oliverkirk-sudo/k230-c/project/cad/instrumented-reference/README.md

# Instrumented electrical reference, not the compact core

This frozen18-sheet variant preserves the added eight-rail voltage-monitor network and its conditional storage interlock. It has279 XML references /272 populated functional components, excluding DNP, logical edge and test-only points. CLI ERC is0, but this is only a schematic-model result. It is NOT demonstrated bootable or fabrication-ready; the qualification strap is DNP and storage is inhibited by default.

The rough dense area reservation is1231.56mm² versus1156mm² within the provisional2mm perimeter band. This topology is therefore not the selected38mm compact placement candidate. See ../integrated for the current compact candidate. No required decouplers were removed merely to improve this count.

Frozen source-generator copies are kept in frozen-generators; vendor evidence remains linked in the main project. The local review PDF/XML describe these saved bytes. Dynamic power failure, OTP, firmware, SI/PI and physical validation are not proved by ERC.
