oliverkirk-sudo/k230-c/project/cad/integrated/README.md

# 当前紧凑评审原理图 v8

打开 CMK230_Core_REVIEW.kicad_pro。18 页，246 个 XML 引用；另有 26 个排除 BOM/PCB 的电源来源声明。

全部 390 个 SoC 和 353 个存储器球位完成类型核对。最新 ERC 为 0，65 条 DDR 连接、131 个存储器供电/参考节点、62 个外露 GPIO 不变检查通过。电源声明只表达可追溯来源或底板必须提供的供电边界，不表达电压/时序已经合格。

R528 默认 DNP，存储禁止；尚未证明能启动。没有生产 PCB、叠层、半孔、SI/PI、热或实物测试。请读根目录 V7_COMPACT_REVIEW.md。

原理图内 NC 仅用于已核实不用的引脚，模拟参考类型有专门拓扑验证。VDDI 只连接稳定电容，不允许据输出类型作外供电。

本版采用缓冲复位，增加两个源参考MIPI去耦，关联NVT/晶体图纸候选封装。新提出的密闭75–85°C要求尚未满足；请读根目录V8_REVIEW.md和engineering/thermal/HIGH_TEMPERATURE_GATE.md。
