oliverkirk-sudo/k230-c/project/engineering/passive-resistor-candidates/README.md

# Remaining resistor candidates: bounded source review

2026-09-30. Audit of the high-temperature CM-K230 candidate, with 38 × 38 mm, top-only components, 140 edge pins, 1 GB LPDDR4 and 16 GB eMMC retained. The provisional 85°C enclosed-air target is **not** a verified resistor/PCB temperature. The initial source audit made no CAD/population/purchase changes. Subsequently authorized HT-DRAFT13 implements only U14 as a Schmitt OR and R33=270k; the classifications below retain the explicitly frozen pre-change input. See the current [implementation validation](../../cad/high-temp-candidate/u14-or-validation.json) for that adopted candidate.

The frozen input contains 61 resistor references: 19 already assigned precision parts and **42 unassigned positions**. The latter divide into **35 ordinary nonzero resistors, two precision startup-selection resistors and five role-specific zero links**. Three of the 42 are DNP. [Per-reference classification](per-reference-classification.json) records every value, net, candidate and remaining gate. [Calculations](static-screen.json) are reproducible with `python engineering/passive-resistor-candidates/calculate_screen.py`; they use the frozen [input extract](input-snapshot.json) and the project's static regulator bounds.

**U14 follow-on gate:** the43 kΩ R33 proposal below is a static-load correction only. [The input-slew addendum](U14_SLEW_ADDENDUM.md) finds an unclosed10 ns/V LVC input requirement and evaluates the already-reviewed AUP97 as a correctly wired Schmitt OR, with a separate270 kΩ output-pullup proposal. Do not adopt R33 alone as full acceptance of U14.

## Family, temperature and land geometry

Vishay **CRCW0201 e3**, document 20052, is a credible *layout candidate* for these ordinary values. Specify **F tolerance / K TCR**: ±1% initial and ±100 ppm/K, supported over **47 Ω–1 MΩ**. The ±200 ppm/K ±1% range is 10 Ω–10 MΩ; 1–9.76 Ω has asymmetric −200/+400 ppm/K. Do not accidentally substitute the N-code 200 ppm grade for the K-code candidate. Schema-derived ED candidates used here are CRCW02014K70FKED, CRCW020110K0FKED, CRCW020122K0FKED, CRCW020143K0FKED, CRCW020147K0FKED, CRCW0201100KFKED and CRCW02011M00FKED. Stock and lifecycle were not verified. [Vishay pp1–2](https://www.vishay.com/docs/20052/crcw0201e3.pdf)

The family specifies −55…155°C operation, 30 V limiting element voltage and 50 mW at 70°C. Its graph decreases linearly to zero at 155°C: **41.18 mW at 85°C, 29.41 mW at 105°C and 17.65 mW at 125°C**. These graph readings require the manufacturer's PCB/thermal conditions and film ≤155°C; 85°C enclosure air does not prove them. Working voltage also remains limited by √(P·R). The worst proposed ordinary full-rail DC illustration is R204 at 5.5 V across 9 kΩ: **3.361 mW**. Actual hot spots, PCB heat flow, pulses and source voltage still need review.

The source drawing was visually checked: body **0.60±0.03 × 0.30±0.03 × 0.23±0.03 mm**, two **0.28 × 0.43 mm** copper pads, **0.23 mm inner gap**, pad centers ±0.255 mm, **0.79 × 0.43 mm total copper envelope**. A 1.1 × 0.7 mm planning box provides only 0.155/0.135 mm per-side allowance beyond copper. A hypothetical 0.05 mm mask expansion plus 0.25 mm clearance instead gives **1.39 × 1.03 mm**, rounded outward to 1.4 × 1.1 mm. Neither clearance convention is manufacturer assembly approval; mask, paste, placement and inspection capability remain open. These are source dimensions, not permission to assign a generic 0201 footprint.

## Accuracy is an acceptance requirement, not a lifetime model

This report deliberately tests **±10% total resistance** for ordinary candidates. It is a required acceptance interval spanning initial tolerance, temperature, assembly, aging and environment, **not a guaranteed CRCW life specification**. Vishay permits ±(2%R+0.1 Ω) change in the 70°C/1000 h endurance test and ±(4%R+0.1 Ω) at 8000 h; 155°C/1000 h upper-category endurance permits ±(2%R+0.1 Ω), and soldering heat permits ±(1%R+0.05 Ω). These are different prescribed tests. They cannot be added and relabeled as a guaranteed arbitrary mission lifetime. At 100 ppm/K, a 20→125°C excursion alone corresponds to 1.05% resistance change. Mission duration, humidity, film temperature, mounting shift and process still need an actual acceptance plan. [Vishay pp1,3–4](https://www.vishay.com/docs/20052/crcw0201e3.pdf)

**R205/R206 are excluded from that interval.** TI's startup selection table specifies 56.2 kΩ with ±1% accuracy for 0.8 V/address 0x49. TNPW0402 supports 56.2 kΩ at ±0.1%/10 ppm/K; candidate **TNPW040256K2BYED** can use the separately reviewed source-land footprint. The existing conditional **±0.70% total** acceptance gives 55.8066–56.5934 kΩ, inside TI's 55.638–56.762 kΩ band. It remains a total mission-profile requirement, not an automatic life guarantee. [TI Table8-1 p12](https://www.ti.com/lit/ds/symlink/tps62864.pdf), [Vishay p3](https://www.vishay.com/docs/28758/tnpw_e3.pdf), [existing footprint review](../../cad/verified-footprints/passive-candidates/README.md)

## Important static checks and proposed nominal changes

Use static rail bounds 1V8 = **1.764476615–1.836094613 V** and 3V3 = **3.245129532–3.392164299 V**. Distribution drop, ripple, dynamic load, PCB leakage and supply ramps are additional requirements. Comparisons to Nexperia Schmitt thresholds below retain its **discrete 1.65 V supply test point**, rather than claiming guaranteed interpolation over the actual 1V8 rail.

| Network | Result at the stated total resistance band | Remaining interpretation |
|---|---|---|
| R527, 10 kΩ raw PG | 9–11 kΩ; conservative sink ≤379.007 µA versus U89's 400 µA point, leaving 20.993 µA. High loss ≤23.1 mV at 2.1 µA leakage; high ≥3.222030 V | Sink reserve must also cover board leakage. Common low ceiling 0.4 V gives 70 mV against tabulated VT− minimum0.47 V. PG leakage is tabulated at5 V; actual-node application remains conditional |
| R530, 100 kΩ delay-node pullup | 90–110 kΩ; 1.05 µA ×110 kΩ =115.5 mV loss; high ≥1.648977 V, **338.977 mV** above VT+ maximum1.31 V | Only U90 leakage0.3 µA and U91 input0.75 µA are counted. No SoC pin load belongs on this node. Low current <22 µA; timing and full-supply behavior remain open |
| R529, 100 kΩ inhibit pulldown | 0.75 µA ×110 kΩ =82.5 mV, leaving **387.5 mV** to the discrete0.47 V low threshold | R528 stays DNP; this does not approve enabling storage |
| R31, 10 kΩ mode pulldown | Two TMUX inputs plus one LVC input:9 µA ×11 kΩ =99 mV; **351 mV** below TMUX0.45 V VIL | Valid powered-control state; JP1 remains cold-only |
| R32, 10 kΩ global-disable pullup | Released high ≥3.137880 V with9.75 µA leakage; ≥1.137880 V margin to LVC VIH2.0 V. Sink bound <386 µA | AUP06 loaded0.39 V low leaves60 mV to TMUX VIL, still a discrete supply-point check |
| R61/R62, 10 kΩ LPDDR4 ODT_CA pulls | Micron4 µA leakage produces44 mV maximum drop; same-local-VDD2 high margin ≥231.204 mV to0.75 VDD2 | Preserve rank/ODT configuration and validate local rail distribution |

Sources: [TPS3808 p6](https://www.ti.com/lit/ds/symlink/tps3808.pdf), [TPS6282x p5](https://www.ti.com/lit/ds/symlink/tps62827.pdf), [74AUP1G97 pp6–8](https://assets.nexperia.com/documents/data-sheet/74AUP1G97.pdf), [74AUP1G17 pp5–7](https://assets.nexperia.com/documents/data-sheet/74AUP1G17.pdf), [74AUP1G06 pp5–7](https://assets.nexperia.com/documents/data-sheet/74AUP1G06.pdf), [TMUX1574 p6](https://www.ti.com/lit/ds/symlink/tmux1574.pdf), [Micron LPDDR4 Tables153/170 pp223/234](https://www.mouser.com/datasheet/2/671/200b_z00m_sdp_ddp_auto_lpddr4_lpddr4x-3193603.pdf)

**Propose R563–R570 = 43 kΩ, replacing 47 kΩ.** Micron permits DAT pullups10–50 kΩ. Existing47 kΩ at±10% reaches **51.7 kΩ**, failing the upper bound by1.7 kΩ. Proposed43 kΩ spans **38.7–47.3 kΩ**, leaving2.7 kΩ upper reserve. R562 CMD22 kΩ spans19.8–24.2 kΩ within4.7–50 kΩ; R34 reset10 kΩ spans9–11 kΩ within4.7–50 kΩ; R573 DS47 kΩ spans42.3–51.7 kΩ within10–100 kΩ. These are resistance-window checks, not complete bus timing/logic acceptance. [Micron eMMC Table13 p27](https://e2e.ti.com/cfs-file/__key/communityserver-discussions-components-files/234/EMMC_5F00_DATASHEET.pdf)

**Propose R33 = 43 kΩ, replacing 10 kΩ.** The netlist confirms only R33, **U14.Y pin4 and U13.EN pin13** on DISABLE_OR_TF. At125°C, TI's3 V/16 mA LVC output row allows VOL0.5 V, exceeding TMUX VIL0.45 V; the present10 kΩ load is too large for the stronger light-load guarantee. With43 kΩ±10%, worst current is3.392164 V/38.7 kΩ +2 µA = **89.653 µA**, below the **100 µA** test row that guarantees VOL≤0.1 V over1.65–5.5 V. This leaves **350 mV low margin** and10.347 µA additional sink-load reserve. With a valid high output, VOH≥VCC−0.1 V gives≥3.145130 V, or **1.945130 V margin** to TMUX VIH1.2 V; the only sink input is2 µA and the pullup helps.

The LVC source explicitly lists Ioff≤25 µA at125°C, VCC=0 and VI/VO=5.5 V. If that is accepted as a bound at this actual3V3 node, adding2 µA TMUX leakage gives a hypothetical released high≥**1.968030 V**, margin768.030 mV. That voltage extension is conditional. U14 VCC and the R33 pullup are physically on the **same VDD_3V3 net**; an independently live pullup with U14 unpowered is not a normal stable circuit state. Neither Ioff nor this calculation establishes behavior during their common ramp, rail collapse or partial power. The proposed correction closes the stated **valid-supply** source-table margin. [TI RevW pp6–7, visually checked](https://www.ti.com/lit/ds/symlink/sn74lvc1g32.pdf), [TMUX RevC p6](https://www.ti.com/lit/ds/symlink/tmux1574.pdf)

## Roles that still need electrical closure

- **R216–R219, 4.7 kΩ private I2C:** at±10%, R=4.23–5.17 kΩ. TPS62864 specifies VIH1.0 V, VIL0.4 V and SCL/SDA leakage0.2/0.1 µA. Regulator-input high margins are respectively **0.763443 V−5170Ω·Iunknown** and **0.763960 V−5170Ω·Iunknown**, where Iunknown includes PMU/board sink leakage and any internal pulldown. The official pinout establishes PMU type and AVDD1P8_LDO domain for all four pads; it does not prove general-IO numerical limits apply. Even provisionally using generic K230 VOL0.45 V leaves **−50 mV** against TI's0.4 V input ceiling. TI's2 mA SDA/SCL rating is an **absolute maximum**, not a guaranteed VOL/IOL drive specification. Complete bidirectional DC margin is unresolved. Ideal30–70% RC ceilings at5.17 kΩ are228.3 pF/68.48 pF/27.39 pF for1000/300/120 ns; actual bus capacitance, firmware timing and internal pulls must be verified. [TI pp5–8](https://www.ti.com/lit/ds/symlink/tps62864.pdf), [Canaan pinout](https://kendryte-download.canaan-creative.com/developer/k230/HDK/K230%E7%A1%AC%E4%BB%B6%E6%96%87%E6%A1%A3/K230_PINOUT_V1.2_20240822.xlsx), [K230 manufacturer-authored datasheet pp29–30](https://atta.szlcsc.com/upload/public/pdf/source/20240304/CED0BDC8B8BEDC72BFC23F1C8A2ED83A.pdf), [TI RC equation](https://www.ti.com/lit/an/slva689/slva689.pdf)
- **R203:** released-high leakage drop is66 mV using five0.1 µA EN loads plus0.1 µA PG leakage. Low current is modest, but the published PG VOL0.4 V equals downstream EN VIL0.4 V, giving **zero guaranteed DC noise margin**. Resistor tolerance alone does not resolve it. **R204** input-leakage drop is1.1 mV at its11 kΩ maximum. [TPS6282x p5](https://www.ti.com/lit/ds/symlink/tps62827.pdf), [TPS62864 p6](https://www.ti.com/lit/ds/symlink/tps62864.pdf)
- **R43:** known0.75 µA Schmitt leakage gives371.977 mV high margin to the discrete1.31 V threshold; C45, carrier and PCB leakage must fit the remaining **3.382 µA** static sink budget and the RC timing requirement
- **R41/R42:**1 MΩ is supported by the100 ppm family, but crystal startup/gain/drive are not resistance-range checks. **R44–R47** boot sampling/internal pulls/carrier ownership and **R402** PMU pin limits remain open; preserve R45/R47 DNP
- **R571/R572:** retain as physical candidates only. Exact eMMC CLK/K230 strobe input limits and disabled-switch states need closure. A provisional10 µA K230 leakage assumption across R572's110 kΩ would raise its node to1.1 V, above0.35×1V8min≈0.618 V; the existing100 kΩ cannot be called a guaranteed low from that generic model

## Zero links remain role-specific

Keep **R220 WSL060300000ZEA9** and **R561 WFZ040200000ZE66** under their [existing independent power-link reviews](../mechanical/passive-small-parts-review.md). Do not substitute commodity0201.

**R221** may retain CRCW02010000Z0ED as a *conditional* layout option: the Canaan50 mA VDD3P3_SD budget would cause2.5 mV drop and0.125 mW at50 mΩ. This is a SoC supply branch, not the TF card's main feed. The CRCW jumper's1 A rating is explicitly at70°C; hot resistance/current, peak/inrush and branch drop remain unqualified. Do not infer a125°C current rating from a resistor power graph alone.

**R528**, still DNP, is a low-current logic strap: if deliberately fitted, the known100 kΩ pulldown/input path draws at most≈21.151 µA at the stated corners. CRCW02010000Z0ED is a role-specific physical candidate; populating it would still require the separate boot-voltage qualification decision. **R401** remains selection-deferred until actual PMU input/internal-pull current, firmware input ownership and local ramp are checked. A0 Ω connection to its own domain does not permit firmware to drive that pin low.

This audit establishes candidate family compatibility, source land dimensions and bounded calculations. It does not establish full-board fit, full-supply logic, timing, assembly capability, lifetime, thermal performance or production qualification.
