oliverkirk-sudo/k230-c/project/engineering/mechanical/passive-hot-enclosure-review.md

# Passive and regulator thermal constraints in the sealed enclosure

2026-09-30. The user reports a sealed enclosure with a 75–85°C maximum, while the design lead is clarifying whether this refers to surrounding air or a component surface. This distinction is unresolved. It does not establish a safe local capacitor, inductor or regulator temperature.

**Do not adopt the conditional X5R area optimization under this unresolved condition.** The recovered smaller X5R parts are archived research candidates only. Their 85°C component-temperature limit is not an 85°C ambient allowance with self-heating. Retain the X7R/125°C review path, and evaluate actual hot spots before a package reduction.

## Source-backed limits

| Component group | Manufacturer limit or condition | Consequence for this module |
|---|---|---|
| TPS62864 CPU/KPU converters | Recommended junction range −40…125°C; continuous 4 A above 105°C junction reduces lifetime | If local air is 85°C, only 20°C junction rise reaches the published lifetime-warning threshold at continuous 4 A; 40°C rise reaches recommended maximum. Actual load and duty cycle matter. |
| TPS6282xA fixed converters | Recommended junction range −40…125°C | The 150°C absolute maximum and thermal shutdown are not continuous design targets. At 85°C local air the recommended-range budget is 40°C, before margin. |
| Murata DFE201612E inductors | −40…125°C **including self-heating**; ΔT≤40°C | 85°C local air plus the full specified rise reaches 125°C with no remaining temperature margin. Rated thermal currents were measured on Murata's six-layer test board, not this crowded module. |
| Murata DFE201610E inductors | 125°C operating limit including self-heating; current criteria differ for inductance drop and temperature rise | L24–L26's 4.8 A inductance-drop number must not replace the 3.6 A thermal criterion. Keep thermal qualification open. |
| Coilcraft XEL3520 | Up to 125°C ambient with its stated 40°C-rise Irms condition; maximum part temperature 165°C | This has a different temperature definition from Murata's 125°C part limit. TI-listed 0.47 µH XEL3520-471MEC remains a possible L21 candidate, subject to application losses, board cooling and 2.0 mm height. |
| BLM15PX121SN1D ferrite | 2.0 A at 85°C derated to 1.1 A at 125°C; recommended copper width depends on foil thickness/current | Follow current-temperature and copper constraints at actual local temperature. Nine nominal impedance matches do not establish nine acceptable hot-spot placements. |
| X7R MLCC candidates | Nominal temperature characteristic extends to 125°C | This leaves temperature range to assess, not a guarantee of effective capacitance under combined DC bias, AC ripple, tolerance, aging and production variation. |

TI gives materially different junction-to-ambient thermal figures on JEDEC and EVM boards: TPS62864 91.8 versus 56.5°C/W; TPS6282x 129.5 versus 71.4°C/W. These are evidence that PCB construction matters. Do not use either value as the measured thermal resistance of the 38×38 mm sealed module or derive an approved continuous-current limit from it.

## Changes that remain conditional

- Replacing L21's low-resistance XFL4015 with DFE201612E-R47M can save 13.96 mm² in a reservation scenario, but raises maximum room-temperature DCR from 8.36 to 26 mΩ. At an illustrative 4 A DC, the latter contributes 0.416 W before ripple/AC loss and hot-DCR increase. This is not an accepted trade in the sealed enclosure.
- The alternative TI-listed XEL3520-471MEC saves only 3.94 mm² with the conservative reservation and has 10.85 mΩ maximum DCR, much closer to the original. Its thermal-current figures still require real-board validation; no replacement is approved here.
- A single large input capacitor on a TPS6282xA rail may satisfy the 3 µF effective-capacitance floor but still fail ripple-current or thermal requirements. The optional single-input area scenario therefore needs input-ripple, ESR heating, hot-loop and load-transient review. It is not a recommendation to remove parts merely to fit.
- Do not infer that the memory devices' 85°C case-temperature limit qualifies them at 85°C enclosure air. The lead owns memory grade/package selection and any resulting BGA envelope changes.

## Concrete next evidence needed

Establish the temperature reference point and duration, actual rail continuous/peak loads, enclosure heat path and final board stackup. Then bound or measure component surface/junction temperatures under simultaneous worst-case workload. Capacitance release requires a warranted or qualified combined-condition minimum rather than a typical DC-bias curve multiplied by unverified margins. Placement must preserve the hot loops and local bypass distances, even when rectangle area sums are favorable.

Sources visually checked: [TPS62864 datasheet](https://www.ti.com/lit/ds/symlink/tps62864.pdf), p5; [TPS6282x datasheet](https://www.ti.com/lit/ds/symlink/tps62827.pdf), p4; [Murata DFE201612E specification](https://search.murata.co.jp/Ceramy/image/img/P02/J%28E%29TE243A-0006.pdf), pp2/4/7; [Coilcraft XEL3520](https://www.coilcraft.com/getmedia/585e5286-b75b-4755-99e9-56d067dcf62b/xel3520.pdf), p1; Murata BLM15 specification and exact capacitor sources are linked with hashes in the companion passive reports. All manufacturer originals remain outside the distributable project.
