oliverkirk-sudo/k230-c/project/engineering/power/POWER_DESIGN_CN.md

# 六路电源候选实现与剩余工作

已落实6个降压器，CORE、CPU、KPU分开；两路可调CPU/KPU均0.8V冷启动。没有为区分I2C地址而提高冷启动电压。完整针脚矩阵与Ti资料复核通过，但不是硬件或热审核。

## 固定轨
- CORE：TPS62827A，4A；33.2k/100k、0.6V基准得到0.7992V
- DDR IO：TPS62826A，3A；84.5k/100k得到1.107V，处于1.1V域的规格范围，须计入公差/纹波
- 1.8V：TPS62825A，2A；200k/100k得到1.8V
- 3.3V：TPS62826A，3A；453k/100k得到3.318V
这些是名义值。0.1%分压电阻不能消除稳压器基准误差。采用厂商所述100k下臂对应120pF前馈电容；0.47µH参考电感、47µF名义输出电容及输入2×10µF。有效输出必须≥10µF、有效输入≥3µF，不能用丝印容量代替带偏压/温度/公差的实值。

## CPU/KPU动态轨
两路TPS628640BYCGR，各4A，56.2k 1%启动电阻，均0.8V及地址0x49。0.24µH参考电感、3×22µF输出、2×10µF输入；有效输出≥30µF、输入≥8µF。开关SW三球属于同一内部输出，库中C1为power_out、C2/C3为passive表示同一物理驱动，矩阵强制三球同网，不是三路稳压器并联。

两条独立软件I2C总线避免地址冲突：CPU用GPIO65/66，KPU用GPIO67/69，各有1.8V上拉4.7k；它们均未占用140针里的GPIO2–63。还必须完成PMU pad复用、屏蔽相应唤醒源、避免关机驱动重占，以及真正开漏的方向切换。现BSP的write(1)不能直接当成开漏释放；见internal-pmu-i2c-review.md。尚未提供可直接刷入的调压固件。

VSET/PG是故障时高至VIN、正常由启动电阻拉低的复用引脚，与通常开漏PG相反。图中仅连接启动电阻，不加载为常规PG控制。新增负载或过大电容会影响启动电压/地址采样。

## 顺序与滤波
CORE的开漏PG由100k拉到VIN_5V，并控制其余降压器EN，Ti明确支持此类顺序连接；它不是完整的所有电源正常控制器。

RTC与PMU LDO两个SoC电源脚改为同一个AVDD1P8_PMU滤后网络，避免两个独立滤波支路的上升先后不确定。CORE先于1.8V/3.3V的设计路径已经画出，但板级上升/掉电/棕断、CPU/KPU状态、系统复位和存储开通仍要统筹。

DDR CORE通过最大50mΩ的0Ω连接，400mA时可产生20mV压降；再叠加基准/电阻误差、走线和纹波，必须仍高于0.744V。模拟域120Ω@100MHz磁珠给出了最大直流电阻约束，但这不是噪声/谐振验证。近芯片本地去耦另页给出初始分配，正面放置与回流路径尚未设计。

## 文档与验证
TI：https://www.ti.com/lit/ds/symlink/tps62827.pdf 及 https://www.ti.com/lit/ds/symlink/tps62864.pdf 。实际工作点的电感峰值/饱和、MLCC有效容量、环路、散热、5V输入裕量和38mm布局都没有测量或仿真通过。完整PG/复位/存储开通逻辑未冻结，不能据此制板。
