oliverkirk-sudo/k230-c/project/engineering/storage/SELECTOR_DESIGN_CN.md

# 存储二选一：已连接的候选隔离子电路

用户已允许eMMC/TF二选一。默认16GB eMMC，断开全部电源后设置模式；不热切换，不占用或重定义140针中的GPIO。这里落实了隔离子电路，整体核心板仍未完成。

## 新文件与检查
- `cad/storage/CMK230_Storage_Selector_CANDIDATE.kicad_sch`：可编辑KiCad子电路，3个真实型号多路开关、1个OR门、模式焊接跳线、偏置和去耦
- `switch-pin-net-matrix.csv`与`switch-netlist.xml`：71项器件针脚/网络对应
- `switch-connectivity-test.json`：4种MODE/全局禁用状态通过静态导通图检查；不是SPICE、时序、SI或实测
- CLI成功导出原理图、网表；预览已目视检查。独立子电路ERC为30错误/0警告：28个仅有本页端点的未接外围标签、2个尚无上游供电源的网络。这些没有通过NC或PWR_FLAG掩盖

## 电路选择
U11/U12/U13采用TMUX1574RSVR候选（RSV UQFN针号，不能套用PW/DYY针号）。U11/U12切换CLK、CMD、DAT0..3；U12另一路把eMMC复位端在eMMC模式连至主控复位源、TF模式钳至GND。该复位不作为总线隔离成立的前提，因eMMC复位功能还涉及器件配置。

U13负责DAT4..7：SEL固定0，其EN由U14输出GLOBAL_DISABLE OR MODE_TF。TF模式整颗U13关闭，从而隔离全部高位数据线；其未使用B端按厂商建议接地，不会在正常TF模式将主控输出接地。U12剩余一路三端均接地。

JP1默认开路，R31=10k下拉使MODE_TF=0，选eMMC。全部断电后闭合JP1得到TF模式。R32/R33使禁用信号默认高。R34=10k从eMMC_RSTN上拉到VEMMC_IO，避免全局禁用时复位浮空；VEMMC_IO须与器件IO电源一致。TF复位钳位的标称电流为0.18mA或0.33mA，不是含公差的最大值。U14候选SN74LVC1G32DBVR采用3.3V逻辑供电；上游GLOBAL_DISABLE必须是与此域兼容的硬件信号，不能假定任意1.8VGPIO可直接驱动。C31–C34各100nF，最终位置/型号仍待布局。

eMMC VCC和VCCQ在两种模式都保持供电，避免新增电源开关和未供电器件反灌路径；TF模式11条与主控相关路径全部隔离。代价是eMMC待机功耗。外部TF的3.3V供电和上拉由底板合同处理；未选分支仍可能带电，因此必须遵守开关电源、信号绝对额定值及上电顺序。

## 厂商证据与约束
TI开关资料：https://www.ti.com/lit/ds/symlink/tmux1574.pdf
它是双向模拟开关，不是电平转换器；3.3V供电可承载所需1.8/3.3V信号。断电保护限值3.6V不能当作任意过压保护。2GHz典型带宽、导通电容7.5pF典型/12pF最大、导通电阻2Ω典型/4.5Ω最大，不等于本板HS200已合格。仍需主控到存储完整通道的眼图、延迟、偏斜、负载和训练验证。
TI逻辑门资料：https://www.ti.com/lit/ds/symlink/sn74lvc1g32.pdf

## 必须在BootROM执行前解决的门槛
GLOBAL_DISABLE目前明确是未完成的硬件集成输入，不是已经存在的控制器。不能等U-Boot运行后再开通用来加载U-Boot的存储路径；那会循环依赖。需要在ROM第一次访问存储前由已验证的硬件电源/复位/电压策略释放开关。

K230的VDD3P3_SD按资料仍是3.3V电源，不能切换成1.8V。运行期软件通过HOST_CONTROL2/PHY设置1.8V信号，不等于改变外部电源。TRM控制器复位字段为3.3V，但未证明ROM首次驱动时仍是这个状态；ROM可能先修改它。BOOT标签在资料间有差异，不能把MODE_TF直接绑到BOOT0/BOOT1。

当前HS200候选中eMMC VCCQ=1.8V、TF起始3.3V；若初期驱动电压不匹配，可能损坏或不能启动。因此此子电路尚不可投板运行。需确认ROM最早电压/启动选择和异常复位行为，随后完成硬件GLOBAL_DISABLE发生电路。

## 较保守性能路线的评估（尚未选用）
所选eMMC支持3.3V VCCQ。固定3.3V并取消HS200、按8bit HS52设计，可降低“主控初期3.3V直达固定1.8V器件”的风险。接口原始传输上限由约200MB/s降至约52MB/s，实际文件性能不等于此上限。此路线是性能变更，需要用户选择，当前没有偷偷采用。ROM若改成1.8V后访问3.3V器件仍可能失败，因此也不是绕过ROM验证的万能解决方案。

## 后续释放条件
核实ROM/PHY及异常复位 → 完成上游电源/复位/禁用发生器 → 确认两种启动镜像与模式对应 → 完整器件封装审核 → 总线SI与HS200/SD速度测试。当前未生成此子电路PCB、器件贴片位置或可制造Gerber。

独立复核确认：RSV及DBV针号正确；原69项网络与新增R34两项一致；总71项匹配KiCad导出网表，四种模式/禁用逻辑均通过。GLOBAL_DISABLE需要3.3V有效逻辑（U14高门限至少2.0V）或额定耐3.3V的开漏源，不能接1.8V推挽输出。
