oliverkirk-sudo/k230-c/project/COMPACT_README.md

# v12 精简评审包

这是完整v12存档的精简副本，用于直接下载。电路、引脚、BOM候选、KiCad可编辑文件、工具、原始出处/哈希、回归结果、几何审计及未完成事项均保留。当前HT-DRAFT13原理图PDF保留。

主要省略重复的历史PDF、试验渲染和图片；逐个文件及原始哈希见compact-content-manifest.json。保留的GUI截图是原来的v9高温分支/v11局部eMMC试验，不能当作HT-DRAFT13的新GUI测试。完整v12存档保留全部图片证据。

某些历史冻结清单包含已省略图片，其完整清单校验应在完整存档中执行；不要把精简包缺少渲染当作新的CAD错误。精简内容没有更改任何原始工程字节。它仍不能生产：R528默认DNP、存储禁止，主PCB未完成放置/布线，DDR现有搜索被拒绝。请先阅读V12_CORE_REVIEW.md。
