oliverkirk-sudo/k230-c/project/docs/release-gates.md

# 释放门槛与验证计划

当前：D0接口/架构评审；没有内部原理图完成、布线完成或制造通过。

## G1 电气兼容合同
- 140个接口除名称外，逐针填写方向、电压、绝对最大值、默认上下拉、启动复用、内部串阻/ESD、电源掉电行为及底板要求
- 优先解决6组BANK_VDDIO、两组输出电源、BOOT0/1、RSTN、USB ID/VBUS感测、模拟输入/输出
- 审核模块符号BANK5_IO62/63等原始命名，不能擅自改针号；SoC球号需官方引脚表/原理图双人核对
- 样品连续性/测量可补充证据，但带电测量须使用限流和相应探头；未知bank禁止直接注入3.3V

## G2 可执行内部原理图
- 完整料号/最新资料、K230/DRAM/eMMC逐球连接矩阵和封装尺寸通过审核
- 电源负载、瞬态、效率、热、电源输出给底板的预算与裕量完成；不是仅通过ERC
- 上电/掉电/棕断顺序、默认启动态、DVFS接口完成；禁止未受控并联稳压输出
- DDR训练参数与物理换位一致，bootloader/BSP版本冻结
- 每个电源脚/去耦/NC/保留脚有明确处置；ERC完成且所有剩余告警有签署解释

## G3 布局与制造
- 确认实际板厚、半孔孔径/环宽/镀层、边缘位置、公差、阻焊/焊膏、表面处理、拼板、测试和钢网
- 板厂确认叠层与阻抗；BGA逃线和同面去耦可行；背面元件数=0
- 审核DDR封装延迟+PCB延迟、通道内交换、参考面、过孔数和串扰；电源完整性与热审核
- 原理图与PCB网表一致；DRC、间距、铜到边缘、半孔专用工艺审核；不能将底板SMD焊盘直接用于核心板制板
- 完成独立设计审查后才生成Gerber/钻孔/BOM/CPL，现包未提供这些文件

## G4 样板上电与功能
1. 不装底板先检查外观、短路、BGA焊接与电源对地阻值；限流分阶段上电
2. 示波器同时记录CORE/1.8/3.3/DDR/RESET等关键电源与释放关系；确认峰值和纹波，不能只用万用表
3. 确认24MHz/RTC时钟、串口恢复/USB下载、BOOT选择和复位重复性
4. 验证1GB容量与地址边界；全地址/数据模式内存压力测试、冷热启动、目标频率和温度覆盖；记录训练日志
5. 验证eMMC容量识别、EXT_CSD、HS200、读写完整性、擦写/分区与断电恢复；容量显示与出厂预留区分开
6. 用原CM-K230底板逐项检查GPIO-bank电平、UART/I2C/SPI/SD、USB host/device、各CSI/DSI通道、ADC/audio及供电负载
7. 对比原板启动、接口行为、异常掉电/复位、长时AI负载和热。通过后再声称“功能兼容”

## 本包已运行的检查
- 140/140针脚：原符号与底板PDF独立一致；原始重复电源名称保留
- 140个底板焊盘被KiCad读取；原始位置/大小/旋转数字转换保存
- KiCad9接口原理图SVG导出成功，已目视检查；这不是内部原理图ERC
- PCB只有四条38mm边界及警示文字，没有铜/孔/器件/连线；不是DRC合格产品

- 本次接口黑盒ERC实际输出139条未连接引脚错误、0警告；这是未接内部电路的草稿，不是ERC通过。未以NC标记掩盖这些未完成连接。
