oliverkirk-sudo/k230-c/project/engineering/CORE_AUX_CN.md

# K230时钟、复位与启动偏置：参考电路落图

新增`cad/core-aux/CMK230_Clock_Reset_REFERENCE.kicad_sch`，15个器件、37项针脚/网络；KiCad导出网表逐项匹配，独立片段ERC为0错误/0警告，预览已检查。U1仅表示7个已知系统球，不是完整390球SoC，不能据此宣称核心板ERC通过。

## 已按一手参考落实
Canaan CanMV-K230 V1.0_2023-09-15原理图第1页（不同于01Studio同名板第1页）：RTC B12/A12，24MHz B8/A8，RSTN B9，BOOT0 C8，BOOT1 C9。
- 两组晶体反馈电阻参考1MΩ；四个晶体负载电容参考12pF
- 24MHz四脚参考连接：1/3晶体端，2/4地；最终器件封装必须逐脚一致，不能仅凭“3225”选封装
- RTC采用两脚无源晶体网络
- RSTN参考上拉100kΩ至1.8V、100nF至GND；保留模块外部复位同名网络

## 本项目的明确差异
通用CanMV板的默认启动偏置不能直接当成CM-K230。本片段提出BOOT0低、BOOT1高，对应硬件指南的MMC0基线；相反方向偏置电阻DNP。外部BOOT接口仍保留。此提案不解决BootROM对SD/eMMC电压和类别的实际识别，不把MODE_TF自动连接到BOOT引脚。

## 参数可留待布局/验证，不假装已经冻结
晶体完整料号尚未冻结。官方LP4参考BOM的候选是YXC X322524MOB4SI与Epson X1A000141000500；更换来源或后缀须复核CL、ESR、驱动等级、容差和温度。Epson官方系列资料：https://download.epsondevice.com/td/pdf/app/FC-135R_en.pdf 。不能用频率一样代替这些参数相同。

12pF是参考值，不是新板已校准值。对两个负载电容，近似CL=C1×C2/(C1+C2)+寄生电容；两个12pF只贡献约6pF，剩余取决于封装/引脚/布线。实际布局后按所选晶体负载、寄生估算及测量调整，检查负阻裕量、起振、频率与温度。

100k/100nF的RC时间常数为10ms，但实际复位释放时刻取决于阈值和供电上升过程。它不是多电源PG监控器，不能代替独立电源顺序/棕断设计。

## 仍需补全
K230其余383球、所有电源/地及去耦、未使用/测试球的处置、DDR/接口其他单元及板级连接还没有在本片段中实现。后续合并必须将片段U1统一为完整SoC多单元符号，不能把这些独立评审页当成多个K230。

补充源区分：Canaan版本的RTC有1MΩ反馈电阻R1，01Studio版本的RTC图没有画此电阻。本工程RTC1MΩ来自Canaan版本；24MHz反馈两版均有。Y2具体厂家候选的全温度/老化精度和85°C等级仍需重新审查，不能由初始±10ppm推断总误差≤20ppm。
