oliverkirk-sudo/k230-c/project/engineering/erc-triage-v5.md

# CM-K230 remaining ERC triage, v5 review baseline

Date: 2026-09-30 UTC. Scope: read-only electrical-rule triage and manufacturer/source review. This review did not edit CAD, generators, electrical pin types, NC markers, or ERC exclusions, and added no PWR_FLAG.

## Latest export reconciliation (v6)

The newer export **2026-09-30T03:58:42-0700** was separately read after source-backed pin dispositions, traced source modeling, and pin-type corrections. It contains **14 violations: 13 errors and 1 warning**. Exact current records are in `erc-triage-v6-current.csv`; source hashes/counts are in `erc-triage-v6-current-summary.json`.

The former 19 passive-source ERC errors are now addressed with traceable CAD-only source declarations after a verified upstream-connection graph. Those were ERC-model semantics, not unresolved wiring. Qualification gates remain separately tracked. No declaration was added to VEMMC_IO or the six bank nets. Accurate host-strobe input typing exposes one additional real input-drive error; it shares the already known strobe disposition with the dangling label.

| Current endpoint | Actual issue | Recommended disposition |
| --- | --- | --- |
| U1.B6 MMC0_STROBE | warning / global_label_dangling / SPEC | Retain warning until earliest boot/reset pad policy is established. No fabricated connection to H5, arbitrary grounding, or intrinsic-NC type. |
| U1.B6 MMC0_STROBE | error / pin_not_driven / SPEC | Retain warning until earliest boot/reset pad policy is established. No fabricated connection to H5, arbitrary grounding, or intrinsic-NC type. |
| U1.B11 GPIO70/OUT0 | error / pin_not_connected / SPEC | Keep unresolved until an explicit PMU startup or independently justified bypass/isolation strategy is selected and proved. Verify private regulator-control GPIO access, reset, wake and power-off paths. Do not apply blanket unused flags or arbitrary bias changes. |
| U1.C10 GPIO64/INT0 | error / pin_not_connected / SPEC | Keep unresolved until an explicit PMU startup or independently justified bypass/isolation strategy is selected and proved. Verify private regulator-control GPIO access, reset, wake and power-off paths. Do not apply blanket unused flags or arbitrary bias changes. |
| U1.C11 GPIO71/OUT1 | error / pin_not_connected / SPEC | Keep unresolved until an explicit PMU startup or independently justified bypass/isolation strategy is selected and proved. Verify private regulator-control GPIO access, reset, wake and power-off paths. Do not apply blanket unused flags or arbitrary bias changes. |
| U1.C12 GPIO68/INT4 | error / pin_not_connected / SPEC | Keep unresolved until an explicit PMU startup or independently justified bypass/isolation strategy is selected and proved. Verify private regulator-control GPIO access, reset, wake and power-off paths. Do not apply blanket unused flags or arbitrary bias changes. |
| U1.H6 VDDIO_BANK3 | error / power_pin_not_driven / SPEC | Resolve module/carrier supply ownership, permitted bank voltage and sequencing before adding any internal rail tie. Preserve six distinct banks; do not force all to 3.3 V just to silence ERC. |
| U1.K7 VDDIO_BANK1 | error / power_pin_not_driven / SPEC | Resolve module/carrier supply ownership, permitted bank voltage and sequencing before adding any internal rail tie. Preserve six distinct banks; do not force all to 3.3 V just to silence ERC. |
| U1.M7 VDDIO_BANK4 | error / power_pin_not_driven / SPEC | Resolve module/carrier supply ownership, permitted bank voltage and sequencing before adding any internal rail tie. Preserve six distinct banks; do not force all to 3.3 V just to silence ERC. |
| U1.R11 VDDIO_BANK2 | error / power_pin_not_driven / SPEC | Resolve module/carrier supply ownership, permitted bank voltage and sequencing before adding any internal rail tie. Preserve six distinct banks; do not force all to 3.3 V just to silence ERC. |
| U1.D8 ANA_TS_VTEST | error / pin_not_connected / UNUSED | Leave open with ERC error until reviewer accepts unused-output disposition. If accepted, document this particular output and retain output/functional type; do not ground or mark intrinsic NC. |
| U1.R13 VDDIO_BANK0 | error / power_pin_not_driven / SPEC | Resolve module/carrier supply ownership, permitted bank voltage and sequencing before adding any internal rail tie. Preserve six distinct banks; do not force all to 3.3 V just to silence ERC. |
| U1.R15 VDDIO_BANK5 | error / power_pin_not_driven / SPEC | Resolve module/carrier supply ownership, permitted bank voltage and sequencing before adding any internal rail tie. Preserve six distinct banks; do not force all to 3.3 V just to silence ERC. |
| U3.C6 VDD | error / power_pin_not_driven / REAL | Complete the VCCQ feed only after cold-mode/first-drive voltage policy is proved. The selected HS200 mode requires 1.8 V VCCQ; do not simply connect 3.3 V or a power flag. Retain the separate fixed 3.3 V flash supply. |

The final count must be re-exported if D8 is subsequently accepted as an unused output or any other endpoint changes. The original 51-row baseline below remains fully accounted for and is not the current unresolved count.

## Result

Every one of the baseline **51 violations (50 errors, 1 warning)** is listed below and in `erc-triage-v5.csv`. This is a frozen review of the **post-eMMC-supply-correction, pre-unused-pin-disposition** export at **2026-09-30 03:51:17-0700 (10:51:17 UTC)**. Later generator runs change UUIDs and may implement the dispositions; the hashes below identify exactly what was reviewed. Do not present this baseline count as a newer export's result.

| Primary class | Count | Meaning |
| --- | ---: | --- |
| REAL | 1 | Actual missing electrical source: corrected eMMC VCCQ/VEMMC_IO |
| UNUSED | 20 | Source-backed unused-pin classifications, with D8 unused-output reviewer acceptance retained |
| POWER | 19 | An explicit source/return path exists across passive elements or the external edge contract; ERC cannot propagate power_out through those boundaries |
| SPEC | 11 | Six carrier bank supply contracts, four PMU startup/isolation endpoints, and host strobe reset-time input policy |

The 20 UNUSED entries are **9 balls marked NC in both LP3/LP4, 5 LP3-functional balls unused in LP4, 4 unused rank1 CS/CKE functions, D8 analog output, and H5 HS400 output**. “UNUSED” is a review classification, not a statement that all are already annotated or approved. D8 unused-output acceptance remains open in this baseline. All four PMU endpoints are SPEC, because a default pull-down does not create the documented cold-start event or demonstrate the required domain-isolation transition. The separate MMC0_STROBE warning remains SPEC because its reset bias is not proved safe by runtime firmware.

## Highest-consequence findings

### eMMC rail-name reversal was real and is corrected in this snapshot

The original inspected v4 generator assigned Samsung **VDD to VDD_3V3** and **VDDF to VEMMC_IO**. Exact Samsung part-family documentation, page 4 table 1 and page 5, specifies **VDD = VCCQ (interface/controller)** and **VDDF = VCC (flash)**. The intended fixed-1.8-V HS200 I/O mode therefore made that mapping erroneous. The parent corrected the mapping during this review; this frozen XML now puts C6/M4/N4/P3/P5 on VEMMC_IO and E6/F5/J10/K9 on VDD_3V3. The corrected VEMMC_IO net is still source-less. Merely correcting names or adding power flags cannot make storage operational.

### H5 is legitimately unused for HS200; B6 still needs a pad policy

Samsung's H5 Data Strobe is a device-generated HS400 output. It is not required by the selected K230 HS200 path. H5 should not be wired around the three-switch isolation architecture merely to reduce ERC. An intentional-unused output annotation is supportable for a firmware-enforced HS200-only design. It is not an intrinsic NC ball.

K230 B6 MMC0_STROBE is an **input**, per official pinout row 28. The TRM, PDF page 963, gives STBPAD_CNFG at PHY+0xA a reset value of 0x0440; WEAKPULL_EN[4:3] resets to 0, meaning neither pull is enabled. CanMV U-Boot programs field value 2 (pull-down) for both the SD and eMMC pad modes, but only after code reaches pad initialization. This does not establish BootROM or reset-time behavior. Preserve the warning until that policy is verified. Do not borrow a TI host's internal-pull guarantee, ground B6 arbitrarily, or call B6 a physical NC.

### K230 unused analog pins require individual treatment

U6 MIPI_ATB has explicit manufacturer guidance permitting floating when unused (official pinout row 506 and Hardware Design Guide MIPI section). It was already handled before this baseline, so it is not one of the 51 violations.

D8 ANA_TS_VTEST is an **output** in official pinout row 78 and TRM section 2.10.6. The Canaan reference page 1 and 01studio page 1 leave it open; the actual endpoint was visually checked. That supports a reference-level unused-output disposition, subject to reviewer acceptance. It does not justify grounding it or changing it to an intrinsic no-connect type. No generic rule permitting every unused K230 analog pin to float was found. The guide's permission to omit supplies for an unused peripheral is also not an exemption for ADC/CODEC interfaces required by the replacement-module contract.

### PMU cold start is a specification dependency, not harmless spare I/O

TRM section 14.3, PDF p1169, identifies PAD64/INT0 long-press or PAD68/INT4 high level as the cold-start event. PAD70 then enables external power, PAD71 releases reset about 50 ms later, and Normal-to-PMU isolation is removed about 60 ms after PAD70 enables. PMU-to-Normal access also requires sysctl ISO control. The official default-state sheet specifies pull-down on all four current open PMU pins. Leaving INT0 and INT4 open does not provide either trigger. The present externally enabled regulators may power the CPU independently, but that does not prove PMU-domain access or the private PMU-GPIO regulator buses operate. Keep C10/C12/B11/C11 as unresolved endpoints until the startup or bypass/isolation strategy is demonstrated. Do not infer safe unused status solely from a reference board's open pads.

### PAD68 automatic-start candidate and timing correction

The default register fields support **active-high level detection** on PAD68/INT4/C12, rather than requiring a later rising edge:

| Register | Reset / relevant field | Interpretation |
| --- | --- | --- |
| PMU_INT_DETECT_EN, offset 0x004C | 0x810, bit 4 = 1 | INT4 detection enabled at reset |
| PMU_INT_DETECT_TYP, offset 0x0050 | 0x0, bit 5 = 0; bit 3 = 0 | INT4 effective level is high; detection is level-triggered |
| PMU_IO_CFG_4, offset 0x0090 | 0x1124 | PAD68 starts in PMU function with input enabled, output disabled and pull-down enabled |
| PMU_INT0_TO_CTL_REGISTER / PMU_INT1_TO_CTL_REGISTER | offsets 0x0040/0x0044, reset 0xFFF; bit 4 = 1 | INT4 participates in the reset-default OR routing to PAD70/PAD71 control |
| PMU_OUT_DELAY_SET, offset 0x007C | 0x01100640 | PAD70 event delay disabled; PAD71 logic delay enabled, nominal 0x640 32-kHz ticks |
| PMU_NORMAL_TIMER_VAL, offset 0x00A0 | 0x780 | Nominal 60-ms core-stability/isolation timer |

Evidence: TRM PDF pp1172-1176 and pp1179-1181. C12's official supply domain is AVDD1P8_LDO, which is now on the shared AVDD1P8_PMU filtered domain. A pull-up from that same domain is a plausible automatic-start candidate. No resistor value or new wire is approved by this review: input VIH, internal pull-down tolerance, power-rise behavior, permitted leakage, startup/shutdown control ownership, and private regulator-bus access need verification. Do not pull it to 3.3 V, arbitrarily reinterpret it as NC, or assume a permanent high produces a complete safe power sequence.

The actual TRM **cold-reset flow figure on PDF p1183**, visually inspected, includes **about 1000 ms for initial PMU oscillator stabilization** before waiting for a wake event, then nominal 50 ms for core clock/POR stability and about 9 ms of hardware boot. These are descriptive timings, not complete guaranteed min/max limits. The section 14.3 narrative places both the approximately 50-ms PAD71 reset release and approximately 60-ms Normal-to-PMU isolation removal relative to PAD70 enabling; it does **not** justify adding them into a fixed 110-ms reset delay. A fixed 110-ms delay from rail rise also ignores the initial oscillator step. Use a proved readiness/reset strategy and verified worst-case timing in the next design stage.

The Canaan and 01studio reference page-1 PMU regions were visually checked: both leave C12, C10, B11 and C11 unconnected. They do not provide a precedent for a PAD68 pull-up, nor prove that the new private PMU-GPIO I2C regulator scheme works with those pins open. The reference designs can inform topology without being substituted for the new design's startup/isolation validation. Current CAD remains frozen at the separately verified 14-violation export above.

### Mode-specific non-use is not an intrinsically NC package pin

The official pinout identifies the nine DDR balls C20/D19/D20/F18/G17/H18/H19/M17/N18 as NC in both LP3 and LP4. K20/L17/L18/L20/M20 instead have LP3 CA/ODT functions and are unused only in LP4; M20's historical DDR_NA spelling is resolved by the official DDR_CA2_NC entry. Preserve the functional identity and explicit LP4 mode on those five.

J17/J19/P18/T19 are real rank1 CKE/CS functions. The official LP4 Figure 3-12 leaves them open. The chosen Samsung device's page 10 ballout and page 11 block diagram expose only one CS/CKE pair per channel: H4/J4 for A and R4/P4 for B. The existing 65-net mapping connects those through rank0. If intentional-unused markers are applied, retain functional pin types and ensure firmware does not enable a second rank. Do not infer non-use just because a multi-mode name contains “NC”.

## Source and reproducibility

`erc-triage-v5-source-evidence.json` contains author-written factual pin dispositions, exact workbook sheet/row references, verified source URLs, and hashes. It does not redistribute the vendor workbook, PDFs, or rendered vendor pages. Samsung documents are manufacturer-authored, but the public hosts below are third-party mirrors.

| Source | Exact evidence used |
| --- | --- |
| [K230_PINOUT](https://kendryte-download.canaan-creative.com/developer/k230/HDK/K230%E7%A1%AC%E4%BB%B6%E6%96%87%E6%A1%A3/K230_PINOUT_V1.2_20240822.xlsx) | Main pin sheet rows recorded per issue; default-state sheet rows 66/70/72/73 |
| [K230_GUIDE](https://www.kendryte.com/k230/en/main/00_hardware/K230_Hardware_Design_Guide.html) | MMC0 HS200 capabilities; LP4 Figure 3-12; MIPI_ATB floating; bank rails and startup ordering |
| [K230_TRM](https://kendryte-download.canaan-creative.com/developer/k230/HDK/K230%E7%A1%AC%E4%BB%B6%E6%96%87%E6%A1%A3/K230_Technical_Reference_Manual_V0.3.1_20241118.pdf) | Section 2.10.6 identifies D8 output; PDF p963 specifies host strobe reset/pull fields |
| [SAMSUNG_EMMC](https://datasheet.lcsc.com/lcsc/2007011825_Samsung-KLMAG1JETD-B041_C499919.pdf) | pp4-5 supply meanings and exact ball sets; pp5/23 HS400 strobe |
| [SAMSUNG_LP4](https://www.szyuda88.com/home/8/a/2lhtb2/resource/2021/05/26/60ade38424a32.pdf) | pp10-11 exact CS/CKE endpoints and two-channel device topology |
| [CANMV_UBOOT](https://github.com/canmv-k230/u-boot/blob/87041d630cdcd545dacfec19f1e90a093689dada/drivers/mmc/snps_sdhci.c) | Runtime pull-down programming, not reset/BootROM evidence |
| [CANAAN_REFERENCE](https://github.com/kendryte/k230_docs/blob/main/zh/00_hardware/CanMV_K230/CanMV-K230-V1.0_2023-09-15.pdf) | p1 actual D8 open endpoint and PMU reference topology |

### Frozen input hashes

- `build_review.py`: `4c4810ea4ac58035bac72c8bdc2d2f91613e463a3a53db052860322b1a4452e0`
- `open-pin-review.csv`: `506f5f5e3ad9bdc641fb7476f2eb055d8d44f0563152a58bc396d4fd6f801b46`
- `master-pin-assignments.csv`: `2d86d789d0b26d9e9a779ee7c474f10b498eef613ca425dfbc21e1b8de2a3508`
- `master.xml`: `e64cf95a6809c521e7f59032c080213eb6f6a784172e44096a77d82b2e4c109a`
- `erc.json`: `4addb3718373637725c10eb0fd72e294c00dec7a0efbcbd5ab6a4f730f480f8c`

## Complete issue ledger

The issue IDs below follow the stored ERC sheet/violation order. CSV additionally contains the exact reported item UUID, full net membership and source-action explanation. Unconnected exported net names are shown as “open” for readability; the exact names remain in the CSV. Each undriven-power ERC item represents a net group, not merely the displayed first power pin. All 26 groups were traced independently.

| ID | Severity / check | Sheet / endpoint | Net | Class / finding | Required next step |
| --- | --- | --- | --- | --- | --- |
| ERC-001 | error / power not driven | /SoC_1/ U1.A13 VSS | GND | POWER / Passive external supply/return contract<br>J1.1/2/3/36/49/57/64/71/78/89/106 passive ground-return contract. Supply enters from the carrier; J1 is a logical module-edge contract with passive electrical types, not an on-board regulator. | Maintain explicit external input/return contract and qualify voltage/current/protection. Do not call this a missing internal supply wire or add a fabricated on-board source.<br>Evidence: Frozen KiCad master.xml and master-pin-assignments.csv; generate_power.py; module pinmap; TI TPS6282x/TPS62864 datasheets |
| ERC-002 | error / power not driven | /SoC_1/ U1.E9 AVDD3P3_USB | AVDD3P3_USB | POWER / Passive boundary, physical source path present<br>U26 -> L26 -> VDD_3V3 -> FB210.1/2 -> AVDD3P3_USB. The downstream net has no directly attached power_out pin because the source crosses passive pins. | A traceable CAD-only supply-source model is legitimate after verifying the upstream path. Keep real inductor/filter pins passive, exclude model-only declarations from fabrication/BOM, and forbid declarations on unproved nets. Sequencing, ripple, current, capacitance and thermal qualification remain separate.<br>Evidence: Frozen KiCad master.xml and master-pin-assignments.csv; generate_power.py; module pinmap; TI TPS6282x/TPS62864 datasheets |
| ERC-003 | error / power not driven | /SoC_1/ U1.E10 VDD3P3_SD | VDD3P3_SD | POWER / Passive boundary, physical source path present<br>U26 -> L26 -> VDD_3V3 -> R221.1/2 (0 ohm) -> VDD3P3_SD. The downstream net has no directly attached power_out pin because the source crosses passive pins. | A traceable CAD-only supply-source model is legitimate after verifying the upstream path. Keep real inductor/filter pins passive, exclude model-only declarations from fabrication/BOM, and forbid declarations on unproved nets. Sequencing, ripple, current, capacitance and thermal qualification remain separate.<br>Evidence: Frozen KiCad master.xml and master-pin-assignments.csv; generate_power.py; module pinmap; TI TPS6282x/TPS62864 datasheets |
| ERC-004 | error / power not driven | /SoC_1/ U1.E11 VDD1P8 | VDD1P8 | POWER / Passive boundary, physical source path present<br>U25.5 SW_1V8 -> L25.1/2 -> VDD1P8. The downstream net has no directly attached power_out pin because the source crosses passive pins. | A traceable CAD-only supply-source model is legitimate after verifying the upstream path. Keep real inductor/filter pins passive, exclude model-only declarations from fabrication/BOM, and forbid declarations on unproved nets. Sequencing, ripple, current, capacitance and thermal qualification remain separate.<br>Evidence: Frozen KiCad master.xml and master-pin-assignments.csv; generate_power.py; module pinmap; TI TPS6282x/TPS62864 datasheets |
| ERC-005 | error / power not driven | /SoC_1/ U1.F9 AVDD1P8_USB | AVDD1P8_USB | POWER / Passive boundary, physical source path present<br>U25 -> L25 -> VDD1P8 -> FB205.1/2 -> AVDD1P8_USB. The downstream net has no directly attached power_out pin because the source crosses passive pins. | A traceable CAD-only supply-source model is legitimate after verifying the upstream path. Keep real inductor/filter pins passive, exclude model-only declarations from fabrication/BOM, and forbid declarations on unproved nets. Sequencing, ripple, current, capacitance and thermal qualification remain separate.<br>Evidence: Frozen KiCad master.xml and master-pin-assignments.csv; generate_power.py; module pinmap; TI TPS6282x/TPS62864 datasheets |
| ERC-006 | error / power not driven | /SoC_1/ U1.F12 VDD0P8_CORE | VDD0P8_CORE | POWER / Passive boundary, physical source path present<br>U21.5 SW_CORE -> L21.1/2 -> VDD0P8_CORE. The downstream net has no directly attached power_out pin because the source crosses passive pins. | A traceable CAD-only supply-source model is legitimate after verifying the upstream path. Keep real inductor/filter pins passive, exclude model-only declarations from fabrication/BOM, and forbid declarations on unproved nets. Sequencing, ripple, current, capacitance and thermal qualification remain separate.<br>Evidence: Frozen KiCad master.xml and master-pin-assignments.csv; generate_power.py; module pinmap; TI TPS6282x/TPS62864 datasheets |
| ERC-007 | error / power not driven | /SoC_1/ U1.F14 AVDD1P8_LDO | AVDD1P8_PMU | POWER / Passive boundary, physical source path present<br>U25 -> L25 -> VDD1P8 -> FB206.1/2 -> AVDD1P8_PMU (U1 F14/F15 together). The downstream net has no directly attached power_out pin because the source crosses passive pins. | A traceable CAD-only supply-source model is legitimate after verifying the upstream path. Keep real inductor/filter pins passive, exclude model-only declarations from fabrication/BOM, and forbid declarations on unproved nets. Sequencing, ripple, current, capacitance and thermal qualification remain separate.<br>Evidence: Frozen KiCad master.xml and master-pin-assignments.csv; generate_power.py; module pinmap; TI TPS6282x/TPS62864 datasheets |
| ERC-008 | error / power not driven | /SoC_1/ U1.G11 AVDD0P8_PLL | AVDD0P8_PLL | POWER / Passive boundary, physical source path present<br>U21 -> L21 -> VDD0P8_CORE -> FB202.1/2 -> AVDD0P8_PLL. The downstream net has no directly attached power_out pin because the source crosses passive pins. | A traceable CAD-only supply-source model is legitimate after verifying the upstream path. Keep real inductor/filter pins passive, exclude model-only declarations from fabrication/BOM, and forbid declarations on unproved nets. Sequencing, ripple, current, capacitance and thermal qualification remain separate.<br>Evidence: Frozen KiCad master.xml and master-pin-assignments.csv; generate_power.py; module pinmap; TI TPS6282x/TPS62864 datasheets |
| ERC-009 | error / power not driven | /SoC_1/ U1.G12 VDD0P8_CPU | VDD0P8_CPU | POWER / Passive boundary, physical source path present<br>U22.C1/C2/C3 SW_CPU -> L22.1/2 -> VDD0P8_CPU. The downstream net has no directly attached power_out pin because the source crosses passive pins. | A traceable CAD-only supply-source model is legitimate after verifying the upstream path. Keep real inductor/filter pins passive, exclude model-only declarations from fabrication/BOM, and forbid declarations on unproved nets. Sequencing, ripple, current, capacitance and thermal qualification remain separate.<br>Evidence: Frozen KiCad master.xml and master-pin-assignments.csv; generate_power.py; module pinmap; TI TPS6282x/TPS62864 datasheets |
| ERC-010 | error / power not driven | /SoC_1/ U1.H8 VDD0P8_KPU | VDD0P8_KPU | POWER / Passive boundary, physical source path present<br>U23.C1/C2/C3 SW_KPU -> L23.1/2 -> VDD0P8_KPU. The downstream net has no directly attached power_out pin because the source crosses passive pins. | A traceable CAD-only supply-source model is legitimate after verifying the upstream path. Keep real inductor/filter pins passive, exclude model-only declarations from fabrication/BOM, and forbid declarations on unproved nets. Sequencing, ripple, current, capacitance and thermal qualification remain separate.<br>Evidence: Frozen KiCad master.xml and master-pin-assignments.csv; generate_power.py; module pinmap; TI TPS6282x/TPS62864 datasheets |
| ERC-011 | error / power not driven | /SoC_1/ U1.H14 VDD1P1_DDR_IO | VDD1P1_DDR_IO | POWER / Passive boundary, physical source path present<br>U24.5 SW_DDR -> L24.1/2 -> VDD1P1_DDR_IO. The downstream net has no directly attached power_out pin because the source crosses passive pins. | A traceable CAD-only supply-source model is legitimate after verifying the upstream path. Keep real inductor/filter pins passive, exclude model-only declarations from fabrication/BOM, and forbid declarations on unproved nets. Sequencing, ripple, current, capacitance and thermal qualification remain separate.<br>Evidence: Frozen KiCad master.xml and master-pin-assignments.csv; generate_power.py; module pinmap; TI TPS6282x/TPS62864 datasheets |
| ERC-012 | error / power not driven | /SoC_1/ U1.K13 VDD0P8_DDR_CORE | VDD0P8_DDR_CORE | POWER / Passive boundary, physical source path present<br>U21 -> L21 -> VDD0P8_CORE -> R220.1/2 (0 ohm) -> VDD0P8_DDR_CORE. The downstream net has no directly attached power_out pin because the source crosses passive pins. | A traceable CAD-only supply-source model is legitimate after verifying the upstream path. Keep real inductor/filter pins passive, exclude model-only declarations from fabrication/BOM, and forbid declarations on unproved nets. Sequencing, ripple, current, capacitance and thermal qualification remain separate.<br>Evidence: Frozen KiCad master.xml and master-pin-assignments.csv; generate_power.py; module pinmap; TI TPS6282x/TPS62864 datasheets |
| ERC-013 | error / power not driven | /SoC_1/ U1.K15 VAA_DDR | VAA_DDR | POWER / Passive boundary, physical source path present<br>U25 -> L25 -> VDD1P8 -> FB204.1/2 -> VAA_DDR. The downstream net has no directly attached power_out pin because the source crosses passive pins. | A traceable CAD-only supply-source model is legitimate after verifying the upstream path. Keep real inductor/filter pins passive, exclude model-only declarations from fabrication/BOM, and forbid declarations on unproved nets. Sequencing, ripple, current, capacitance and thermal qualification remain separate.<br>Evidence: Frozen KiCad master.xml and master-pin-assignments.csv; generate_power.py; module pinmap; TI TPS6282x/TPS62864 datasheets |
| ERC-014 | warning / dangling label | /SoC_1/ U1.B6 MMC0_STROBE | MMC0_STROBE | SPEC / Unused HS200 input; reset bias unresolved<br>MMC0_STROBE has only U1.B6. HS200 does not consume an eMMC data-strobe signal, but the host pad is an input and its pull controls reset disabled. Runtime pull-down is not reset/BootROM proof. | Retain warning until earliest boot/reset pad policy is established. No fabricated connection to H5, arbitrary grounding, or intrinsic-NC type.<br>Evidence: K230 PINOUT r28; K230 guide MMC0; Samsung eMMC p5/p23; TRM PDF p963 STBPAD_CNFG; CanMV U-Boot snps_sdhci.c lines96-108,144-150 |
| ERC-015 | error / pin open | /SoC_2/ U1.C20 DDR_NC | open | UNUSED / NC in both LP3 and LP4<br>Official K230 pinout explicitly identifies this ball as NC in both supported external-DDR modes. | Source-backed no-use classification is supportable. Record exact ball/source and keep it electrically unused; no added wire.<br>Evidence: K230 PINOUT main pin sheet row 70, columns A/C/I; guide Figure3-12 |
| ERC-016 | error / pin open | /SoC_2/ U1.D19 DDR_NC | open | UNUSED / NC in both LP3 and LP4<br>Official K230 pinout explicitly identifies this ball as NC in both supported external-DDR modes. | Source-backed no-use classification is supportable. Record exact ball/source and keep it electrically unused; no added wire.<br>Evidence: K230 PINOUT main pin sheet row 89, columns A/C/I; guide Figure3-12 |
| ERC-017 | error / pin open | /SoC_2/ U1.D20 DDR_NC | open | UNUSED / NC in both LP3 and LP4<br>Official K230 pinout explicitly identifies this ball as NC in both supported external-DDR modes. | Source-backed no-use classification is supportable. Record exact ball/source and keep it electrically unused; no added wire.<br>Evidence: K230 PINOUT main pin sheet row 90, columns A/C/I; guide Figure3-12 |
| ERC-018 | error / pin open | /SoC_2/ U1.F18 DDR_NC | open | UNUSED / NC in both LP3 and LP4<br>Official K230 pinout explicitly identifies this ball as NC in both supported external-DDR modes. | Source-backed no-use classification is supportable. Record exact ball/source and keep it electrically unused; no added wire.<br>Evidence: K230 PINOUT main pin sheet row 128, columns A/C/I; guide Figure3-12 |
| ERC-019 | error / pin open | /SoC_2/ U1.G17 DDR_NC | open | UNUSED / NC in both LP3 and LP4<br>Official K230 pinout explicitly identifies this ball as NC in both supported external-DDR modes. | Source-backed no-use classification is supportable. Record exact ball/source and keep it electrically unused; no added wire.<br>Evidence: K230 PINOUT main pin sheet row 155, columns A/C/I; guide Figure3-12 |
| ERC-020 | error / pin open | /SoC_2/ U1.H18 DDR_NC | open | UNUSED / NC in both LP3 and LP4<br>Official K230 pinout explicitly identifies this ball as NC in both supported external-DDR modes. | Source-backed no-use classification is supportable. Record exact ball/source and keep it electrically unused; no added wire.<br>Evidence: K230 PINOUT main pin sheet row 196, columns A/C/I; guide Figure3-12 |
| ERC-021 | error / pin open | /SoC_2/ U1.H19 DDR_NC | open | UNUSED / NC in both LP3 and LP4<br>Official K230 pinout explicitly identifies this ball as NC in both supported external-DDR modes. | Source-backed no-use classification is supportable. Record exact ball/source and keep it electrically unused; no added wire.<br>Evidence: K230 PINOUT main pin sheet row 197, columns A/C/I; guide Figure3-12 |
| ERC-022 | error / pin open | /SoC_2/ U1.J17 DDR_CKEB1 | open | UNUSED / Unused rank1 functional output<br>This is a real second-rank CS/CKE function. The selected 200-ball Samsung device exposes one CS and CKE for each of channels A/B; rank0 is connected. Official LP4 reference leaves this rank1 endpoint open. | Record single-rank intentional non-use and rank1-disabled DDR configuration. Preserve functional pin type; never replace with intrinsic no_connect type.<br>Evidence: K230 PINOUT main pin sheet r239; guide Figure3-12; Samsung LP4 pp10-11; exact 65-net source table |
| ERC-023 | error / pin open | /SoC_2/ U1.J19 DDR_CSB1 | open | UNUSED / Unused rank1 functional output<br>This is a real second-rank CS/CKE function. The selected 200-ball Samsung device exposes one CS and CKE for each of channels A/B; rank0 is connected. Official LP4 reference leaves this rank1 endpoint open. | Record single-rank intentional non-use and rank1-disabled DDR configuration. Preserve functional pin type; never replace with intrinsic no_connect type.<br>Evidence: K230 PINOUT main pin sheet r241; guide Figure3-12; Samsung LP4 pp10-11; exact 65-net source table |
| ERC-024 | error / pin open | /SoC_2/ U1.K20 DDR_NC | open | UNUSED / LP4-mode unused functional pin<br>Official pinout identifies DDR_CA0_NC: active CA/ODT function in LP3, NC in LP4. Current part uses LPDDR4. | A mode-specific intentional-unused annotation is supportable. Preserve reusable functional pin type; do not call this intrinsically unbonded package NC.<br>Evidence: K230 PINOUT main pin sheet row 284, columns A/C/I; guide Figure3-12 |
| ERC-025 | error / pin open | /SoC_2/ U1.L17 DDR_NC | open | UNUSED / LP4-mode unused functional pin<br>Official pinout identifies DDR_CA3_NC: active CA/ODT function in LP3, NC in LP4. Current part uses LPDDR4. | A mode-specific intentional-unused annotation is supportable. Preserve reusable functional pin type; do not call this intrinsically unbonded package NC.<br>Evidence: K230 PINOUT main pin sheet row 325, columns A/C/I; guide Figure3-12 |
| ERC-026 | error / pin open | /SoC_2/ U1.L18 DDR_NC | open | UNUSED / LP4-mode unused functional pin<br>Official pinout identifies DDR_ODT_NC: active CA/ODT function in LP3, NC in LP4. Current part uses LPDDR4. | A mode-specific intentional-unused annotation is supportable. Preserve reusable functional pin type; do not call this intrinsically unbonded package NC.<br>Evidence: K230 PINOUT main pin sheet row 326, columns A/C/I; guide Figure3-12 |
| ERC-027 | error / pin open | /SoC_2/ U1.L20 DDR_NC | open | UNUSED / LP4-mode unused functional pin<br>Official pinout identifies DDR_CA1_NC: active CA/ODT function in LP3, NC in LP4. Current part uses LPDDR4. | A mode-specific intentional-unused annotation is supportable. Preserve reusable functional pin type; do not call this intrinsically unbonded package NC.<br>Evidence: K230 PINOUT main pin sheet row 328, columns A/C/I; guide Figure3-12 |
| ERC-028 | error / pin open | /SoC_2/ U1.M17 DDR_NC | open | UNUSED / NC in both LP3 and LP4<br>Official K230 pinout explicitly identifies this ball as NC in both supported external-DDR modes. | Source-backed no-use classification is supportable. Record exact ball/source and keep it electrically unused; no added wire.<br>Evidence: K230 PINOUT main pin sheet row 365, columns A/C/I; guide Figure3-12 |
| ERC-029 | error / pin open | /SoC_2/ U1.M20 DDR_NA | open | UNUSED / LP4-mode unused functional pin<br>Official pinout identifies DDR_CA2_NC: active CA/ODT function in LP3, NC in LP4. Current part uses LPDDR4. | A mode-specific intentional-unused annotation is supportable. Preserve reusable functional pin type; do not call this intrinsically unbonded package NC.<br>Evidence: K230 PINOUT main pin sheet row 368, columns A/C/I; guide Figure3-12 |
| ERC-030 | error / pin open | /SoC_2/ U1.N18 DDR_NC | open | UNUSED / NC in both LP3 and LP4<br>Official K230 pinout explicitly identifies this ball as NC in both supported external-DDR modes. | Source-backed no-use classification is supportable. Record exact ball/source and keep it electrically unused; no added wire.<br>Evidence: K230 PINOUT main pin sheet row 398, columns A/C/I; guide Figure3-12 |
| ERC-031 | error / pin open | /SoC_2/ U1.P18 DDR_CKEA1 | open | UNUSED / Unused rank1 functional output<br>This is a real second-rank CS/CKE function. The selected 200-ball Samsung device exposes one CS and CKE for each of channels A/B; rank0 is connected. Official LP4 reference leaves this rank1 endpoint open. | Record single-rank intentional non-use and rank1-disabled DDR configuration. Preserve functional pin type; never replace with intrinsic no_connect type.<br>Evidence: K230 PINOUT main pin sheet r438; guide Figure3-12; Samsung LP4 pp10-11; exact 65-net source table |
| ERC-032 | error / pin open | /SoC_2/ U1.T19 DDR_CSA1 | open | UNUSED / Unused rank1 functional output<br>This is a real second-rank CS/CKE function. The selected 200-ball Samsung device exposes one CS and CKE for each of channels A/B; rank0 is connected. Official LP4 reference leaves this rank1 endpoint open. | Record single-rank intentional non-use and rank1-disabled DDR configuration. Preserve functional pin type; never replace with intrinsic no_connect type.<br>Evidence: K230 PINOUT main pin sheet r499; guide Figure3-12; Samsung LP4 pp10-11; exact 65-net source table |
| ERC-033 | error / power not driven | /SoC_2/ U1.N6 AVDD0P8_MIPI | AVDD0P8_MIPI | POWER / Passive boundary, physical source path present<br>U21 -> L21 -> VDD0P8_CORE -> FB203.1/2 -> AVDD0P8_MIPI. The downstream net has no directly attached power_out pin because the source crosses passive pins. | A traceable CAD-only supply-source model is legitimate after verifying the upstream path. Keep real inductor/filter pins passive, exclude model-only declarations from fabrication/BOM, and forbid declarations on unproved nets. Sequencing, ripple, current, capacitance and thermal qualification remain separate.<br>Evidence: Frozen KiCad master.xml and master-pin-assignments.csv; generate_power.py; module pinmap; TI TPS6282x/TPS62864 datasheets |
| ERC-034 | error / power not driven | /SoC_2/ U1.N7 AVDD1P8_MIPI | AVDD1P8_MIPI | POWER / Passive boundary, physical source path present<br>U25 -> L25 -> VDD1P8 -> FB207.1/2 -> AVDD1P8_MIPI. The downstream net has no directly attached power_out pin because the source crosses passive pins. | A traceable CAD-only supply-source model is legitimate after verifying the upstream path. Keep real inductor/filter pins passive, exclude model-only declarations from fabrication/BOM, and forbid declarations on unproved nets. Sequencing, ripple, current, capacitance and thermal qualification remain separate.<br>Evidence: Frozen KiCad master.xml and master-pin-assignments.csv; generate_power.py; module pinmap; TI TPS6282x/TPS62864 datasheets |
| ERC-035 | error / pin open | /SoC_3/ U1.B11 GPIO70/OUT0 | open | SPEC / PMU startup/isolation policy unresolved<br>OUT0 is a PMU output with default pull-down. TRM p1169 makes PAD64 long-press or PAD68 high the cold-start source, followed by PAD70/PAD71 outputs and timed Normal-to-PMU isolation removal. Current open inputs provide no trigger; private PMU-GPIO I2C access cannot be assumed operational. | Keep unresolved until an explicit PMU startup or independently justified bypass/isolation strategy is selected and proved. Verify private regulator-control GPIO access, reset, wake and power-off paths. Do not apply blanket unused flags or arbitrary bias changes.<br>Evidence: K230 PINOUT main pin sheet r33; default-state sheet r72; TRM PDF p1169 section14.3 and PMU_NORMAL_TIMER_VAL p1180; K230 guide PMU |
| ERC-036 | error / pin open | /SoC_3/ U1.C10 GPIO64/INT0 | open | SPEC / PMU startup/isolation policy unresolved<br>INT0 is a PMU input with default pull-down. TRM p1169 makes PAD64 long-press or PAD68 high the cold-start source, followed by PAD70/PAD71 outputs and timed Normal-to-PMU isolation removal. Current open inputs provide no trigger; private PMU-GPIO I2C access cannot be assumed operational. | Keep unresolved until an explicit PMU startup or independently justified bypass/isolation strategy is selected and proved. Verify private regulator-control GPIO access, reset, wake and power-off paths. Do not apply blanket unused flags or arbitrary bias changes.<br>Evidence: K230 PINOUT main pin sheet r60; default-state sheet r66; TRM PDF p1169 section14.3 and PMU_NORMAL_TIMER_VAL p1180; K230 guide PMU |
| ERC-037 | error / pin open | /SoC_3/ U1.C11 GPIO71/OUT1 | open | SPEC / PMU startup/isolation policy unresolved<br>OUT1 is a PMU output with default pull-down. TRM p1169 makes PAD64 long-press or PAD68 high the cold-start source, followed by PAD70/PAD71 outputs and timed Normal-to-PMU isolation removal. Current open inputs provide no trigger; private PMU-GPIO I2C access cannot be assumed operational. | Keep unresolved until an explicit PMU startup or independently justified bypass/isolation strategy is selected and proved. Verify private regulator-control GPIO access, reset, wake and power-off paths. Do not apply blanket unused flags or arbitrary bias changes.<br>Evidence: K230 PINOUT main pin sheet r61; default-state sheet r73; TRM PDF p1169 section14.3 and PMU_NORMAL_TIMER_VAL p1180; K230 guide PMU |
| ERC-038 | error / pin open | /SoC_3/ U1.C12 GPIO68/INT4 | open | SPEC / PMU startup/isolation policy unresolved<br>INT4 is a PMU input with default pull-down. TRM p1169 makes PAD64 long-press or PAD68 high the cold-start source, followed by PAD70/PAD71 outputs and timed Normal-to-PMU isolation removal. Current open inputs provide no trigger; private PMU-GPIO I2C access cannot be assumed operational. | Keep unresolved until an explicit PMU startup or independently justified bypass/isolation strategy is selected and proved. Verify private regulator-control GPIO access, reset, wake and power-off paths. Do not apply blanket unused flags or arbitrary bias changes.<br>Evidence: K230 PINOUT main pin sheet r62; default-state sheet r70; TRM PDF p1169 section14.3 and PMU_NORMAL_TIMER_VAL p1180; K230 guide PMU |
| ERC-039 | error / power not driven | /SoC_3/ U1.H6 VDDIO_BANK3 | BANK3_VDDIO | SPEC / Carrier-supplied bank domain contract<br>U1 is connected to J1.123 on distinct BANK3_VDDIO, plus allocated decoupling. No internal feed exists. Carrier evidence ties these pads to its 3.3 V network, but original module internal direction/conditioning, backfeed and startup sequencing are not fully proved. | Resolve module/carrier supply ownership, permitted bank voltage and sequencing before adding any internal rail tie. Preserve six distinct banks; do not force all to 3.3 V just to silence ERC.<br>Evidence: master.xml; carrier-power-evidence.csv/json; K230 guide IO/power-up sequence; module-to-soc candidate contract |
| ERC-040 | error / power not driven | /SoC_3/ U1.K7 VDDIO_BANK1 | BANK1_VDDIO | SPEC / Carrier-supplied bank domain contract<br>U1 is connected to J1.136 on distinct BANK1_VDDIO, plus allocated decoupling. No internal feed exists. Carrier evidence ties these pads to its 3.3 V network, but original module internal direction/conditioning, backfeed and startup sequencing are not fully proved. | Resolve module/carrier supply ownership, permitted bank voltage and sequencing before adding any internal rail tie. Preserve six distinct banks; do not force all to 3.3 V just to silence ERC.<br>Evidence: master.xml; carrier-power-evidence.csv/json; K230 guide IO/power-up sequence; module-to-soc candidate contract |
| ERC-041 | error / power not driven | /SoC_3/ U1.M7 VDDIO_BANK4 | BANK4_VDDIO | SPEC / Carrier-supplied bank domain contract<br>U1 is connected to J1.23 on distinct BANK4_VDDIO, plus allocated decoupling. No internal feed exists. Carrier evidence ties these pads to its 3.3 V network, but original module internal direction/conditioning, backfeed and startup sequencing are not fully proved. | Resolve module/carrier supply ownership, permitted bank voltage and sequencing before adding any internal rail tie. Preserve six distinct banks; do not force all to 3.3 V just to silence ERC.<br>Evidence: master.xml; carrier-power-evidence.csv/json; K230 guide IO/power-up sequence; module-to-soc candidate contract |
| ERC-042 | error / power not driven | /SoC_3/ U1.R11 VDDIO_BANK2 | BANK2_VDDIO | SPEC / Carrier-supplied bank domain contract<br>U1 is connected to J1.90 on distinct BANK2_VDDIO, plus allocated decoupling. No internal feed exists. Carrier evidence ties these pads to its 3.3 V network, but original module internal direction/conditioning, backfeed and startup sequencing are not fully proved. | Resolve module/carrier supply ownership, permitted bank voltage and sequencing before adding any internal rail tie. Preserve six distinct banks; do not force all to 3.3 V just to silence ERC.<br>Evidence: master.xml; carrier-power-evidence.csv/json; K230 guide IO/power-up sequence; module-to-soc candidate contract |
| ERC-043 | error / pin open | /SoC_3/ U1.D8 ANA_TS_VTEST | open | UNUSED / Unused analog output; reference-level evidence<br>D8 is the temperature-sensor reference-voltage output, not an analog input. Both inspected board references leave it unconnected. No blanket unused-analog floating rule was found. | Leave open with ERC error until reviewer accepts unused-output disposition. If accepted, document this particular output and retain output/functional type; do not ground or mark intrinsic NC.<br>Evidence: K230 PINOUT main sheet r78; TRM section2.10.6; Canaan reference p1 (visually checked D8 endpoint); 01studio reference p1 |
| ERC-044 | error / power not driven | /SoC_3/ U1.F7 AVDD1P8_CODEC | AVDD1P8_CODEC | POWER / Passive boundary, physical source path present<br>U25 -> L25 -> VDD1P8 -> FB209.1/2 -> AVDD1P8_CODEC. The downstream net has no directly attached power_out pin because the source crosses passive pins. | A traceable CAD-only supply-source model is legitimate after verifying the upstream path. Keep real inductor/filter pins passive, exclude model-only declarations from fabrication/BOM, and forbid declarations on unproved nets. Sequencing, ripple, current, capacitance and thermal qualification remain separate.<br>Evidence: Frozen KiCad master.xml and master-pin-assignments.csv; generate_power.py; module pinmap; TI TPS6282x/TPS62864 datasheets |
| ERC-045 | error / power not driven | /SoC_3/ U1.F8 AVDD1P8_ADC | AVDD1P8_ADC | POWER / Passive boundary, physical source path present<br>U25 -> L25 -> VDD1P8 -> FB208.1/2 -> AVDD1P8_ADC. The downstream net has no directly attached power_out pin because the source crosses passive pins. | A traceable CAD-only supply-source model is legitimate after verifying the upstream path. Keep real inductor/filter pins passive, exclude model-only declarations from fabrication/BOM, and forbid declarations on unproved nets. Sequencing, ripple, current, capacitance and thermal qualification remain separate.<br>Evidence: Frozen KiCad master.xml and master-pin-assignments.csv; generate_power.py; module pinmap; TI TPS6282x/TPS62864 datasheets |
| ERC-046 | error / power not driven | /SoC_3/ U1.R13 VDDIO_BANK0 | BANK0_VDDIO | SPEC / Carrier-supplied bank domain contract<br>U1 is connected to J1.107 on distinct BANK0_VDDIO, plus allocated decoupling. No internal feed exists. Carrier evidence ties these pads to its 3.3 V network, but original module internal direction/conditioning, backfeed and startup sequencing are not fully proved. | Resolve module/carrier supply ownership, permitted bank voltage and sequencing before adding any internal rail tie. Preserve six distinct banks; do not force all to 3.3 V just to silence ERC.<br>Evidence: master.xml; carrier-power-evidence.csv/json; K230 guide IO/power-up sequence; module-to-soc candidate contract |
| ERC-047 | error / power not driven | /SoC_3/ U1.R15 VDDIO_BANK5 | BANK5_VDDIO | SPEC / Carrier-supplied bank domain contract<br>U1 is connected to J1.103 on distinct BANK5_VDDIO, plus allocated decoupling. No internal feed exists. Carrier evidence ties these pads to its 3.3 V network, but original module internal direction/conditioning, backfeed and startup sequencing are not fully proved. | Resolve module/carrier supply ownership, permitted bank voltage and sequencing before adding any internal rail tie. Preserve six distinct banks; do not force all to 3.3 V just to silence ERC.<br>Evidence: master.xml; carrier-power-evidence.csv/json; K230 guide IO/power-up sequence; module-to-soc candidate contract |
| ERC-048 | error / power not driven | /eMMC_1/ U3.C6 VDD | VEMMC_IO | REAL / Actual missing eMMC I/O supply source<br>Corrected VDD/VCCQ balls C6/M4/N4/P3/P5 and reset pull-up R34.2 are the entire net. No rail source, switch, link or regulator output is connected. | Complete the VCCQ feed only after cold-mode/first-drive voltage policy is proved. The selected HS200 mode requires 1.8 V VCCQ; do not simply connect 3.3 V or a power flag. Retain the separate fixed 3.3 V flash supply.<br>Evidence: Samsung eMMC pp4-5; corrected v5 master.xml; storage cold-mode/voltage review |
| ERC-049 | error / pin open | /eMMC_1/ U3.H5 Data_Strobe | open | UNUSED / Unused HS400 functional output in HS200 design<br>Exact Samsung datasheet assigns Data Strobe to device-generated HS400 read/CRC timing. The chosen host mode is HS200, so no external H5 strobe route is required. | Document HS200-only scope, make H5 an intentionally unused output if approved, preserve its functional pin identity, and prohibit HS400 firmware. Do not route it around the isolation selector.<br>Evidence: Samsung eMMC p5 and p23; K230 guide MMC0 capabilities |
| ERC-050 | error / power not driven | /eMMC_1/ U3.E6 VDDF | VDD_3V3 | POWER / Passive boundary, physical source path present<br>U26.5 SW_3V3 -> L26.1/2 -> VDD_3V3. The downstream net has no directly attached power_out pin because the source crosses passive pins. | A traceable CAD-only supply-source model is legitimate after verifying the upstream path. Keep real inductor/filter pins passive, exclude model-only declarations from fabrication/BOM, and forbid declarations on unproved nets. Sequencing, ripple, current, capacitance and thermal qualification remain separate.<br>Evidence: Frozen KiCad master.xml and master-pin-assignments.csv; generate_power.py; module pinmap; TI TPS6282x/TPS62864 datasheets |
| ERC-051 | error / power not driven | /Six_Rail_Power/ U21.6 VIN | VIN_5V | POWER / Passive external supply/return contract<br>J1.4/5/6 passive external 5 V input contract. Supply enters from the carrier; J1 is a logical module-edge contract with passive electrical types, not an on-board regulator. | Maintain explicit external input/return contract and qualify voltage/current/protection. Do not call this a missing internal supply wire or add a fabricated on-board source.<br>Evidence: Frozen KiCad master.xml and master-pin-assignments.csv; generate_power.py; module pinmap; TI TPS6282x/TPS62864 datasheets |

## Issues ERC does not prove away

- GLOBAL_DISABLE still lacks a validated pre-ROM release generator. Its pull-up creates a defined static disabled state, so an ordinary “unconnected” check need not flag the fact that the storage path never becomes usable. The selected bus must be enabled before the ROM reads the storage that loads later software.
- Source-less VEMMC_IO is only the visible part of the cold eMMC/TF voltage gate. Correct fixed flash VCC, first-drive signaling, no unselected-device exposure, reset collapse behavior and ROM boot-device support all need proof.
- The six bank nets are real carrier inputs in the candidate contract. A passive J1 pin does not itself prove module power direction, allowable backfeed, or the CORE-before-bank timing requirement. Keep them distinct until that contract is resolved.
- A passive path to a regulator is connectivity evidence only. Inductor/MLCC effective values, feedback accuracy, DCR drops, regulator headroom, enable/PG behavior, full startup/shutdown/brownout ordering, decoupling placement, SI/PI and thermal/current validation remain release gates.
- Most signal pins use conservative bidirectional review types. A clean(er) ERC would not constitute correct-direction, safe-voltage, high-speed timing, boot-firmware or fabrication sign-off.
- No footprints, PCB routing or manufactured electrical behavior were checked by this triage. Do not turn evidence-backed annotation into a claim of a fabrication-ready design.

## Completion checks

- 51 source records -> 51 ledger records, exactly once
- 50 error records and 1 warning record retained
- 24 unconnected physical endpoints, 26 undriven power groups, and 1 dangling label accounted for
- Every endpoint joined to actual KiCad-exported XML net membership
- eMMC VDD/VCCQ and VDDF/VCC exact ball sets rechecked against manufacturer page 5
- K230 official workbook and guide Figure 3-12 consulted for all DDR opens
- H5 mode-specific unused-output evidence separated from B6 reset-time input uncertainty
- No CAD edits, NC suppression or power flags performed by this review
