oliverkirk-sudo/k230-c/project/engineering/RELEASE_QUESTIONS_CN.md

# 当前释放条件与可继续工程项（v7 后更新）

容量、接口和断电存储二选一已确定，不必再问这些基线。当前条件式原理图已包含 PMU 自动启动、六路供电、PG/复位、默认存储禁止以及 TF 翻译分支；ERC 0 不能证明其已经启动或可生产。

## 首次安全启动前必须取得的外部证据

1. K230 固定 1.8 V SDIO0 OTP 配置如何保证 BootROM 首次驱动之前的电压；对应配置读回、0x91213410 的来源/有效时刻及 MMC0 TF 启动支持。已经在获得授权后接受官方工具协议并只读查看 1.8/3.3 V 选项；没有生成配置或烧录。表单默认值不能作硅片状态
2. 所选 eMMC C2 VDDI 在 1.8 V VCCQ 时的有效 CReg/ESR 要求。现有 2.2 µF+220 nF 是同基本料号、3.3 V VCCQ 实板参考，不能替代此保证
3. K230 B9 RSTN 的输入阈值、漏电、内部偏置和电源域；结合开漏缓冲器高阻输出漏电完成 100k 上拉释放预算

精确问题草稿见 VENDOR_QUESTIONS_CN.md，未对外发送。若取得书面资料或合格实测，可填入相应验证记录；单个样品实测不能替代所有温度/电压角落保证。

R528 维持 DNP，默认存储禁止。它是装配资格链接而非 OTP 检测器；不能仅凭软件日志、ERC 通过或工具默认值将其改为装配。

## 仍可自主继续的工程项

- 选择无源器件 MPN，核算有效容量、DCR、温升与精密电阻总误差，再做完整局部布局
- 完成 NVT4858 和三颗 BGA 生产焊盘、叠层/逃线/半孔工艺审查；原底板焊盘不能直接改称模块半孔
- 将固定主机电压与卡 OCR 分开，完成 U-Boot/RT-Smart 两种显式镜像策略；未经定义的自动模式探测不能替代硬件选择
- 对现有未限定位置的去耦重新做电源球位邻近布局/PDN 检查。243 个矩形无重叠只说明一次几何拼排存在

## 必须以 PCB/实物闭环的项目

PG/复位/保持供电边界、CPU/KPU 启动与 DVFS、DDR 训练、eMMC HS200、TF 25/50 MHz 信号链、外部 RSTN、时钟起振、所有 140 接口、SI/PI、热、EMC、制造和装配。紧凑 PG 方案不提供逐路严密欠压保护保证，仪器化八路监测版本另行保留。

没有外部发送、采购、OTP 写入或制造操作获本文件授权。
