oliverkirk-sudo/k230-c/project/engineering/VENDOR_QUESTIONS_CN.md

# 完成启动/存储电路前需要的准确答复

此文件是可交给芯片技术支持的技术问题草稿；尚未发送给任何外部人员。

## 致 Canaan / K230 技术支持

设计为外置1GB LPDDR4，MMC0通过断电模式选择连接16GB eMMC或TF；目标保持eMMC HS200。请给出：

1. 对非SiP K230，MMC0在BootROM首次驱动CLK/CMD/DAT前的信号电压，如何受空白/已编程OTP SDIO0配置影响？请提供默认值、合法配置、复位与首次驱动的保证。我们不会凭运行时HOST_CTRL2复位值推断ROM行为
2. U-Boot中读取0x91213410并判断低2位的字段，由哪个阶段/模块设置？其完整编码、有效时刻、对应OTP字段与读取方法是什么？不需要给生产芯片执行不可逆写入的指令，首先需要规范
3. 同一不可逆 OTP 配置下，物理 MMC0 是否自动识别 SD 与 eMMC 启动协议？硬件指南将启动脚描述为 MMC0/MMC1，TRM 则写 eMMC/SD；请明确是控制器选择还是协议锁定。两种运行时镜像不能解决 ROM 阶段问题。

4. 固定1.8V MMC0主机、eMMC1.8V VCCQ、TF分支专用固定1.8↔3.3V转换器，是否是支持的SD卡启动拓扑？MMC0时钟反馈/采样调整是否允许转换器延迟？目标为原有证据支持的Default/High-Speed25/50MHz，不要求UHS；请提供此拓扑的启动及采样延时限制。
5. eMMC HS200模式下MMC0_STROBE不使用时，芯片输入在BootROM之前允许浮空吗？若需外部偏置，请给允许值/电压域。TRM STBPAD_CNFG复位0x0440显示弱上下拉都未使能，不能用U-Boot后续下拉替代此说明
6. 同域上拉PAD68实现自动PMU启动时，所需偏置电阻、有效VIH、内部下拉、上电时序和电源域要求是什么？PAD70/PAD71、外部RSTN与PMU/Normal隔离释放之间，哪些时序可以用于外部复位使能？私有GPIO65/66/67/69应在何时可访问？

7. 请给出B9 RSTN在所有相关电源/温度条件下的VIH/VIL、输入漏电、内部上下拉和电源域。该信息用于100k上拉的释放高电平预算；不能从普通GPIO指标推断。

## 致 Samsung eMMC 技术支持

器件KLMAG1JETD-B041，153FBGA，VCC=3.3V，目标VCCQ=1.8V/HS200。请确认C2 VDDI内部稳压节点所需CReg有效电容量、容差、ESR范围、额定电压和放置约束；1.8V VCCQ时是否仍需该电容，是否允许不装。已找到OLIMEX同基本料号KLMAG1JETD-B041003、3.3V VCCQ参考板采用2.2µF+220nF，但不能据此保证本设计1.8V VCCQ条件。请确认确切型号与电压模式的规范。

以上资料缺口与最终PCB/硬件验证相互独立。即使取得答复，仍需正式原理图审查、封装/叠层/阻抗、SI/PI、热和实测。
