oliverkirk-sudo/k230-c/project/engineering/pmu/startup-pin-net-matrix.csv

reference | part | pin | net
R401 | 0R PMU AUTO-START STRAP | 1 | AVDD1P8_PMU
R401 | 0R PMU AUTO-START STRAP | 2 | PMU_INT4_AUTO_START
R402 | 10k INT0 INACTIVE | 1 | PMU_INT0
R402 | 10k INT0 INACTIVE | 2 | GND
TP81 | PMU OUT0 OBSERVE ONLY | 1 | PMU_OUT0_STATUS
TP82 | PMU OUT1 OBSERVE ONLY | 1 | PMU_OUT1_STATUS
