oliverkirk-sudo/k230-c/project/engineering/power/power-pin-net-matrix.csv

reference | part | pin | net
U21 | TPS62827ADMQ | 1 | CORE_ENABLE
U21 | TPS62827ADMQ | 2 | CORE_PGOOD_5V
U21 | TPS62827ADMQ | 3 | FB_CORE
U21 | TPS62827ADMQ | 4 | GND
U21 | TPS62827ADMQ | 5 | SW_CORE
U21 | TPS62827ADMQ | 6 | VIN_5V
L21 | 0.47uH XFL4015-471MEB REF | 1 | SW_CORE
L21 | 0.47uH XFL4015-471MEB REF | 2 | VDD0P8_CORE
C201 | 47uF X7R / Ceff>=10uF | 1 | VDD0P8_CORE
C201 | 47uF X7R / Ceff>=10uF | 2 | GND
R201 | 33.2k total_error<=0.15% | 1 | VDD0P8_CORE
R201 | 33.2k total_error<=0.15% | 2 | FB_CORE
R202 | 100k total_error<=0.15% | 1 | FB_CORE
R202 | 100k total_error<=0.15% | 2 | GND
C202 | 120pF C0G | 1 | VDD0P8_CORE
C202 | 120pF C0G | 2 | FB_CORE
R203 | 100k | 1 | CORE_PGOOD_5V
R203 | 100k | 2 | VIN_5V
R204 | 10k | 1 | CORE_ENABLE
R204 | 10k | 2 | VIN_5V
C203 | 10uF 10V X7R | 1 | VIN_5V
C203 | 10uF 10V X7R | 2 | GND
C204 | 10uF 10V X7R | 1 | VIN_5V
C204 | 10uF 10V X7R | 2 | GND
C205 | 100nF | 1 | VIN_5V
C205 | 100nF | 2 | GND
U22 | TPS628640BYCGR | A1 | GND
U22 | TPS628640BYCGR | A2 | VSET_CPU
U22 | TPS628640BYCGR | A3 | VDD0P8_CPU
U22 | TPS628640BYCGR | B1 | GND
U22 | TPS628640BYCGR | B2 | GND
U22 | TPS628640BYCGR | B3 | GND
U22 | TPS628640BYCGR | C1 | SW_CPU
U22 | TPS628640BYCGR | C2 | SW_CPU
U22 | TPS628640BYCGR | C3 | SW_CPU
U22 | TPS628640BYCGR | D1 | VIN_5V
U22 | TPS628640BYCGR | D2 | VIN_5V
U22 | TPS628640BYCGR | D3 | VIN_5V
U22 | TPS628640BYCGR | E1 | CORE_PGOOD_5V
U22 | TPS628640BYCGR | E2 | PWR_CPU_SDA
U22 | TPS628640BYCGR | E3 | PWR_CPU_SCL
L22 | 0.24uH DFE201612E-R24M REF | 1 | SW_CPU
L22 | 0.24uH DFE201612E-R24M REF | 2 | VDD0P8_CPU
C206 | 22uF X7R / total Ceff>=30uF | 1 | VDD0P8_CPU
C206 | 22uF X7R / total Ceff>=30uF | 2 | GND
C207 | 22uF X7R / total Ceff>=30uF | 1 | VDD0P8_CPU
C207 | 22uF X7R / total Ceff>=30uF | 2 | GND
C208 | 22uF X7R / total Ceff>=30uF | 1 | VDD0P8_CPU
C208 | 22uF X7R / total Ceff>=30uF | 2 | GND
R205 | 56.2k 1% / 0.8V / addr0x49 | 1 | VSET_CPU
R205 | 56.2k 1% / 0.8V / addr0x49 | 2 | GND
C209 | 100nF | 1 | VIN_5V
C209 | 100nF | 2 | GND
C210 | 10uF 10V X7R | 1 | VIN_5V
C210 | 10uF 10V X7R | 2 | GND
C211 | 10uF 10V X7R | 1 | VIN_5V
C211 | 10uF 10V X7R | 2 | GND
U23 | TPS628640BYCGR | A1 | GND
U23 | TPS628640BYCGR | A2 | VSET_KPU
U23 | TPS628640BYCGR | A3 | VDD0P8_KPU
U23 | TPS628640BYCGR | B1 | GND
U23 | TPS628640BYCGR | B2 | GND
U23 | TPS628640BYCGR | B3 | GND
U23 | TPS628640BYCGR | C1 | SW_KPU
U23 | TPS628640BYCGR | C2 | SW_KPU
U23 | TPS628640BYCGR | C3 | SW_KPU
U23 | TPS628640BYCGR | D1 | VIN_5V
U23 | TPS628640BYCGR | D2 | VIN_5V
U23 | TPS628640BYCGR | D3 | VIN_5V
U23 | TPS628640BYCGR | E1 | CORE_PGOOD_5V
U23 | TPS628640BYCGR | E2 | PWR_KPU_SDA
U23 | TPS628640BYCGR | E3 | PWR_KPU_SCL
L23 | 0.24uH DFE201612E-R24M REF | 1 | SW_KPU
L23 | 0.24uH DFE201612E-R24M REF | 2 | VDD0P8_KPU
C212 | 22uF X7R / total Ceff>=30uF | 1 | VDD0P8_KPU
C212 | 22uF X7R / total Ceff>=30uF | 2 | GND
C213 | 22uF X7R / total Ceff>=30uF | 1 | VDD0P8_KPU
C213 | 22uF X7R / total Ceff>=30uF | 2 | GND
C214 | 22uF X7R / total Ceff>=30uF | 1 | VDD0P8_KPU
C214 | 22uF X7R / total Ceff>=30uF | 2 | GND
R206 | 56.2k 1% / 0.8V / addr0x49 | 1 | VSET_KPU
R206 | 56.2k 1% / 0.8V / addr0x49 | 2 | GND
C215 | 100nF | 1 | VIN_5V
C215 | 100nF | 2 | GND
C216 | 10uF 10V X7R | 1 | VIN_5V
C216 | 10uF 10V X7R | 2 | GND
C217 | 10uF 10V X7R | 1 | VIN_5V
C217 | 10uF 10V X7R | 2 | GND
U24 | TPS62826ADMQ | 1 | CORE_PGOOD_5V
U24 | TPS62826ADMQ | 2 | FIXED_RAILS_PGOOD_3V3
U24 | TPS62826ADMQ | 3 | FB_DDR
U24 | TPS62826ADMQ | 4 | GND
U24 | TPS62826ADMQ | 5 | SW_DDR
U24 | TPS62826ADMQ | 6 | VIN_5V
L24 | 0.47uH DFE201610E-R47M=P2 CANDIDATE | 1 | SW_DDR
L24 | 0.47uH DFE201610E-R47M=P2 CANDIDATE | 2 | VDD1P1_DDR_IO
C218 | 47uF X7R / Ceff>=10uF | 1 | VDD1P1_DDR_IO
C218 | 47uF X7R / Ceff>=10uF | 2 | GND
R207 | 86.6k total_error<=0.15% | 1 | VDD1P1_DDR_IO
R207 | 86.6k total_error<=0.15% | 2 | FB_DDR
R208 | 100k total_error<=0.15% | 1 | FB_DDR
R208 | 100k total_error<=0.15% | 2 | GND
C219 | 120pF C0G | 1 | VDD1P1_DDR_IO
C219 | 120pF C0G | 2 | FB_DDR
C220 | 10uF 10V X7R | 1 | VIN_5V
C220 | 10uF 10V X7R | 2 | GND
C221 | 10uF 10V X7R | 1 | VIN_5V
C221 | 10uF 10V X7R | 2 | GND
C222 | 100nF | 1 | VIN_5V
C222 | 100nF | 2 | GND
U25 | TPS62825ADMQ | 1 | CORE_PGOOD_5V
U25 | TPS62825ADMQ | 2 | FIXED_RAILS_PGOOD_3V3
U25 | TPS62825ADMQ | 3 | FB_1V8
U25 | TPS62825ADMQ | 4 | GND
U25 | TPS62825ADMQ | 5 | SW_1V8
U25 | TPS62825ADMQ | 6 | VIN_5V
L25 | 0.47uH DFE201610E-R47M=P2 CANDIDATE | 1 | SW_1V8
L25 | 0.47uH DFE201610E-R47M=P2 CANDIDATE | 2 | VDD1P8
C223 | 47uF X7R / Ceff>=10uF | 1 | VDD1P8
C223 | 47uF X7R / Ceff>=10uF | 2 | GND
R210 | 200k total_error<=0.15% | 1 | VDD1P8
R210 | 200k total_error<=0.15% | 2 | FB_1V8
R211 | 100k total_error<=0.15% | 1 | FB_1V8
R211 | 100k total_error<=0.15% | 2 | GND
C224 | 120pF C0G | 1 | VDD1P8
C224 | 120pF C0G | 2 | FB_1V8
C225 | 10uF 10V X7R | 1 | VIN_5V
C225 | 10uF 10V X7R | 2 | GND
C226 | 10uF 10V X7R | 1 | VIN_5V
C226 | 10uF 10V X7R | 2 | GND
C227 | 100nF | 1 | VIN_5V
C227 | 100nF | 2 | GND
U26 | TPS62826ADMQ | 1 | CORE_PGOOD_5V
U26 | TPS62826ADMQ | 2 | FIXED_RAILS_PGOOD_3V3
U26 | TPS62826ADMQ | 3 | FB_3V3
U26 | TPS62826ADMQ | 4 | GND
U26 | TPS62826ADMQ | 5 | SW_3V3
U26 | TPS62826ADMQ | 6 | VIN_5V
L26 | 0.47uH DFE201610E-R47M=P2 CANDIDATE | 1 | SW_3V3
L26 | 0.47uH DFE201610E-R47M=P2 CANDIDATE | 2 | VDD_3V3
C228 | 47uF X7R / Ceff>=10uF | 1 | VDD_3V3
C228 | 47uF X7R / Ceff>=10uF | 2 | GND
R213 | 453k total_error<=0.15% | 1 | VDD_3V3
R213 | 453k total_error<=0.15% | 2 | FB_3V3
R214 | 100k total_error<=0.15% | 1 | FB_3V3
R214 | 100k total_error<=0.15% | 2 | GND
C229 | 120pF C0G | 1 | VDD_3V3
C229 | 120pF C0G | 2 | FB_3V3
C230 | 10uF 10V X7R | 1 | VIN_5V
C230 | 10uF 10V X7R | 2 | GND
C231 | 10uF 10V X7R | 1 | VIN_5V
C231 | 10uF 10V X7R | 2 | GND
C232 | 100nF | 1 | VIN_5V
C232 | 100nF | 2 | GND
R216 | 4.7k | 1 | PWR_CPU_SCL
R216 | 4.7k | 2 | VDD1P8
R217 | 4.7k | 1 | PWR_CPU_SDA
R217 | 4.7k | 2 | VDD1P8
R218 | 4.7k | 1 | PWR_KPU_SCL
R218 | 4.7k | 2 | VDD1P8
R219 | 4.7k | 1 | PWR_KPU_SDA
R219 | 4.7k | 2 | VDD1P8
R220 | 0R WSL060300000ZEA9 Rmax=0.25mOhm | 1 | VDD0P8_CORE
R220 | 0R WSL060300000ZEA9 Rmax=0.25mOhm | 2 | VDD0P8_DDR_CORE
C233 | 100nF REF / local PI UNQUALIFIED | 1 | VDD0P8_DDR_CORE
C233 | 100nF REF / local PI UNQUALIFIED | 2 | GND
FB202 | 120Ohm@100MHz Rdc<=0.1Ohm | 1 | VDD0P8_CORE
FB202 | 120Ohm@100MHz Rdc<=0.1Ohm | 2 | AVDD0P8_PLL
C234 | 100nF REF / local PI UNQUALIFIED | 1 | AVDD0P8_PLL
C234 | 100nF REF / local PI UNQUALIFIED | 2 | GND
FB203 | 120Ohm@100MHz Rdc<=0.1Ohm | 1 | VDD0P8_CORE
FB203 | 120Ohm@100MHz Rdc<=0.1Ohm | 2 | AVDD0P8_MIPI
C235 | 100nF REF / local PI UNQUALIFIED | 1 | AVDD0P8_MIPI
C235 | 100nF REF / local PI UNQUALIFIED | 2 | GND
FB204 | 120Ohm@100MHz Rdc<=0.1Ohm | 1 | VDD1P8
FB204 | 120Ohm@100MHz Rdc<=0.1Ohm | 2 | VAA_DDR
C236 | 100nF REF / local PI UNQUALIFIED | 1 | VAA_DDR
C236 | 100nF REF / local PI UNQUALIFIED | 2 | GND
FB205 | 120Ohm@100MHz Rdc<=0.1Ohm | 1 | VDD1P8
FB205 | 120Ohm@100MHz Rdc<=0.1Ohm | 2 | AVDD1P8_USB
C237 | 100nF REF / local PI UNQUALIFIED | 1 | AVDD1P8_USB
C237 | 100nF REF / local PI UNQUALIFIED | 2 | GND
FB206 | 120Ohm@100MHz Rdc<=0.1Ohm | 1 | VDD1P8
FB206 | 120Ohm@100MHz Rdc<=0.1Ohm | 2 | AVDD1P8_PMU
C238 | 100nF REF / local PI UNQUALIFIED | 1 | AVDD1P8_PMU
C238 | 100nF REF / local PI UNQUALIFIED | 2 | GND
C239 | 100nF local second PMU ball | 1 | AVDD1P8_PMU
C239 | 100nF local second PMU ball | 2 | GND
FB207 | 120Ohm@100MHz Rdc<=0.1Ohm | 1 | VDD1P8
FB207 | 120Ohm@100MHz Rdc<=0.1Ohm | 2 | AVDD1P8_MIPI
C240 | 100nF REF / local PI UNQUALIFIED | 1 | AVDD1P8_MIPI
C240 | 100nF REF / local PI UNQUALIFIED | 2 | GND
FB208 | 120Ohm@100MHz Rdc<=0.1Ohm | 1 | VDD1P8
FB208 | 120Ohm@100MHz Rdc<=0.1Ohm | 2 | AVDD1P8_ADC
C241 | 100nF REF / local PI UNQUALIFIED | 1 | AVDD1P8_ADC
C241 | 100nF REF / local PI UNQUALIFIED | 2 | GND
FB209 | 120Ohm@100MHz Rdc<=0.1Ohm | 1 | VDD1P8
FB209 | 120Ohm@100MHz Rdc<=0.1Ohm | 2 | AVDD1P8_CODEC
C242 | 100nF REF / local PI UNQUALIFIED | 1 | AVDD1P8_CODEC
C242 | 100nF REF / local PI UNQUALIFIED | 2 | GND
FB210 | 120Ohm@100MHz Rdc<=0.1Ohm | 1 | VDD_3V3
FB210 | 120Ohm@100MHz Rdc<=0.1Ohm | 2 | AVDD3P3_USB
C243 | 100nF REF / local PI UNQUALIFIED | 1 | AVDD3P3_USB
C243 | 100nF REF / local PI UNQUALIFIED | 2 | GND
R221 | 0R Rmax<=50mOhm | 1 | VDD_3V3
R221 | 0R Rmax<=50mOhm | 2 | VDD3P3_SD
C244 | 100nF REF / local PI UNQUALIFIED | 1 | VDD3P3_SD
C244 | 100nF REF / local PI UNQUALIFIED | 2 | GND
C245 | 100nF MIPI source second ball | 1 | AVDD1P8_MIPI
C245 | 100nF MIPI source second ball | 2 | GND
C246 | 100nF MIPI source second ball | 1 | AVDD0P8_MIPI
C246 | 100nF MIPI source second ball | 2 | GND
