oliverkirk-sudo/k230-c/project/engineering/reset/supervisor-pin-net-matrix.csv

reference | part | pin | net | dnp
U89 | TPS3808G01DRVR VIN GUARD | 1 | VDD1P8 | False
U89 | TPS3808G01DRVR VIN GUARD | 2 | VIN_GUARD_SENSE | False
U89 | TPS3808G01DRVR VIN GUARD | 4 | VDD1P8 | False
U89 | TPS3808G01DRVR VIN GUARD | 5 | GND | False
U89 | TPS3808G01DRVR VIN GUARD | 6 | FIXED_RAILS_PGOOD_3V3 | False
U89 | TPS3808G01DRVR VIN GUARD | 7 | GND | False
R525 | 88.7k total<=0.15% | 1 | VIN_5V | False
R525 | 88.7k total<=0.15% | 2 | VIN_GUARD_SENSE | False
R526 | 10k total<=0.15% | 1 | VIN_GUARD_SENSE | False
R526 | 10k total<=0.15% | 2 | GND | False
R527 | 10k RAW PG PULLUP | 1 | VDD_3V3 | False
R527 | 10k RAW PG PULLUP | 2 | FIXED_RAILS_PGOOD_3V3 | False
C809 | 100nF | 1 | VDD1P8 | False
C809 | 100nF | 2 | GND | False
U94 | SN74AUP1G97DRLR SCHMITT AND | 1 | GND | False
U94 | SN74AUP1G97DRLR SCHMITT AND | 2 | GND | False
U94 | SN74AUP1G97DRLR SCHMITT AND | 3 | FIXED_RAILS_PGOOD_3V3 | False
U94 | SN74AUP1G97DRLR SCHMITT AND | 4 | RESET_RELEASE_REQUEST_1V8 | False
U94 | SN74AUP1G97DRLR SCHMITT AND | 5 | VDD1P8 | False
U94 | SN74AUP1G97DRLR SCHMITT AND | 6 | RSTN | False
U90 | TPS3808G01DRVR RESET DELAY | 1 | VDD1P8 | False
U90 | TPS3808G01DRVR RESET DELAY | 2 | VDD1P8 | False
U90 | TPS3808G01DRVR RESET DELAY | 4 | RESET_RELEASE_REQUEST_1V8 | False
U90 | TPS3808G01DRVR RESET DELAY | 5 | GND | False
U90 | TPS3808G01DRVR RESET DELAY | 6 | RESET_DELAYED_1V8 | False
U90 | TPS3808G01DRVR RESET DELAY | 7 | GND | False
U91 | SN74AUP1G17DRLR RESET BUFFER | 2 | RESET_DELAYED_1V8 | False
U91 | SN74AUP1G17DRLR RESET BUFFER | 3 | GND | False
U91 | SN74AUP1G17DRLR RESET BUFFER | 4 | SOC_RSTN | False
U91 | SN74AUP1G17DRLR RESET BUFFER | 5 | VDD1P8 | False
R530 | 100k 1% DELAY NODE PULLUP | 1 | VDD1P8 | False
R530 | 100k 1% DELAY NODE PULLUP | 2 | RESET_DELAYED_1V8 | False
U92 | SN74AUP1G97DRLR SCHMITT AND | 1 | GND | False
U92 | SN74AUP1G97DRLR SCHMITT AND | 2 | GND | False
U92 | SN74AUP1G97DRLR SCHMITT AND | 3 | FIXED_RAILS_PGOOD_3V3 | False
U92 | SN74AUP1G97DRLR SCHMITT AND | 4 | STORAGE_ENABLE_1V8 | False
U92 | SN74AUP1G97DRLR SCHMITT AND | 5 | VDD1P8 | False
U92 | SN74AUP1G97DRLR SCHMITT AND | 6 | BOOT_VOLTAGE_QUALIFIED_1V8 | False
U93 | SN74AUP1G06DRLR DISABLE | 2 | STORAGE_ENABLE_1V8 | False
U93 | SN74AUP1G06DRLR DISABLE | 3 | GND | False
U93 | SN74AUP1G06DRLR DISABLE | 4 | GLOBAL_DISABLE | False
U93 | SN74AUP1G06DRLR DISABLE | 5 | VDD1P8 | False
R528 | 0R QUALIFICATION STRAP DNP | 1 | VDD1P8 | True
R528 | 0R QUALIFICATION STRAP DNP | 2 | BOOT_VOLTAGE_QUALIFIED_1V8 | True
R529 | 100k DEFAULT INHIBIT | 1 | BOOT_VOLTAGE_QUALIFIED_1V8 | False
R529 | 100k DEFAULT INHIBIT | 2 | GND | False
C810 | 100nF U94 | 1 | VDD1P8 | False
C810 | 100nF U94 | 2 | GND | False
C811 | 100nF U90 | 1 | VDD1P8 | False
C811 | 100nF U90 | 2 | GND | False
C812 | 100nF U91 | 1 | VDD1P8 | False
C812 | 100nF U91 | 2 | GND | False
C813 | 100nF U92 | 1 | VDD1P8 | False
C813 | 100nF U92 | 2 | GND | False
C814 | 100nF U93 | 1 | VDD1P8 | False
C814 | 100nF U93 | 2 | GND | False
