oliverkirk-sudo/k230-c/project/engineering/mechanical/small-parts-pad-coordinate-audit.csv

footprint | mpn | pad | function | x_mm | y_mm | copper_w_mm | copper_h_mm | exposed_w_mm | exposed_h_mm | mask_margin_mm | source_url | source_pages
TI_RSV0016A_TMUX1574_1.8x2.6_P0.4_DrawingVerified | TMUX1574RSVR | 1 | S1B | -0.75 | -0.6 | 0.7 | 0.2 | 0.7 | 0.2 | 0.05 | https://www.ti.com/lit/ds/symlink/tmux1574.pdf | 3,36-38
TI_RSV0016A_TMUX1574_1.8x2.6_P0.4_DrawingVerified | TMUX1574RSVR | 2 | D1 | -0.8 | -0.2 | 0.6 | 0.2 | 0.6 | 0.2 | 0.05 | https://www.ti.com/lit/ds/symlink/tmux1574.pdf | 3,36-38
TI_RSV0016A_TMUX1574_1.8x2.6_P0.4_DrawingVerified | TMUX1574RSVR | 3 | S2A | -0.8 | 0.2 | 0.6 | 0.2 | 0.6 | 0.2 | 0.05 | https://www.ti.com/lit/ds/symlink/tmux1574.pdf | 3,36-38
TI_RSV0016A_TMUX1574_1.8x2.6_P0.4_DrawingVerified | TMUX1574RSVR | 4 | S2B | -0.8 | 0.6 | 0.6 | 0.2 | 0.6 | 0.2 | 0.05 | https://www.ti.com/lit/ds/symlink/tmux1574.pdf | 3,36-38
TI_RSV0016A_TMUX1574_1.8x2.6_P0.4_DrawingVerified | TMUX1574RSVR | 5 | D2 | -0.6 | 1.2 | 0.2 | 0.6 | 0.2 | 0.6 | 0.05 | https://www.ti.com/lit/ds/symlink/tmux1574.pdf | 3,36-38
TI_RSV0016A_TMUX1574_1.8x2.6_P0.4_DrawingVerified | TMUX1574RSVR | 6 | GND | -0.2 | 1.2 | 0.2 | 0.6 | 0.2 | 0.6 | 0.05 | https://www.ti.com/lit/ds/symlink/tmux1574.pdf | 3,36-38
TI_RSV0016A_TMUX1574_1.8x2.6_P0.4_DrawingVerified | TMUX1574RSVR | 7 | D3 | 0.2 | 1.2 | 0.2 | 0.6 | 0.2 | 0.6 | 0.05 | https://www.ti.com/lit/ds/symlink/tmux1574.pdf | 3,36-38
TI_RSV0016A_TMUX1574_1.8x2.6_P0.4_DrawingVerified | TMUX1574RSVR | 8 | S3B | 0.6 | 1.2 | 0.2 | 0.6 | 0.2 | 0.6 | 0.05 | https://www.ti.com/lit/ds/symlink/tmux1574.pdf | 3,36-38
TI_RSV0016A_TMUX1574_1.8x2.6_P0.4_DrawingVerified | TMUX1574RSVR | 9 | S3A | 0.8 | 0.6 | 0.6 | 0.2 | 0.6 | 0.2 | 0.05 | https://www.ti.com/lit/ds/symlink/tmux1574.pdf | 3,36-38
TI_RSV0016A_TMUX1574_1.8x2.6_P0.4_DrawingVerified | TMUX1574RSVR | 10 | D4 | 0.8 | 0.2 | 0.6 | 0.2 | 0.6 | 0.2 | 0.05 | https://www.ti.com/lit/ds/symlink/tmux1574.pdf | 3,36-38
TI_RSV0016A_TMUX1574_1.8x2.6_P0.4_DrawingVerified | TMUX1574RSVR | 11 | S4B | 0.8 | -0.2 | 0.6 | 0.2 | 0.6 | 0.2 | 0.05 | https://www.ti.com/lit/ds/symlink/tmux1574.pdf | 3,36-38
TI_RSV0016A_TMUX1574_1.8x2.6_P0.4_DrawingVerified | TMUX1574RSVR | 12 | S4A | 0.8 | -0.6 | 0.6 | 0.2 | 0.6 | 0.2 | 0.05 | https://www.ti.com/lit/ds/symlink/tmux1574.pdf | 3,36-38
TI_RSV0016A_TMUX1574_1.8x2.6_P0.4_DrawingVerified | TMUX1574RSVR | 13 | EN_N | 0.6 | -1.2 | 0.2 | 0.6 | 0.2 | 0.6 | 0.05 | https://www.ti.com/lit/ds/symlink/tmux1574.pdf | 3,36-38
TI_RSV0016A_TMUX1574_1.8x2.6_P0.4_DrawingVerified | TMUX1574RSVR | 14 | VDD | 0.2 | -1.2 | 0.2 | 0.6 | 0.2 | 0.6 | 0.05 | https://www.ti.com/lit/ds/symlink/tmux1574.pdf | 3,36-38
TI_RSV0016A_TMUX1574_1.8x2.6_P0.4_DrawingVerified | TMUX1574RSVR | 15 | SEL | -0.2 | -1.2 | 0.2 | 0.6 | 0.2 | 0.6 | 0.05 | https://www.ti.com/lit/ds/symlink/tmux1574.pdf | 3,36-38
TI_RSV0016A_TMUX1574_1.8x2.6_P0.4_DrawingVerified | TMUX1574RSVR | 16 | S1A | -0.6 | -1.2 | 0.2 | 0.6 | 0.2 | 0.6 | 0.05 | https://www.ti.com/lit/ds/symlink/tmux1574.pdf | 3,36-38
TI_DBV0005A_SN74LVC1G32_SOT23_5_DrawingVerified | SN74LVC1G32DBVR | 1 | A | -1.3 | -0.95 | 1.1 | 0.6 | 1.1 | 0.6 | 0.05 | https://www.ti.com/lit/ds/symlink/sn74lvc1g32.pdf | 41-43
TI_DBV0005A_SN74LVC1G32_SOT23_5_DrawingVerified | SN74LVC1G32DBVR | 2 | B | -1.3 | 0 | 1.1 | 0.6 | 1.1 | 0.6 | 0.05 | https://www.ti.com/lit/ds/symlink/sn74lvc1g32.pdf | 41-43
TI_DBV0005A_SN74LVC1G32_SOT23_5_DrawingVerified | SN74LVC1G32DBVR | 3 | GND | -1.3 | 0.95 | 1.1 | 0.6 | 1.1 | 0.6 | 0.05 | https://www.ti.com/lit/ds/symlink/sn74lvc1g32.pdf | 41-43
TI_DBV0005A_SN74LVC1G32_SOT23_5_DrawingVerified | SN74LVC1G32DBVR | 4 | Y | 1.3 | 0.95 | 1.1 | 0.6 | 1.1 | 0.6 | 0.05 | https://www.ti.com/lit/ds/symlink/sn74lvc1g32.pdf | 41-43
TI_DBV0005A_SN74LVC1G32_SOT23_5_DrawingVerified | SN74LVC1G32DBVR | 5 | VCC | 1.3 | -0.95 | 1.1 | 0.6 | 1.1 | 0.6 | 0.05 | https://www.ti.com/lit/ds/symlink/sn74lvc1g32.pdf | 41-43
TI_DMQ0006A_TPS6282xA_1.5x1.5_SMD_DrawingVerified | TPS6282xADMQ | 1 | EN | -0.65 | -0.5 | 0.7 | 0.35 | 0.6 | 0.25 | -0.05 | https://www.ti.com/lit/ds/symlink/tps62827.pdf | 3,32-34
TI_DMQ0006A_TPS6282xA_1.5x1.5_SMD_DrawingVerified | TPS6282xADMQ | 2 | PG | -0.65 | 0 | 0.7 | 0.35 | 0.6 | 0.25 | -0.05 | https://www.ti.com/lit/ds/symlink/tps62827.pdf | 3,32-34
TI_DMQ0006A_TPS6282xA_1.5x1.5_SMD_DrawingVerified | TPS6282xADMQ | 3 | FB | -0.65 | 0.5 | 0.7 | 0.35 | 0.6 | 0.25 | -0.05 | https://www.ti.com/lit/ds/symlink/tps62827.pdf | 3,32-34
TI_DMQ0006A_TPS6282xA_1.5x1.5_SMD_DrawingVerified | TPS6282xADMQ | 4 | GND | 0.45 | 0.5 | 1.1 | 0.3 | 1 | 0.2 | -0.05 | https://www.ti.com/lit/ds/symlink/tps62827.pdf | 3,32-34
TI_DMQ0006A_TPS6282xA_1.5x1.5_SMD_DrawingVerified | TPS6282xADMQ | 5 | SW | 0.45 | 0 | 1.1 | 0.3 | 1 | 0.2 | -0.05 | https://www.ti.com/lit/ds/symlink/tps62827.pdf | 3,32-34
TI_DMQ0006A_TPS6282xA_1.5x1.5_SMD_DrawingVerified | TPS6282xADMQ | 6 | VIN | 0.45 | -0.5 | 1.1 | 0.3 | 1 | 0.2 | -0.05 | https://www.ti.com/lit/ds/symlink/tps62827.pdf | 3,32-34
TI_YCG0015_TPS628640_1.05x1.78_P0.35_SMD_DrawingVerified | TPS628640BYCGR | A1 | AGND | -0.35 | -0.7 | 0.265 | 0.265 | 0.2 | 0.2 | -0.0325 | https://www.ti.com/lit/ds/symlink/tps62864.pdf | 4,30-32
TI_YCG0015_TPS628640_1.05x1.78_P0.35_SMD_DrawingVerified | TPS628640BYCGR | A2 | VSET_PG | 0 | -0.7 | 0.265 | 0.265 | 0.2 | 0.2 | -0.0325 | https://www.ti.com/lit/ds/symlink/tps62864.pdf | 4,30-32
TI_YCG0015_TPS628640_1.05x1.78_P0.35_SMD_DrawingVerified | TPS628640BYCGR | A3 | VOS | 0.35 | -0.7 | 0.265 | 0.265 | 0.2 | 0.2 | -0.0325 | https://www.ti.com/lit/ds/symlink/tps62864.pdf | 4,30-32
TI_YCG0015_TPS628640_1.05x1.78_P0.35_SMD_DrawingVerified | TPS628640BYCGR | B1 | PGND | -0.35 | -0.35 | 0.265 | 0.265 | 0.2 | 0.2 | -0.0325 | https://www.ti.com/lit/ds/symlink/tps62864.pdf | 4,30-32
TI_YCG0015_TPS628640_1.05x1.78_P0.35_SMD_DrawingVerified | TPS628640BYCGR | B2 | PGND | 0 | -0.35 | 0.265 | 0.265 | 0.2 | 0.2 | -0.0325 | https://www.ti.com/lit/ds/symlink/tps62864.pdf | 4,30-32
TI_YCG0015_TPS628640_1.05x1.78_P0.35_SMD_DrawingVerified | TPS628640BYCGR | B3 | PGND | 0.35 | -0.35 | 0.265 | 0.265 | 0.2 | 0.2 | -0.0325 | https://www.ti.com/lit/ds/symlink/tps62864.pdf | 4,30-32
TI_YCG0015_TPS628640_1.05x1.78_P0.35_SMD_DrawingVerified | TPS628640BYCGR | C1 | SW | -0.35 | 0 | 0.265 | 0.265 | 0.2 | 0.2 | -0.0325 | https://www.ti.com/lit/ds/symlink/tps62864.pdf | 4,30-32
TI_YCG0015_TPS628640_1.05x1.78_P0.35_SMD_DrawingVerified | TPS628640BYCGR | C2 | SW | 0 | 0 | 0.265 | 0.265 | 0.2 | 0.2 | -0.0325 | https://www.ti.com/lit/ds/symlink/tps62864.pdf | 4,30-32
TI_YCG0015_TPS628640_1.05x1.78_P0.35_SMD_DrawingVerified | TPS628640BYCGR | C3 | SW | 0.35 | 0 | 0.265 | 0.265 | 0.2 | 0.2 | -0.0325 | https://www.ti.com/lit/ds/symlink/tps62864.pdf | 4,30-32
TI_YCG0015_TPS628640_1.05x1.78_P0.35_SMD_DrawingVerified | TPS628640BYCGR | D1 | VIN | -0.35 | 0.35 | 0.265 | 0.265 | 0.2 | 0.2 | -0.0325 | https://www.ti.com/lit/ds/symlink/tps62864.pdf | 4,30-32
TI_YCG0015_TPS628640_1.05x1.78_P0.35_SMD_DrawingVerified | TPS628640BYCGR | D2 | VIN | 0 | 0.35 | 0.265 | 0.265 | 0.2 | 0.2 | -0.0325 | https://www.ti.com/lit/ds/symlink/tps62864.pdf | 4,30-32
TI_YCG0015_TPS628640_1.05x1.78_P0.35_SMD_DrawingVerified | TPS628640BYCGR | D3 | VIN | 0.35 | 0.35 | 0.265 | 0.265 | 0.2 | 0.2 | -0.0325 | https://www.ti.com/lit/ds/symlink/tps62864.pdf | 4,30-32
TI_YCG0015_TPS628640_1.05x1.78_P0.35_SMD_DrawingVerified | TPS628640BYCGR | E1 | EN | -0.35 | 0.7 | 0.265 | 0.265 | 0.2 | 0.2 | -0.0325 | https://www.ti.com/lit/ds/symlink/tps62864.pdf | 4,30-32
TI_YCG0015_TPS628640_1.05x1.78_P0.35_SMD_DrawingVerified | TPS628640BYCGR | E2 | SDA | 0 | 0.7 | 0.265 | 0.265 | 0.2 | 0.2 | -0.0325 | https://www.ti.com/lit/ds/symlink/tps62864.pdf | 4,30-32
TI_YCG0015_TPS628640_1.05x1.78_P0.35_SMD_DrawingVerified | TPS628640BYCGR | E3 | SCL | 0.35 | 0.7 | 0.265 | 0.265 | 0.2 | 0.2 | -0.0325 | https://www.ti.com/lit/ds/symlink/tps62864.pdf | 4,30-32
