oliverkirk-sudo/k230-c/project/cad/instrumented-reference/open-pin-review.csv

reference | unit | pin | function | net | status | sheet
U1 | 5 | C20 | DDR_NC |  | OFFICIAL_PINOUT_LP4_MODE_UNUSED | 02_SoC_2
U1 | 5 | D19 | DDR_NC |  | OFFICIAL_PINOUT_LP4_MODE_UNUSED | 02_SoC_2
U1 | 5 | D20 | DDR_NC |  | OFFICIAL_PINOUT_LP4_MODE_UNUSED | 02_SoC_2
U1 | 5 | F18 | DDR_NC |  | OFFICIAL_PINOUT_LP4_MODE_UNUSED | 02_SoC_2
U1 | 5 | G17 | DDR_NC |  | OFFICIAL_PINOUT_LP4_MODE_UNUSED | 02_SoC_2
U1 | 5 | H18 | DDR_NC |  | OFFICIAL_PINOUT_LP4_MODE_UNUSED | 02_SoC_2
U1 | 5 | H19 | DDR_NC |  | OFFICIAL_PINOUT_LP4_MODE_UNUSED | 02_SoC_2
U1 | 5 | J17 | DDR_CKEB1 |  | REFERENCE_SINGLE_RANK_UNUSED_OUTPUT | 02_SoC_2
U1 | 6 | J19 | DDR_CSB1 |  | REFERENCE_SINGLE_RANK_UNUSED_OUTPUT | 02_SoC_2
U1 | 6 | K20 | DDR_NC |  | OFFICIAL_PINOUT_LP4_MODE_UNUSED | 02_SoC_2
U1 | 6 | L17 | DDR_NC |  | OFFICIAL_PINOUT_LP4_MODE_UNUSED | 02_SoC_2
U1 | 6 | L18 | DDR_NC |  | OFFICIAL_PINOUT_LP4_MODE_UNUSED | 02_SoC_2
U1 | 6 | L20 | DDR_NC |  | OFFICIAL_PINOUT_LP4_MODE_UNUSED | 02_SoC_2
U1 | 6 | M17 | DDR_NC |  | OFFICIAL_PINOUT_LP4_MODE_UNUSED | 02_SoC_2
U1 | 6 | M20 | DDR_NA |  | OFFICIAL_PINOUT_LP4_MODE_UNUSED | 02_SoC_2
U1 | 6 | N18 | DDR_NC |  | OFFICIAL_PINOUT_LP4_MODE_UNUSED | 02_SoC_2
U1 | 6 | P18 | DDR_CKEA1 |  | REFERENCE_SINGLE_RANK_UNUSED_OUTPUT | 02_SoC_2
U1 | 6 | T19 | DDR_CSA1 |  | REFERENCE_SINGLE_RANK_UNUSED_OUTPUT | 02_SoC_2
U1 | 8 | U6 | MIPI_ATB |  | GUIDE_EXPLICIT_MIPI_ATB_FLOAT | 02_SoC_2
U1 | 9 | A20 | NC |  | MANUFACTURER_NC_DNU_MUST_REMAIN_OPEN | 03_SoC_3
U1 | 9 | B11 | GPIO70/OUT0 |  | OPEN_TBD_NO_NC_FLAG | 03_SoC_3
U1 | 9 | C10 | GPIO64/INT0 |  | OPEN_TBD_NO_NC_FLAG | 03_SoC_3
U1 | 9 | C11 | GPIO71/OUT1 |  | OPEN_TBD_NO_NC_FLAG | 03_SoC_3
U1 | 9 | C12 | GPIO68/INT4 |  | OPEN_TBD_NO_NC_FLAG | 03_SoC_3
U1 | 10 | D8 | ANA_TS_VTEST |  | OPEN_TBD_NO_NC_FLAG | 03_SoC_3
U1 | 10 | Y1 | NC |  | MANUFACTURER_NC_DNU_MUST_REMAIN_OPEN | 03_SoC_3
U1 | 10 | Y20 | NC |  | MANUFACTURER_NC_DNU_MUST_REMAIN_OPEN | 03_SoC_3
U2 | 1 | A1 | DNU |  | MANUFACTURER_NC_DNU_MUST_REMAIN_OPEN | 04_LPDDR4_1
U2 | 1 | A2 | DNU |  | MANUFACTURER_NC_DNU_MUST_REMAIN_OPEN | 04_LPDDR4_1
U2 | 1 | A8 | NC |  | MANUFACTURER_NC_DNU_MUST_REMAIN_OPEN | 04_LPDDR4_1
U2 | 1 | A11 | DNU |  | MANUFACTURER_NC_DNU_MUST_REMAIN_OPEN | 04_LPDDR4_1
U2 | 1 | A12 | DNU |  | MANUFACTURER_NC_DNU_MUST_REMAIN_OPEN | 04_LPDDR4_1
U2 | 1 | B1 | DNU |  | MANUFACTURER_NC_DNU_MUST_REMAIN_OPEN | 04_LPDDR4_1
U2 | 1 | B12 | DNU |  | MANUFACTURER_NC_DNU_MUST_REMAIN_OPEN | 04_LPDDR4_1
U2 | 2 | G11 | DNU |  | MANUFACTURER_NC_DNU_MUST_REMAIN_OPEN | 04_LPDDR4_1
U2 | 2 | H3 | NC |  | MANUFACTURER_NC_DNU_MUST_REMAIN_OPEN | 04_LPDDR4_1
U2 | 3 | J5 | NC |  | MANUFACTURER_NC_DNU_MUST_REMAIN_OPEN | 04_LPDDR4_1
U2 | 3 | K5 | DNU |  | MANUFACTURER_NC_DNU_MUST_REMAIN_OPEN | 04_LPDDR4_1
U2 | 3 | K8 | DNU |  | MANUFACTURER_NC_DNU_MUST_REMAIN_OPEN | 04_LPDDR4_1
U2 | 3 | N5 | DNU |  | MANUFACTURER_NC_DNU_MUST_REMAIN_OPEN | 04_LPDDR4_1
U2 | 3 | N8 | DNU |  | MANUFACTURER_NC_DNU_MUST_REMAIN_OPEN | 04_LPDDR4_1
U2 | 3 | P5 | NC |  | MANUFACTURER_NC_DNU_MUST_REMAIN_OPEN | 04_LPDDR4_1
U2 | 4 | R3 | NC |  | MANUFACTURER_NC_DNU_MUST_REMAIN_OPEN | 04_LPDDR4_1
U2 | 5 | AA1 | DNU |  | MANUFACTURER_NC_DNU_MUST_REMAIN_OPEN | 05_LPDDR4_2
U2 | 5 | AA12 | DNU |  | MANUFACTURER_NC_DNU_MUST_REMAIN_OPEN | 05_LPDDR4_2
U2 | 5 | AB1 | DNU |  | MANUFACTURER_NC_DNU_MUST_REMAIN_OPEN | 05_LPDDR4_2
U2 | 5 | AB2 | DNU |  | MANUFACTURER_NC_DNU_MUST_REMAIN_OPEN | 05_LPDDR4_2
U2 | 5 | AB11 | DNU |  | MANUFACTURER_NC_DNU_MUST_REMAIN_OPEN | 05_LPDDR4_2
U2 | 5 | AB12 | DNU |  | MANUFACTURER_NC_DNU_MUST_REMAIN_OPEN | 05_LPDDR4_2
U3 | 1 | A1 | NC |  | MANUFACTURER_NC_DNU_MUST_REMAIN_OPEN | 06_eMMC_1
U3 | 1 | A2 | NC |  | MANUFACTURER_NC_DNU_MUST_REMAIN_OPEN | 06_eMMC_1
U3 | 1 | A7 | RFU |  | MANUFACTURER_RFU_NO_USE_MUST_REMAIN_OPEN | 06_eMMC_1
U3 | 1 | A8 | NC |  | MANUFACTURER_NC_DNU_MUST_REMAIN_OPEN | 06_eMMC_1
U3 | 1 | A9 | NC |  | MANUFACTURER_NC_DNU_MUST_REMAIN_OPEN | 06_eMMC_1
U3 | 1 | A10 | NC |  | MANUFACTURER_NC_DNU_MUST_REMAIN_OPEN | 06_eMMC_1
U3 | 1 | A11 | NC |  | MANUFACTURER_NC_DNU_MUST_REMAIN_OPEN | 06_eMMC_1
U3 | 1 | A12 | NC |  | MANUFACTURER_NC_DNU_MUST_REMAIN_OPEN | 06_eMMC_1
U3 | 1 | A13 | NC |  | MANUFACTURER_NC_DNU_MUST_REMAIN_OPEN | 06_eMMC_1
U3 | 1 | A14 | NC |  | MANUFACTURER_NC_DNU_MUST_REMAIN_OPEN | 06_eMMC_1
U3 | 1 | B1 | NC |  | MANUFACTURER_NC_DNU_MUST_REMAIN_OPEN | 06_eMMC_1
U3 | 1 | B7 | NC |  | MANUFACTURER_NC_DNU_MUST_REMAIN_OPEN | 06_eMMC_1
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
U3 | 4 | P1 | NC |  | MANUFACTURER_NC_DNU_MUST_REMAIN_OPEN | 06_eMMC_1
U3 | 4 | P2 | NC |  | MANUFACTURER_NC_DNU_MUST_REMAIN_OPEN | 06_eMMC_1
U3 | 4 | P7 | RFU |  | MANUFACTURER_RFU_NO_USE_MUST_REMAIN_OPEN | 06_eMMC_1
U3 | 4 | P8 | NC |  | MANUFACTURER_NC_DNU_MUST_REMAIN_OPEN | 06_eMMC_1
U3 | 4 | P9 | NC |  | MANUFACTURER_NC_DNU_MUST_REMAIN_OPEN | 06_eMMC_1
U3 | 4 | P10 | RFU |  | MANUFACTURER_RFU_NO_USE_MUST_REMAIN_OPEN | 06_eMMC_1
U3 | 4 | P11 | NC |  | MANUFACTURER_NC_DNU_MUST_REMAIN_OPEN | 06_eMMC_1
U3 | 4 | P12 | NC |  | MANUFACTURER_NC_DNU_MUST_REMAIN_OPEN | 06_eMMC_1
U3 | 4 | P13 | NC |  | MANUFACTURER_NC_DNU_MUST_REMAIN_OPEN | 06_eMMC_1
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
