oliverkirk-sudo/k230-c/project/engineering/k230-ddr-constrained/joint-link-audit/results/link-pair-preserved-flex/spacing.csv

net_a | net_b | group_a | group_b | layer | scope | closest_segment_a | closest_segment_b | minimum_centerline_mm | minimum_copper_edge_mm | pair_internal | figure054_factor | nominal_H_mm | figure054_edge_gap_target_mm | below_figure054_edge_gap | text3W_edge_interpretation_below | text3W_center_interpretation_below | within_pair_gap_qualified
DDR_CAA0 | DDR_CAB0 | A_ADDRESS_COMMAND | B_ADDRESS_COMMAND | L8 | actual_interconnect_only | track:DDR_CAA0:L8:656:0 | track:DDR_CAB0:L8:671:21 | 2.6287176056 | 2.5271176056 | False | 3 | 0.1195 | 0.3585 | False | False | False
DDR_CAA0 | DDR_CAB0 | A_ADDRESS_COMMAND | B_ADDRESS_COMMAND | L8 | all_inner_layer_traces | track:DDR_CAA0:L8:656:0 | track:DDR_CAB0:L8:671:21 | 2.6287176056 | 2.5271176056 | False | 3 | 0.1195 | 0.3585 | False | False | False
DDR_CAA0 | DDR_CAB1 | A_ADDRESS_COMMAND | B_ADDRESS_COMMAND | L8 | actual_interconnect_only | track:DDR_CAA0:L8:656:0 | track:DDR_CAB1:L8:666:15 | 0.325 | 0.2234 | False | 3 | 0.1195 | 0.3585 | True | True | False
DDR_CAA0 | DDR_CAB1 | A_ADDRESS_COMMAND | B_ADDRESS_COMMAND | L8 | all_inner_layer_traces | track:DDR_CAA0:L8:656:0 | track:DDR_CAB1:L8:666:15 | 0.325 | 0.2234 | False | 3 | 0.1195 | 0.3585 | True | True | False
DDR_CAA0 | DDR_CAB3 | A_ADDRESS_COMMAND | B_ADDRESS_COMMAND | L8 | actual_interconnect_only | track:DDR_CAA0:L8:656:0 | track:DDR_CAB3:L8:695:21 | 1.625 | 1.5234 | False | 3 | 0.1195 | 0.3585 | False | False | False
DDR_CAA0 | DDR_CAB3 | A_ADDRESS_COMMAND | B_ADDRESS_COMMAND | L8 | all_inner_layer_traces | track:DDR_CAA0:L8:656:0 | track:DDR_CAB3:L8:695:21 | 1.625 | 1.5234 | False | 3 | 0.1195 | 0.3585 | False | False | False
DDR_CAA0 | DDR_CAB4 | A_ADDRESS_COMMAND | B_ADDRESS_COMMAND | L8 | actual_interconnect_only | track:DDR_CAA0:L8:656:0 | track:DDR_CAB4:L8:682:19 | 2.6 | 2.4984 | False | 3 | 0.1195 | 0.3585 | False | False | False
DDR_CAA0 | DDR_CAB4 | A_ADDRESS_COMMAND | B_ADDRESS_COMMAND | L8 | all_inner_layer_traces | track:DDR_CAA0:L8:656:0 | track:DDR_CAB4:L8:682:19 | 2.6 | 2.4984 | False | 3 | 0.1195 | 0.3585 | False | False | False
DDR_CAA0 | DDR_CAB5 | A_ADDRESS_COMMAND | B_ADDRESS_COMMAND | L8 | actual_interconnect_only | track:DDR_CAA0:L8:656:0 | track:DDR_CAB5:L8:707:23 | 1.95 | 1.8484 | False | 3 | 0.1195 | 0.3585 | False | False | False
DDR_CAA0 | DDR_CAB5 | A_ADDRESS_COMMAND | B_ADDRESS_COMMAND | L8 | all_inner_layer_traces | track:DDR_CAA0:L8:656:0 | track:DDR_CAB5:L8:707:23 | 1.95 | 1.8484 | False | 3 | 0.1195 | 0.3585 | False | False | False
DDR_CAA0 | DDR_CKEA0 | A_ADDRESS_COMMAND | A_ADDRESS_COMMAND | L8 | actual_interconnect_only | track:DDR_CAA0:L8:656:1 | track:DDR_CKEA0:L8:670:79 | 0.2298097039 | 0.1282097039 | False | 3 | 0.1195 | 0.3585 | True | True | True
DDR_CAA0 | DDR_CKEA0 | A_ADDRESS_COMMAND | A_ADDRESS_COMMAND | L8 | all_inner_layer_traces | track:DDR_CAA0:L8:656:1 | track:DDR_CKEA0:L8:670:79 | 0.2298097039 | 0.1282097039 | False | 3 | 0.1195 | 0.3585 | True | True | True
DDR_CAA0 | DDR_CKEB0 | A_ADDRESS_COMMAND | B_ADDRESS_COMMAND | L8 | actual_interconnect_only | track:DDR_CAA0:L8:656:0 | track:DDR_CKEB0:L8:672:14 | 0.73125 | 0.62965 | False | 3 | 0.1195 | 0.3585 | False | False | False
DDR_CAA0 | DDR_CKEB0 | A_ADDRESS_COMMAND | B_ADDRESS_COMMAND | L8 | all_inner_layer_traces | track:DDR_CAA0:L8:656:0 | track:DDR_CKEB0:L8:672:14 | 0.73125 | 0.62965 | False | 3 | 0.1195 | 0.3585 | False | False | False
DDR_CAA0 | DDR_CSB0 | A_ADDRESS_COMMAND | B_ADDRESS_COMMAND | L8 | actual_interconnect_only | track:DDR_CAA0:L8:656:0 | track:DDR_CSB0:L8:677:13 | 0.975 | 0.8734 | False | 3 | 0.1195 | 0.3585 | False | False | False
DDR_CAA0 | DDR_CSB0 | A_ADDRESS_COMMAND | B_ADDRESS_COMMAND | L8 | all_inner_layer_traces | track:DDR_CAA0:L8:656:0 | track:DDR_CSB0:L8:677:13 | 0.975 | 0.8734 | False | 3 | 0.1195 | 0.3585 | False | False | False
DDR_CAA0 | DDR_DMIA1 | A_ADDRESS_COMMAND | A_BYTE1 | L8 | actual_interconnect_only | track:DDR_CAA0:L8:656:0 | track:DDR_DMIA1:L8:675:0 | 1.8384776311 | 1.7368776311 | False | 3 | 0.1195 | 0.3585 | False | False | False
DDR_CAA0 | DDR_DMIA1 | A_ADDRESS_COMMAND | A_BYTE1 | L8 | all_inner_layer_traces | track:DDR_CAA0:L8:656:0 | track:DDR_DMIA1:L8:675:0 | 1.8384776311 | 1.7368776311 | False | 3 | 0.1195 | 0.3585 | False | False | False
DDR_CAA0 | DDR_DMIB0 | A_ADDRESS_COMMAND | B_BYTE0 | L8 | actual_interconnect_only | track:DDR_CAA0:L8:656:0 | track:DDR_DMIB0:L8:654:8 | 4.875 | 4.7734 | False | 3 | 0.1195 | 0.3585 | False | False | False
DDR_CAA0 | DDR_DMIB0 | A_ADDRESS_COMMAND | B_BYTE0 | L8 | all_inner_layer_traces | track:DDR_CAA0:L8:656:0 | track:DDR_DMIB0:L8:654:8 | 4.875 | 4.7734 | False | 3 | 0.1195 | 0.3585 | False | False | False
DDR_CAA0 | DDR_DMIB1 | A_ADDRESS_COMMAND | B_BYTE1 | L8 | actual_interconnect_only | track:DDR_CAA0:L8:656:0 | track:DDR_DMIB1:L8:684:0 | 5.2 | 5.0984 | False | 3 | 0.1195 | 0.3585 | False | False | False
DDR_CAA0 | DDR_DMIB1 | A_ADDRESS_COMMAND | B_BYTE1 | L8 | all_inner_layer_traces | track:DDR_CAA0:L8:656:0 | track:DDR_DMIB1:L8:684:0 | 5.2 | 5.0984 | False | 3 | 0.1195 | 0.3585 | False | False | False
DDR_CAA0 | DDR_DQA10 | A_ADDRESS_COMMAND | A_BYTE1 | L8 | actual_interconnect_only | track:DDR_CAA0:L8:656:0 | track:DDR_DQA10:L8:678:8 | 0.975 | 0.8734 | False | 3 | 0.1195 | 0.3585 | False | False | False
DDR_CAA0 | DDR_DQA10 | A_ADDRESS_COMMAND | A_BYTE1 | L8 | all_inner_layer_traces | track:DDR_CAA0:L8:656:0 | track:DDR_DQA10:L8:678:8 | 0.975 | 0.8734 | False | 3 | 0.1195 | 0.3585 | False | False | False
DDR_CAA0 | DDR_DQA11 | A_ADDRESS_COMMAND | A_BYTE1 | L8 | actual_interconnect_only | track:DDR_CAA0:L8:656:0 | track:DDR_DQA11:L8:705:10 | 1.625 | 1.5234 | False | 3 | 0.1195 | 0.3585 | False | False | False
DDR_CAA0 | DDR_DQA11 | A_ADDRESS_COMMAND | A_BYTE1 | L8 | all_inner_layer_traces | track:DDR_CAA0:L8:656:0 | track:DDR_DQA11:L8:705:10 | 1.625 | 1.5234 | False | 3 | 0.1195 | 0.3585 | False | False | False
DDR_CAA0 | DDR_DQA12 | A_ADDRESS_COMMAND | A_BYTE1 | L8 | actual_interconnect_only | track:DDR_CAA0:L8:656:0 | track:DDR_DQA12:L8:688:10 | 0.325 | 0.2234 | False | 3 | 0.1195 | 0.3585 | True | True | False
DDR_CAA0 | DDR_DQA12 | A_ADDRESS_COMMAND | A_BYTE1 | L8 | all_inner_layer_traces | track:DDR_CAA0:L8:656:0 | track:DDR_DQA12:L8:688:10 | 0.325 | 0.2234 | False | 3 | 0.1195 | 0.3585 | True | True | False
DDR_CAA0 | DDR_DQA13 | A_ADDRESS_COMMAND | A_BYTE1 | L8 | actual_interconnect_only | track:DDR_CAA0:L8:656:0 | track:DDR_DQA13:L8:693:11 | 0.975 | 0.8734 | False | 3 | 0.1195 | 0.3585 | False | False | False
DDR_CAA0 | DDR_DQA13 | A_ADDRESS_COMMAND | A_BYTE1 | L8 | all_inner_layer_traces | track:DDR_CAA0:L8:656:0 | track:DDR_DQA13:L8:693:11 | 0.975 | 0.8734 | False | 3 | 0.1195 | 0.3585 | False | False | False
DDR_CAA0 | DDR_DQA14 | A_ADDRESS_COMMAND | A_BYTE1 | L8 | actual_interconnect_only | track:DDR_CAA0:L8:656:0 | track:DDR_DQA14:L8:683:4 | 2.925 | 2.8234 | False | 3 | 0.1195 | 0.3585 | False | False | False
DDR_CAA0 | DDR_DQA14 | A_ADDRESS_COMMAND | A_BYTE1 | L8 | all_inner_layer_traces | track:DDR_CAA0:L8:656:0 | track:DDR_DQA14:L8:683:4 | 2.925 | 2.8234 | False | 3 | 0.1195 | 0.3585 | False | False | False
DDR_CAA0 | DDR_DQA15 | A_ADDRESS_COMMAND | A_BYTE1 | L8 | actual_interconnect_only | track:DDR_CAA0:L8:656:0 | track:DDR_DQA15:L8:698:1 | 3.16875 | 3.06715 | False | 3 | 0.1195 | 0.3585 | False | False | False
DDR_CAA0 | DDR_DQA15 | A_ADDRESS_COMMAND | A_BYTE1 | L8 | all_inner_layer_traces | track:DDR_CAA0:L8:656:0 | track:DDR_DQA15:L8:698:1 | 3.16875 | 3.06715 | False | 3 | 0.1195 | 0.3585 | False | False | False
DDR_CAA0 | DDR_DQA3 | A_ADDRESS_COMMAND | A_BYTE0 | L8 | actual_interconnect_only | track:DDR_CAA0:L8:656:5 | track:DDR_DQA3:L8:649:49 | 1.3 | 1.1984 | False | 3 | 0.1195 | 0.3585 | False | False | False
DDR_CAA0 | DDR_DQA3 | A_ADDRESS_COMMAND | A_BYTE0 | L8 | all_inner_layer_traces | track:DDR_CAA0:L8:656:5 | track:DDR_DQA3:L8:649:49 | 1.3 | 1.1984 | False | 3 | 0.1195 | 0.3585 | False | False | False
DDR_CAA0 | DDR_DQA7 | A_ADDRESS_COMMAND | A_BYTE0 | L8 | actual_interconnect_only | track:DDR_CAA0:L8:656:5 | track:DDR_DQA7:L8:669:31 | 4.2154477817 | 4.1138477817 | False | 3 | 0.1195 | 0.3585 | False | False | False
DDR_CAA0 | DDR_DQA7 | A_ADDRESS_COMMAND | A_BYTE0 | L8 | all_inner_layer_traces | track:DDR_CAA0:L8:656:5 | track:DDR_DQA7:L8:669:31 | 4.2154477817 | 4.1138477817 | False | 3 | 0.1195 | 0.3585 | False | False | False
DDR_CAA0 | DDR_DQA9 | A_ADDRESS_COMMAND | A_BYTE1 | L8 | actual_interconnect_only | track:DDR_CAA0:L8:656:0 | track:DDR_DQA9:L8:686:0 | 2.8379404944 | 2.7363404944 | False | 3 | 0.1195 | 0.3585 | False | False | False
DDR_CAA0 | DDR_DQA9 | A_ADDRESS_COMMAND | A_BYTE1 | L8 | all_inner_layer_traces | track:DDR_CAA0:L8:656:0 | track:DDR_DQA9:L8:686:0 | 2.8379404944 | 2.7363404944 | False | 3 | 0.1195 | 0.3585 | False | False | False
DDR_CAA0 | DDR_DQB0 | A_ADDRESS_COMMAND | B_BYTE0 | L8 | actual_interconnect_only | track:DDR_CAA0:L8:656:0 | track:DDR_DQB0:L8:653:11 | 6.5115402364 | 6.4099402364 | False | 3 | 0.1195 | 0.3585 | False | False | False
DDR_CAA0 | DDR_DQB0 | A_ADDRESS_COMMAND | B_BYTE0 | L8 | all_inner_layer_traces | track:DDR_CAA0:L8:656:0 | track:DDR_DQB0:L8:653:11 | 6.5115402364 | 6.4099402364 | False | 3 | 0.1195 | 0.3585 | False | False | False
DDR_CAA0 | DDR_DQB1 | A_ADDRESS_COMMAND | B_BYTE0 | L8 | actual_interconnect_only | track:DDR_CAA0:L8:656:0 | track:DDR_DQB1:L8:662:17 | 5.8628198207 | 5.7612198207 | False | 3 | 0.1195 | 0.3585 | False | False | False
DDR_CAA0 | DDR_DQB1 | A_ADDRESS_COMMAND | B_BYTE0 | L8 | all_inner_layer_traces | track:DDR_CAA0:L8:656:0 | track:DDR_DQB1:L8:662:17 | 5.8628198207 | 5.7612198207 | False | 3 | 0.1195 | 0.3585 | False | False | False
DDR_CAA0 | DDR_DQB11 | A_ADDRESS_COMMAND | B_BYTE1 | L8 | actual_interconnect_only | track:DDR_CAA0:L8:656:0 | track:DDR_DQB11:L8:694:54 | 2.2807961877 | 2.1791961877 | False | 3 | 0.1195 | 0.3585 | False | False | False
DDR_CAA0 | DDR_DQB11 | A_ADDRESS_COMMAND | B_BYTE1 | L8 | all_inner_layer_traces | track:DDR_CAA0:L8:656:0 | track:DDR_DQB11:L8:694:54 | 2.2807961877 | 2.1791961877 | False | 3 | 0.1195 | 0.3585 | False | False | False
DDR_CAA0 | DDR_DQB3 | A_ADDRESS_COMMAND | B_BYTE0 | L8 | actual_interconnect_only | track:DDR_CAA0:L8:656:0 | track:DDR_DQB3:L8:646:28 | 3.9192035224 | 3.8176035224 | False | 3 | 0.1195 | 0.3585 | False | False | False
DDR_CAA0 | DDR_DQB3 | A_ADDRESS_COMMAND | B_BYTE0 | L8 | all_inner_layer_traces | track:DDR_CAA0:L8:656:0 | track:DDR_DQB3:L8:646:28 | 3.9192035224 | 3.8176035224 | False | 3 | 0.1195 | 0.3585 | False | False | False
DDR_CAA0 | DDR_DQB5 | A_ADDRESS_COMMAND | B_BYTE0 | L8 | actual_interconnect_only | track:DDR_CAA0:L8:656:0 | track:DDR_DQB5:L8:665:39 | 3.5786912762 | 3.4770912762 | False | 3 | 0.1195 | 0.3585 | False | False | False
DDR_CAA0 | DDR_DQB5 | A_ADDRESS_COMMAND | B_BYTE0 | L8 | all_inner_layer_traces | track:DDR_CAA0:L8:656:0 | track:DDR_DQB5:L8:665:39 | 3.5786912762 | 3.4770912762 | False | 3 | 0.1195 | 0.3585 | False | False | False
DDR_CAA0 | DDR_DQB6 | A_ADDRESS_COMMAND | B_BYTE0 | L8 | actual_interconnect_only | track:DDR_CAA0:L8:656:0 | track:DDR_DQB6:L8:664:5 | 5.85 | 5.7484 | False | 3 | 0.1195 | 0.3585 | False | False | False
DDR_CAA0 | DDR_DQB6 | A_ADDRESS_COMMAND | B_BYTE0 | L8 | all_inner_layer_traces | track:DDR_CAA0:L8:656:0 | track:DDR_DQB6:L8:664:5 | 5.85 | 5.7484 | False | 3 | 0.1195 | 0.3585 | False | False | False
DDR_CAA0 | DDR_DQB7 | A_ADDRESS_COMMAND | B_BYTE0 | L8 | actual_interconnect_only | track:DDR_CAA0:L8:656:0 | track:DDR_DQB7:L8:660:7 | 6.5 | 6.3984 | False | 3 | 0.1195 | 0.3585 | False | False | False
DDR_CAA0 | DDR_DQB7 | A_ADDRESS_COMMAND | B_BYTE0 | L8 | all_inner_layer_traces | track:DDR_CAA0:L8:656:0 | track:DDR_DQB7:L8:660:7 | 6.5 | 6.3984 | False | 3 | 0.1195 | 0.3585 | False | False | False
DDR_CAA0 | DDR_DQSA1_N | A_ADDRESS_COMMAND | A_BYTE1 | L8 | actual_interconnect_only | track:DDR_CAA0:L8:656:0 | track:DDR_DQSA1_N:L8:687:0 | 3.9 | 3.7984 | False | 3 | 0.1195 | 0.3585 | False | False | False
DDR_CAA0 | DDR_DQSA1_N | A_ADDRESS_COMMAND | A_BYTE1 | L8 | all_inner_layer_traces | track:DDR_CAA0:L8:656:0 | track:DDR_DQSA1_N:L8:687:0 | 3.9 | 3.7984 | False | 3 | 0.1195 | 0.3585 | False | False | False
DDR_CAA0 | DDR_DQSA1_P | A_ADDRESS_COMMAND | A_BYTE1 | L8 | actual_interconnect_only | track:DDR_CAA0:L8:656:0 | track:DDR_DQSA1_P:L8:710:0 | 3.9 | 3.7984 | False | 3 | 0.1195 | 0.3585 | False | False | False
DDR_CAA0 | DDR_DQSA1_P | A_ADDRESS_COMMAND | A_BYTE1 | L8 | all_inner_layer_traces | track:DDR_CAA0:L8:656:0 | track:DDR_DQSA1_P:L8:710:0 | 3.9 | 3.7984 | False | 3 | 0.1195 | 0.3585 | False | False | False
DDR_CAA1 | DDR_CAA2 | A_ADDRESS_COMMAND | A_ADDRESS_COMMAND | L3 | actual_interconnect_only | track:DDR_CAA1:L3:647:4 | track:DDR_CAA2:L3:689:9 | 1.05625 | 0.95465 | False | 3 | 0.13 | 0.39 | False | False | False
DDR_CAA1 | DDR_CAA2 | A_ADDRESS_COMMAND | A_ADDRESS_COMMAND | L3 | all_inner_layer_traces | track:DDR_CAA1:L3:647:4 | track:DDR_CAA2:L3:689:9 | 1.05625 | 0.95465 | False | 3 | 0.13 | 0.39 | False | False | False
DDR_CAA1 | DDR_CAA3 | A_ADDRESS_COMMAND | A_ADDRESS_COMMAND | L3 | actual_interconnect_only | track:DDR_CAA1:L3:647:4 | track:DDR_CAA3:L3:709:3 | 1.3 | 1.1984 | False | 3 | 0.13 | 0.39 | False | False | False
DDR_CAA1 | DDR_CAA3 | A_ADDRESS_COMMAND | A_ADDRESS_COMMAND | L3 | all_inner_layer_traces | track:DDR_CAA1:L3:647:4 | track:DDR_CAA3:L3:709:3 | 1.3 | 1.1984 | False | 3 | 0.13 | 0.39 | False | False | False
DDR_CAA1 | DDR_CAA4 | A_ADDRESS_COMMAND | A_ADDRESS_COMMAND | L3 | actual_interconnect_only | track:DDR_CAA1:L3:647:0 | track:DDR_CAA4:L3:702:0 | 0.65 | 0.5484 | False | 3 | 0.13 | 0.39 | False | False | False
DDR_CAA1 | DDR_CAA4 | A_ADDRESS_COMMAND | A_ADDRESS_COMMAND | L3 | all_inner_layer_traces | track:DDR_CAA1:L3:647:0 | track:DDR_CAA4:L3:702:0 | 0.65 | 0.5484 | False | 3 | 0.13 | 0.39 | False | False | False
DDR_CAA1 | DDR_CAA5 | A_ADDRESS_COMMAND | A_ADDRESS_COMMAND | L3 | actual_interconnect_only | track:DDR_CAA1:L3:647:0 | track:DDR_CAA5:L3:699:3 | 1.7819516162 | 1.6803516162 | False | 3 | 0.13 | 0.39 | False | False | False
DDR_CAA1 | DDR_CAA5 | A_ADDRESS_COMMAND | A_ADDRESS_COMMAND | L3 | all_inner_layer_traces | track:DDR_CAA1:L3:647:0 | track:DDR_CAA5:L3:699:3 | 1.7819516162 | 1.6803516162 | False | 3 | 0.13 | 0.39 | False | False | False
DDR_CAA1 | DDR_CAB2 | A_ADDRESS_COMMAND | B_ADDRESS_COMMAND | L3 | actual_interconnect_only | track:DDR_CAA1:L3:647:4 | track:DDR_CAB2:L3:696:19 | 1.625 | 1.5234 | False | 3 | 0.13 | 0.39 | False | False | False
DDR_CAA1 | DDR_CAB2 | A_ADDRESS_COMMAND | B_ADDRESS_COMMAND | L3 | all_inner_layer_traces | track:DDR_CAA1:L3:647:4 | track:DDR_CAB2:L3:696:19 | 1.625 | 1.5234 | False | 3 | 0.13 | 0.39 | False | False | False
DDR_CAA1 | DDR_CLKA_N | A_ADDRESS_COMMAND | A_ADDRESS_COMMAND | L3 | actual_interconnect_only | track:DDR_CAA1:L3:647:5 | track:DDR_CLKA_N:L3:680:17 | 2.2195597114 | 2.1179597114 | False | 3 | 0.13 | 0.39 | False | False | False
DDR_CAA1 | DDR_CLKA_N | A_ADDRESS_COMMAND | A_ADDRESS_COMMAND | L3 | all_inner_layer_traces | track:DDR_CAA1:L3:647:5 | track:DDR_CLKA_N:L3:680:17 | 2.2195597114 | 2.1179597114 | False | 3 | 0.13 | 0.39 | False | False | False
DDR_CAA1 | DDR_CLKA_P | A_ADDRESS_COMMAND | A_ADDRESS_COMMAND | L3 | actual_interconnect_only | track:DDR_CAA1:L3:647:0 | track:DDR_CLKA_P:L3:676:8 | 0.325 | 0.2234 | False | 3 | 0.13 | 0.39 | True | True | False
DDR_CAA1 | DDR_CLKA_P | A_ADDRESS_COMMAND | A_ADDRESS_COMMAND | L3 | all_inner_layer_traces | track:DDR_CAA1:L3:647:0 | track:DDR_CLKA_P:L3:676:8 | 0.325 | 0.2234 | False | 3 | 0.13 | 0.39 | True | True | False
DDR_CAA1 | DDR_CLKB_N | A_ADDRESS_COMMAND | B_ADDRESS_COMMAND | L3 | actual_interconnect_only | track:DDR_CAA1:L3:647:4 | track:DDR_CLKB_N:L3:701:13 | 0.975 | 0.8734 | False | 3 | 0.13 | 0.39 | False | False | False
DDR_CAA1 | DDR_CLKB_N | A_ADDRESS_COMMAND | B_ADDRESS_COMMAND | L3 | all_inner_layer_traces | track:DDR_CAA1:L3:647:4 | track:DDR_CLKB_N:L3:701:13 | 0.975 | 0.8734 | False | 3 | 0.13 | 0.39 | False | False | False
DDR_CAA1 | DDR_CLKB_P | A_ADDRESS_COMMAND | B_ADDRESS_COMMAND | L3 | actual_interconnect_only | track:DDR_CAA1:L3:647:3 | track:DDR_CLKB_P:L3:700:11 | 0.65 | 0.5484 | False | 3 | 0.13 | 0.39 | False | False | False
DDR_CAA1 | DDR_CLKB_P | A_ADDRESS_COMMAND | B_ADDRESS_COMMAND | L3 | all_inner_layer_traces | track:DDR_CAA1:L3:647:3 | track:DDR_CLKB_P:L3:700:11 | 0.65 | 0.5484 | False | 3 | 0.13 | 0.39 | False | False | False
DDR_CAA1 | DDR_CSA0 | A_ADDRESS_COMMAND | A_ADDRESS_COMMAND | L3 | actual_interconnect_only | track:DDR_CAA1:L3:647:7 | track:DDR_CSA0:L3:679:13 | 1.6080486039 | 1.5064486039 | False | 3 | 0.13 | 0.39 | False | False | False
DDR_CAA1 | DDR_CSA0 | A_ADDRESS_COMMAND | A_ADDRESS_COMMAND | L3 | all_inner_layer_traces | track:DDR_CAA1:L3:647:7 | track:DDR_CSA0:L3:679:13 | 1.6080486039 | 1.5064486039 | False | 3 | 0.13 | 0.39 | False | False | False
DDR_CAA1 | DDR_DMIA0 | A_ADDRESS_COMMAND | A_BYTE0 | L3 | actual_interconnect_only | track:DDR_CAA1:L3:647:11 | track:DDR_DMIA0:L3:661:50 | 3.9812058475 | 3.8796058475 | False | 3 | 0.13 | 0.39 | False | False | False
DDR_CAA1 | DDR_DMIA0 | A_ADDRESS_COMMAND | A_BYTE0 | L3 | all_inner_layer_traces | track:DDR_CAA1:L3:647:11 | track:DDR_DMIA0:L3:661:50 | 3.9812058475 | 3.8796058475 | False | 3 | 0.13 | 0.39 | False | False | False
DDR_CAA1 | DDR_DQA0 | A_ADDRESS_COMMAND | A_BYTE0 | L3 | actual_interconnect_only | track:DDR_CAA1:L3:647:11 | track:DDR_DQA0:L3:648:38 | 4.55 | 4.4484 | False | 3 | 0.13 | 0.39 | False | False | False
DDR_CAA1 | DDR_DQA0 | A_ADDRESS_COMMAND | A_BYTE0 | L3 | all_inner_layer_traces | track:DDR_CAA1:L3:647:11 | track:DDR_DQA0:L3:648:38 | 4.55 | 4.4484 | False | 3 | 0.13 | 0.39 | False | False | False
DDR_CAA1 | DDR_DQA1 | A_ADDRESS_COMMAND | A_BYTE0 | L3 | actual_interconnect_only | track:DDR_CAA1:L3:647:11 | track:DDR_DQA1:L3:658:14 | 2.3227896079 | 2.2211896079 | False | 3 | 0.13 | 0.39 | False | False | False
DDR_CAA1 | DDR_DQA1 | A_ADDRESS_COMMAND | A_BYTE0 | L3 | all_inner_layer_traces | track:DDR_CAA1:L3:647:11 | track:DDR_DQA1:L3:658:14 | 2.3227896079 | 2.2211896079 | False | 3 | 0.13 | 0.39 | False | False | False
DDR_CAA1 | DDR_DQA2 | A_ADDRESS_COMMAND | A_BYTE0 | L3 | actual_interconnect_only | track:DDR_CAA1:L3:647:11 | track:DDR_DQA2:L3:668:76 | 2.6 | 2.4984 | False | 3 | 0.13 | 0.39 | False | False | False
DDR_CAA1 | DDR_DQA2 | A_ADDRESS_COMMAND | A_BYTE0 | L3 | all_inner_layer_traces | track:DDR_CAA1:L3:647:11 | track:DDR_DQA2:L3:668:76 | 2.6 | 2.4984 | False | 3 | 0.13 | 0.39 | False | False | False
DDR_CAA1 | DDR_DQA4 | A_ADDRESS_COMMAND | A_BYTE0 | L3 | actual_interconnect_only | track:DDR_CAA1:L3:647:11 | track:DDR_DQA4:L3:659:66 | 0.975 | 0.8734 | False | 3 | 0.13 | 0.39 | False | False | False
DDR_CAA1 | DDR_DQA4 | A_ADDRESS_COMMAND | A_BYTE0 | L3 | all_inner_layer_traces | track:DDR_CAA1:L3:647:11 | track:DDR_DQA4:L3:659:66 | 0.975 | 0.8734 | False | 3 | 0.13 | 0.39 | False | False | False
DDR_CAA1 | DDR_DQA5 | A_ADDRESS_COMMAND | A_BYTE0 | L3 | actual_interconnect_only | track:DDR_CAA1:L3:647:11 | track:DDR_DQA5:L3:667:20 | 3.0528675045 | 2.9512675045 | False | 3 | 0.13 | 0.39 | False | False | False
DDR_CAA1 | DDR_DQA5 | A_ADDRESS_COMMAND | A_BYTE0 | L3 | all_inner_layer_traces | track:DDR_CAA1:L3:647:11 | track:DDR_DQA5:L3:667:20 | 3.0528675045 | 2.9512675045 | False | 3 | 0.13 | 0.39 | False | False | False
DDR_CAA1 | DDR_DQA6 | A_ADDRESS_COMMAND | A_BYTE0 | L3 | actual_interconnect_only | track:DDR_CAA1:L3:647:11 | track:DDR_DQA6:L3:674:10 | 4.102533516 | 4.000933516 | False | 3 | 0.13 | 0.39 | False | False | False
DDR_CAA1 | DDR_DQA6 | A_ADDRESS_COMMAND | A_BYTE0 | L3 | all_inner_layer_traces | track:DDR_CAA1:L3:647:11 | track:DDR_DQA6:L3:674:10 | 4.102533516 | 4.000933516 | False | 3 | 0.13 | 0.39 | False | False | False
DDR_CAA1 | DDR_DQA8 | A_ADDRESS_COMMAND | A_BYTE1 | L3 | actual_interconnect_only | track:DDR_CAA1:L3:647:0 | track:DDR_DQA8:L3:708:0 | 5.2101463511 | 5.1085463511 | False | 3 | 0.13 | 0.39 | False | False | False
DDR_CAA1 | DDR_DQA8 | A_ADDRESS_COMMAND | A_BYTE1 | L3 | all_inner_layer_traces | track:DDR_CAA1:L3:647:0 | track:DDR_DQA8:L3:708:0 | 5.2101463511 | 5.1085463511 | False | 3 | 0.13 | 0.39 | False | False | False
DDR_CAA1 | DDR_DQB10 | A_ADDRESS_COMMAND | B_BYTE1 | L3 | actual_interconnect_only | track:DDR_CAA1:L3:647:4 | track:DDR_DQB10:L3:703:5 | 3.575 | 3.4734 | False | 3 | 0.13 | 0.39 | False | False | False
DDR_CAA1 | DDR_DQB10 | A_ADDRESS_COMMAND | B_BYTE1 | L3 | all_inner_layer_traces | track:DDR_CAA1:L3:647:4 | track:DDR_DQB10:L3:703:5 | 3.575 | 3.4734 | False | 3 | 0.13 | 0.39 | False | False | False
DDR_CAA1 | DDR_DQB12 | A_ADDRESS_COMMAND | B_BYTE1 | L3 | actual_interconnect_only | track:DDR_CAA1:L3:647:4 | track:DDR_DQB12:L3:691:7 | 2.925 | 2.8234 | False | 3 | 0.13 | 0.39 | False | False | False
DDR_CAA1 | DDR_DQB12 | A_ADDRESS_COMMAND | B_BYTE1 | L3 | all_inner_layer_traces | track:DDR_CAA1:L3:647:4 | track:DDR_DQB12:L3:691:7 | 2.925 | 2.8234 | False | 3 | 0.13 | 0.39 | False | False | False
DDR_CAA1 | DDR_DQB13 | A_ADDRESS_COMMAND | B_BYTE1 | L3 | actual_interconnect_only | track:DDR_CAA1:L3:647:4 | track:DDR_DQB13:L3:673:31 | 3.575 | 3.4734 | False | 3 | 0.13 | 0.39 | False | False | False
DDR_CAA1 | DDR_DQB13 | A_ADDRESS_COMMAND | B_BYTE1 | L3 | all_inner_layer_traces | track:DDR_CAA1:L3:647:4 | track:DDR_DQB13:L3:673:31 | 3.575 | 3.4734 | False | 3 | 0.13 | 0.39 | False | False | False
DDR_CAA1 | DDR_DQB14 | A_ADDRESS_COMMAND | B_BYTE1 | L3 | actual_interconnect_only | track:DDR_CAA1:L3:647:4 | track:DDR_DQB14:L3:681:0 | 4.875 | 4.7734 | False | 3 | 0.13 | 0.39 | False | False | False
DDR_CAA1 | DDR_DQB14 | A_ADDRESS_COMMAND | B_BYTE1 | L3 | all_inner_layer_traces | track:DDR_CAA1:L3:647:4 | track:DDR_DQB14:L3:681:0 | 4.875 | 4.7734 | False | 3 | 0.13 | 0.39 | False | False | False
DDR_CAA1 | DDR_DQB15 | A_ADDRESS_COMMAND | B_BYTE1 | L3 | actual_interconnect_only | track:DDR_CAA1:L3:647:4 | track:DDR_DQB15:L3:692:0 | 5.525 | 5.4234 | False | 3 | 0.13 | 0.39 | False | False | False
DDR_CAA1 | DDR_DQB15 | A_ADDRESS_COMMAND | B_BYTE1 | L3 | all_inner_layer_traces | track:DDR_CAA1:L3:647:4 | track:DDR_DQB15:L3:692:0 | 5.525 | 5.4234 | False | 3 | 0.13 | 0.39 | False | False | False
DDR_CAA1 | DDR_DQB2 | A_ADDRESS_COMMAND | B_BYTE0 | L3 | actual_interconnect_only | track:DDR_CAA1:L3:647:6 | track:DDR_DQB2:L3:655:75 | 1.38125 | 1.27965 | False | 3 | 0.13 | 0.39 | False | False | False
DDR_CAA1 | DDR_DQB2 | A_ADDRESS_COMMAND | B_BYTE0 | L3 | all_inner_layer_traces | track:DDR_CAA1:L3:647:6 | track:DDR_DQB2:L3:655:75 | 1.38125 | 1.27965 | False | 3 | 0.13 | 0.39 | False | False | False
DDR_CAA1 | DDR_DQB4 | A_ADDRESS_COMMAND | B_BYTE0 | L3 | actual_interconnect_only | track:DDR_CAA1:L3:647:6 | track:DDR_DQB4:L3:663:91 | 0.73125 | 0.62965 | False | 3 | 0.13 | 0.39 | False | False | False
DDR_CAA1 | DDR_DQB4 | A_ADDRESS_COMMAND | B_BYTE0 | L3 | all_inner_layer_traces | track:DDR_CAA1:L3:647:6 | track:DDR_DQB4:L3:663:91 | 0.73125 | 0.62965 | False | 3 | 0.13 | 0.39 | False | False | False
DDR_CAA1 | DDR_DQB8 | A_ADDRESS_COMMAND | B_BYTE1 | L3 | actual_interconnect_only | track:DDR_CAA1:L3:647:3 | track:DDR_DQB8:L3:706:0 | 4.8756770363 | 4.7740770363 | False | 3 | 0.13 | 0.39 | False | False | False
DDR_CAA1 | DDR_DQB8 | A_ADDRESS_COMMAND | B_BYTE1 | L3 | all_inner_layer_traces | track:DDR_CAA1:L3:647:3 | track:DDR_DQB8:L3:706:0 | 4.8756770363 | 4.7740770363 | False | 3 | 0.13 | 0.39 | False | False | False
DDR_CAA1 | DDR_DQB9 | A_ADDRESS_COMMAND | B_BYTE1 | L3 | actual_interconnect_only | track:DDR_CAA1:L3:647:3 | track:DDR_DQB9:L3:704:4 | 4.55 | 4.4484 | False | 3 | 0.13 | 0.39 | False | False | False
DDR_CAA1 | DDR_DQB9 | A_ADDRESS_COMMAND | B_BYTE1 | L3 | all_inner_layer_traces | track:DDR_CAA1:L3:647:3 | track:DDR_DQB9:L3:704:4 | 4.55 | 4.4484 | False | 3 | 0.13 | 0.39 | False | False | False
DDR_CAA1 | DDR_DQSA0_N | A_ADDRESS_COMMAND | A_BYTE0 | L3 | actual_interconnect_only | track:DDR_CAA1:L3:647:11 | track:DDR_DQSA0_N:L3:657:29 | 2.7202941017 | 2.6186941017 | False | 3 | 0.13 | 0.39 | False | False | False
DDR_CAA1 | DDR_DQSA0_N | A_ADDRESS_COMMAND | A_BYTE0 | L3 | all_inner_layer_traces | track:DDR_CAA1:L3:647:11 | track:DDR_DQSA0_N:L3:657:29 | 2.7202941017 | 2.6186941017 | False | 3 | 0.13 | 0.39 | False | False | False
DDR_CAA1 | DDR_DQSA0_P | A_ADDRESS_COMMAND | A_BYTE0 | L3 | actual_interconnect_only | track:DDR_CAA1:L3:647:11 | track:DDR_DQSA0_P:L3:652:51 | 3.3470135942 | 3.2454135942 | False | 3 | 0.13 | 0.39 | False | False | False
DDR_CAA1 | DDR_DQSA0_P | A_ADDRESS_COMMAND | A_BYTE0 | L3 | all_inner_layer_traces | track:DDR_CAA1:L3:647:11 | track:DDR_DQSA0_P:L3:652:51 | 3.3470135942 | 3.2454135942 | False | 3 | 0.13 | 0.39 | False | False | False
DDR_CAA1 | DDR_DQSB0_N | A_ADDRESS_COMMAND | B_BYTE0 | L3 | actual_interconnect_only | track:DDR_CAA1:L3:647:6 | track:DDR_DQSB0_N:L3:650:44 | 2.68125 | 2.57965 | False | 3 | 0.13 | 0.39 | False | False | False
DDR_CAA1 | DDR_DQSB0_N | A_ADDRESS_COMMAND | B_BYTE0 | L3 | all_inner_layer_traces | track:DDR_CAA1:L3:647:6 | track:DDR_DQSB0_N:L3:650:44 | 2.68125 | 2.57965 | False | 3 | 0.13 | 0.39 | False | False | False
DDR_CAA1 | DDR_DQSB0_P | A_ADDRESS_COMMAND | B_BYTE0 | L3 | actual_interconnect_only | track:DDR_CAA1:L3:647:6 | track:DDR_DQSB0_P:L3:651:67 | 2.03125 | 1.92965 | False | 3 | 0.13 | 0.39 | False | False | False
DDR_CAA1 | DDR_DQSB0_P | A_ADDRESS_COMMAND | B_BYTE0 | L3 | all_inner_layer_traces | track:DDR_CAA1:L3:647:6 | track:DDR_DQSB0_P:L3:651:67 | 2.03125 | 1.92965 | False | 3 | 0.13 | 0.39 | False | False | False
DDR_CAA1 | DDR_DQSB1_N | A_ADDRESS_COMMAND | B_BYTE1 | L3 | actual_interconnect_only | track:DDR_CAA1:L3:647:4 | track:DDR_DQSB1_N:L3:697:36 | 2.6 | 2.4984 | False | 3 | 0.13 | 0.39 | False | False | False
DDR_CAA1 | DDR_DQSB1_N | A_ADDRESS_COMMAND | B_BYTE1 | L3 | all_inner_layer_traces | track:DDR_CAA1:L3:647:4 | track:DDR_DQSB1_N:L3:697:36 | 2.6 | 2.4984 | False | 3 | 0.13 | 0.39 | False | False | False
DDR_CAA1 | DDR_DQSB1_P | A_ADDRESS_COMMAND | B_BYTE1 | L3 | actual_interconnect_only | track:DDR_CAA1:L3:647:4 | track:DDR_DQSB1_P:L3:690:13 | 4.225 | 4.1234 | False | 3 | 0.13 | 0.39 | False | False | False
DDR_CAA1 | DDR_DQSB1_P | A_ADDRESS_COMMAND | B_BYTE1 | L3 | all_inner_layer_traces | track:DDR_CAA1:L3:647:4 | track:DDR_DQSB1_P:L3:690:13 | 4.225 | 4.1234 | False | 3 | 0.13 | 0.39 | False | False | False
DDR_CAA2 | DDR_CAA3 | A_ADDRESS_COMMAND | A_ADDRESS_COMMAND | L3 | actual_interconnect_only | track:DDR_CAA2:L3:689:8 | track:DDR_CAA3:L3:709:3 | 0.2088846871 | 0.1072846871 | False | 3 | 0.13 | 0.39 | True | True | True
DDR_CAA2 | DDR_CAA3 | A_ADDRESS_COMMAND | A_ADDRESS_COMMAND | L3 | all_inner_layer_traces | track:DDR_CAA2:L3:689:8 | track:DDR_CAA3:L3:709:3 | 0.2088846871 | 0.1072846871 | False | 3 | 0.13 | 0.39 | True | True | True
DDR_CAA2 | DDR_CAA4 | A_ADDRESS_COMMAND | A_ADDRESS_COMMAND | L3 | actual_interconnect_only | track:DDR_CAA2:L3:689:0 | track:DDR_CAA4:L3:702:1 | 0.325 | 0.2234 | False | 3 | 0.13 | 0.39 | True | True | False
DDR_CAA2 | DDR_CAA4 | A_ADDRESS_COMMAND | A_ADDRESS_COMMAND | L3 | all_inner_layer_traces | track:DDR_CAA2:L3:689:0 | track:DDR_CAA4:L3:702:1 | 0.325 | 0.2234 | False | 3 | 0.13 | 0.39 | True | True | False
DDR_CAA2 | DDR_CAA5 | A_ADDRESS_COMMAND | A_ADDRESS_COMMAND | L3 | actual_interconnect_only | track:DDR_CAA2:L3:689:0 | track:DDR_CAA5:L3:699:3 | 0.3350023321 | 0.2334023321 | False | 3 | 0.13 | 0.39 | True | True | False
DDR_CAA2 | DDR_CAA5 | A_ADDRESS_COMMAND | A_ADDRESS_COMMAND | L3 | all_inner_layer_traces | track:DDR_CAA2:L3:689:0 | track:DDR_CAA5:L3:699:3 | 0.3350023321 | 0.2334023321 | False | 3 | 0.13 | 0.39 | True | True | False
DDR_CAA2 | DDR_CAB2 | A_ADDRESS_COMMAND | B_ADDRESS_COMMAND | L3 | actual_interconnect_only | track:DDR_CAA2:L3:689:10 | track:DDR_CAB2:L3:696:19 | 2.7100074954 | 2.6084074954 | False | 3 | 0.13 | 0.39 | False | False | False
DDR_CAA2 | DDR_CAB2 | A_ADDRESS_COMMAND | B_ADDRESS_COMMAND | L3 | all_inner_layer_traces | track:DDR_CAA2:L3:689:10 | track:DDR_CAB2:L3:696:19 | 2.7100074954 | 2.6084074954 | False | 3 | 0.13 | 0.39 | False | False | False
DDR_CAA2 | DDR_CLKA_N | A_ADDRESS_COMMAND | A_ADDRESS_COMMAND | L3 | actual_interconnect_only | track:DDR_CAA2:L3:689:22 | track:DDR_CLKA_N:L3:680:16 | 0.24375 | 0.14215 | False | 3 | 0.13 | 0.39 | True | True | True
DDR_CAA2 | DDR_CLKA_N | A_ADDRESS_COMMAND | A_ADDRESS_COMMAND | L3 | all_inner_layer_traces | track:DDR_CAA2:L3:689:22 | track:DDR_CLKA_N:L3:680:16 | 0.24375 | 0.14215 | False | 3 | 0.13 | 0.39 | True | True | True
DDR_CAA2 | DDR_CLKA_P | A_ADDRESS_COMMAND | A_ADDRESS_COMMAND | L3 | actual_interconnect_only | track:DDR_CAA2:L3:689:9 | track:DDR_CLKA_P:L3:676:9 | 0.40625 | 0.30465 | False | 3 | 0.13 | 0.39 | True | True | False
DDR_CAA2 | DDR_CLKA_P | A_ADDRESS_COMMAND | A_ADDRESS_COMMAND | L3 | all_inner_layer_traces | track:DDR_CAA2:L3:689:9 | track:DDR_CLKA_P:L3:676:9 | 0.40625 | 0.30465 | False | 3 | 0.13 | 0.39 | True | True | False
DDR_CAA2 | DDR_CLKB_N | A_ADDRESS_COMMAND | B_ADDRESS_COMMAND | L3 | actual_interconnect_only | track:DDR_CAA2:L3:689:10 | track:DDR_CLKB_N:L3:701:13 | 2.0690615324 | 1.9674615324 | False | 3 | 0.13 | 0.39 | False | False | False
DDR_CAA2 | DDR_CLKB_N | A_ADDRESS_COMMAND | B_ADDRESS_COMMAND | L3 | all_inner_layer_traces | track:DDR_CAA2:L3:689:10 | track:DDR_CLKB_N:L3:701:13 | 2.0690615324 | 1.9674615324 | False | 3 | 0.13 | 0.39 | False | False | False
DDR_CAA2 | DDR_CLKB_P | A_ADDRESS_COMMAND | B_ADDRESS_COMMAND | L3 | actual_interconnect_only | track:DDR_CAA2:L3:689:9 | track:DDR_CLKB_P:L3:700:11 | 1.70625 | 1.60465 | False | 3 | 0.13 | 0.39 | False | False | False
DDR_CAA2 | DDR_CLKB_P | A_ADDRESS_COMMAND | B_ADDRESS_COMMAND | L3 | all_inner_layer_traces | track:DDR_CAA2:L3:689:9 | track:DDR_CLKB_P:L3:700:11 | 1.70625 | 1.60465 | False | 3 | 0.13 | 0.39 | False | False | False
DDR_CAA2 | DDR_CSA0 | A_ADDRESS_COMMAND | A_ADDRESS_COMMAND | L3 | actual_interconnect_only | track:DDR_CAA2:L3:689:23 | track:DDR_CSA0:L3:679:4 | 0.975 | 0.8734 | False | 3 | 0.13 | 0.39 | False | False | False
DDR_CAA2 | DDR_CSA0 | A_ADDRESS_COMMAND | A_ADDRESS_COMMAND | L3 | all_inner_layer_traces | track:DDR_CAA2:L3:689:23 | track:DDR_CSA0:L3:679:4 | 0.975 | 0.8734 | False | 3 | 0.13 | 0.39 | False | False | False
DDR_CAA2 | DDR_DMIA0 | A_ADDRESS_COMMAND | A_BYTE0 | L3 | actual_interconnect_only | track:DDR_CAA2:L3:689:0 | track:DDR_DMIA0:L3:661:0 | 3.5003571246 | 3.3987571246 | False | 3 | 0.13 | 0.39 | False | False | False
DDR_CAA2 | DDR_DMIA0 | A_ADDRESS_COMMAND | A_BYTE0 | L3 | all_inner_layer_traces | track:DDR_CAA2:L3:689:0 | track:DDR_DMIA0:L3:661:0 | 3.5003571246 | 3.3987571246 | False | 3 | 0.13 | 0.39 | False | False | False
DDR_CAA2 | DDR_DQA0 | A_ADDRESS_COMMAND | A_BYTE0 | L3 | actual_interconnect_only | track:DDR_CAA2:L3:689:23 | track:DDR_DQA0:L3:648:11 | 4.9298873276 | 4.8282873276 | False | 3 | 0.13 | 0.39 | False | False | False
DDR_CAA2 | DDR_DQA0 | A_ADDRESS_COMMAND | A_BYTE0 | L3 | all_inner_layer_traces | track:DDR_CAA2:L3:689:23 | track:DDR_DQA0:L3:648:11 | 4.9298873276 | 4.8282873276 | False | 3 | 0.13 | 0.39 | False | False | False
DDR_CAA2 | DDR_DQA1 | A_ADDRESS_COMMAND | A_BYTE0 | L3 | actual_interconnect_only | track:DDR_CAA2:L3:689:23 | track:DDR_DQA1:L3:658:14 | 1.625 | 1.5234 | False | 3 | 0.13 | 0.39 | False | False | False
DDR_CAA2 | DDR_DQA1 | A_ADDRESS_COMMAND | A_BYTE0 | L3 | all_inner_layer_traces | track:DDR_CAA2:L3:689:23 | track:DDR_DQA1:L3:658:14 | 1.625 | 1.5234 | False | 3 | 0.13 | 0.39 | False | False | False
DDR_CAA2 | DDR_DQA2 | A_ADDRESS_COMMAND | A_BYTE0 | L3 | actual_interconnect_only | track:DDR_CAA2:L3:689:0 | track:DDR_DQA2:L3:668:1 | 2.7957557118 | 2.6941557118 | False | 3 | 0.13 | 0.39 | False | False | False
DDR_CAA2 | DDR_DQA2 | A_ADDRESS_COMMAND | A_BYTE0 | L3 | all_inner_layer_traces | track:DDR_CAA2:L3:689:0 | track:DDR_DQA2:L3:668:1 | 2.7957557118 | 2.6941557118 | False | 3 | 0.13 | 0.39 | False | False | False
DDR_CAA2 | DDR_DQA4 | A_ADDRESS_COMMAND | A_BYTE0 | L3 | actual_interconnect_only | track:DDR_CAA2:L3:689:0 | track:DDR_DQA4:L3:659:0 | 3.25 | 3.1484 | False | 3 | 0.13 | 0.39 | False | False | False
DDR_CAA2 | DDR_DQA4 | A_ADDRESS_COMMAND | A_BYTE0 | L3 | all_inner_layer_traces | track:DDR_CAA2:L3:689:0 | track:DDR_DQA4:L3:659:0 | 3.25 | 3.1484 | False | 3 | 0.13 | 0.39 | False | False | False
DDR_CAA2 | DDR_DQA5 | A_ADDRESS_COMMAND | A_BYTE0 | L3 | actual_interconnect_only | track:DDR_CAA2:L3:689:23 | track:DDR_DQA5:L3:667:14 | 2.275 | 2.1734 | False | 3 | 0.13 | 0.39 | False | False | False
DDR_CAA2 | DDR_DQA5 | A_ADDRESS_COMMAND | A_BYTE0 | L3 | all_inner_layer_traces | track:DDR_CAA2:L3:689:23 | track:DDR_DQA5:L3:667:14 | 2.275 | 2.1734 | False | 3 | 0.13 | 0.39 | False | False | False
DDR_CAA2 | DDR_DQA6 | A_ADDRESS_COMMAND | A_BYTE0 | L3 | actual_interconnect_only | track:DDR_CAA2:L3:689:23 | track:DDR_DQA6:L3:674:10 | 2.925 | 2.8234 | False | 3 | 0.13 | 0.39 | False | False | False
DDR_CAA2 | DDR_DQA6 | A_ADDRESS_COMMAND | A_BYTE0 | L3 | all_inner_layer_traces | track:DDR_CAA2:L3:689:23 | track:DDR_DQA6:L3:674:10 | 2.925 | 2.8234 | False | 3 | 0.13 | 0.39 | False | False | False
DDR_CAA2 | DDR_DQA8 | A_ADDRESS_COMMAND | A_BYTE1 | L3 | actual_interconnect_only | track:DDR_CAA2:L3:689:0 | track:DDR_DQA8:L3:708:0 | 3.9 | 3.7984 | False | 3 | 0.13 | 0.39 | False | False | False
DDR_CAA2 | DDR_DQA8 | A_ADDRESS_COMMAND | A_BYTE1 | L3 | all_inner_layer_traces | track:DDR_CAA2:L3:689:0 | track:DDR_DQA8:L3:708:0 | 3.9 | 3.7984 | False | 3 | 0.13 | 0.39 | False | False | False
DDR_CAA2 | DDR_DQB10 | A_ADDRESS_COMMAND | B_BYTE1 | L3 | actual_interconnect_only | track:DDR_CAA2:L3:689:10 | track:DDR_DQB10:L3:703:5 | 4.63125 | 4.52965 | False | 3 | 0.13 | 0.39 | False | False | False
DDR_CAA2 | DDR_DQB10 | A_ADDRESS_COMMAND | B_BYTE1 | L3 | all_inner_layer_traces | track:DDR_CAA2:L3:689:10 | track:DDR_DQB10:L3:703:5 | 4.63125 | 4.52965 | False | 3 | 0.13 | 0.39 | False | False | False
DDR_CAA2 | DDR_DQB12 | A_ADDRESS_COMMAND | B_BYTE1 | L3 | actual_interconnect_only | track:DDR_CAA2:L3:689:10 | track:DDR_DQB12:L3:691:7 | 4.0006737714 | 3.8990737714 | False | 3 | 0.13 | 0.39 | False | False | False
DDR_CAA2 | DDR_DQB12 | A_ADDRESS_COMMAND | B_BYTE1 | L3 | all_inner_layer_traces | track:DDR_CAA2:L3:689:10 | track:DDR_DQB12:L3:691:7 | 4.0006737714 | 3.8990737714 | False | 3 | 0.13 | 0.39 | False | False | False
DDR_CAA2 | DDR_DQB13 | A_ADDRESS_COMMAND | B_BYTE1 | L3 | actual_interconnect_only | track:DDR_CAA2:L3:689:10 | track:DDR_DQB13:L3:673:31 | 4.6479582211 | 4.5463582211 | False | 3 | 0.13 | 0.39 | False | False | False
DDR_CAA2 | DDR_DQB13 | A_ADDRESS_COMMAND | B_BYTE1 | L3 | all_inner_layer_traces | track:DDR_CAA2:L3:689:10 | track:DDR_DQB13:L3:673:31 | 4.6479582211 | 4.5463582211 | False | 3 | 0.13 | 0.39 | False | False | False
DDR_CAA2 | DDR_DQB14 | A_ADDRESS_COMMAND | B_BYTE1 | L3 | actual_interconnect_only | track:DDR_CAA2:L3:689:10 | track:DDR_DQB14:L3:681:9 | 5.9443053105 | 5.8427053105 | False | 3 | 0.13 | 0.39 | False | False | False
DDR_CAA2 | DDR_DQB14 | A_ADDRESS_COMMAND | B_BYTE1 | L3 | all_inner_layer_traces | track:DDR_CAA2:L3:689:10 | track:DDR_DQB14:L3:681:9 | 5.9443053105 | 5.8427053105 | False | 3 | 0.13 | 0.39 | False | False | False
DDR_CAA2 | DDR_DQB15 | A_ADDRESS_COMMAND | B_BYTE1 | L3 | actual_interconnect_only | track:DDR_CAA2:L3:689:10 | track:DDR_DQB15:L3:692:5 | 6.5930183243 | 6.4914183243 | False | 3 | 0.13 | 0.39 | False | False | False
DDR_CAA2 | DDR_DQB15 | A_ADDRESS_COMMAND | B_BYTE1 | L3 | all_inner_layer_traces | track:DDR_CAA2:L3:689:10 | track:DDR_DQB15:L3:692:5 | 6.5930183243 | 6.4914183243 | False | 3 | 0.13 | 0.39 | False | False | False
DDR_CAA2 | DDR_DQB2 | A_ADDRESS_COMMAND | B_BYTE0 | L3 | actual_interconnect_only | track:DDR_CAA2:L3:689:10 | track:DDR_DQB2:L3:655:87 | 4.4827621228 | 4.3811621228 | False | 3 | 0.13 | 0.39 | False | False | False
DDR_CAA2 | DDR_DQB2 | A_ADDRESS_COMMAND | B_BYTE0 | L3 | all_inner_layer_traces | track:DDR_CAA2:L3:689:10 | track:DDR_DQB2:L3:655:87 | 4.4827621228 | 4.3811621228 | False | 3 | 0.13 | 0.39 | False | False | False
DDR_CAA2 | DDR_DQB4 | A_ADDRESS_COMMAND | B_BYTE0 | L3 | actual_interconnect_only | track:DDR_CAA2:L3:689:10 | track:DDR_DQB4:L3:663:103 | 4.0625 | 3.9609 | False | 3 | 0.13 | 0.39 | False | False | False
DDR_CAA2 | DDR_DQB4 | A_ADDRESS_COMMAND | B_BYTE0 | L3 | all_inner_layer_traces | track:DDR_CAA2:L3:689:10 | track:DDR_DQB4:L3:663:103 | 4.0625 | 3.9609 | False | 3 | 0.13 | 0.39 | False | False | False
DDR_CAA2 | DDR_DQB8 | A_ADDRESS_COMMAND | B_BYTE1 | L3 | actual_interconnect_only | track:DDR_CAA2:L3:689:3 | track:DDR_DQB8:L3:706:0 | 6.2181469557 | 6.1165469557 | False | 3 | 0.13 | 0.39 | False | False | False
DDR_CAA2 | DDR_DQB8 | A_ADDRESS_COMMAND | B_BYTE1 | L3 | all_inner_layer_traces | track:DDR_CAA2:L3:689:3 | track:DDR_DQB8:L3:706:0 | 6.2181469557 | 6.1165469557 | False | 3 | 0.13 | 0.39 | False | False | False
DDR_CAA2 | DDR_DQB9 | A_ADDRESS_COMMAND | B_BYTE1 | L3 | actual_interconnect_only | track:DDR_CAA2:L3:689:9 | track:DDR_DQB9:L3:704:4 | 5.60625 | 5.50465 | False | 3 | 0.13 | 0.39 | False | False | False
DDR_CAA2 | DDR_DQB9 | A_ADDRESS_COMMAND | B_BYTE1 | L3 | all_inner_layer_traces | track:DDR_CAA2:L3:689:9 | track:DDR_DQB9:L3:704:4 | 5.60625 | 5.50465 | False | 3 | 0.13 | 0.39 | False | False | False
DDR_CAA2 | DDR_DQSA0_N | A_ADDRESS_COMMAND | A_BYTE0 | L3 | actual_interconnect_only | track:DDR_CAA2:L3:689:23 | track:DDR_DQSA0_N:L3:657:12 | 4.225 | 4.1234 | False | 3 | 0.13 | 0.39 | False | False | False
DDR_CAA2 | DDR_DQSA0_N | A_ADDRESS_COMMAND | A_BYTE0 | L3 | all_inner_layer_traces | track:DDR_CAA2:L3:689:23 | track:DDR_DQSA0_N:L3:657:12 | 4.225 | 4.1234 | False | 3 | 0.13 | 0.39 | False | False | False
DDR_CAA2 | DDR_DQSA0_P | A_ADDRESS_COMMAND | A_BYTE0 | L3 | actual_interconnect_only | track:DDR_CAA2:L3:689:0 | track:DDR_DQSA0_P:L3:652:1 | 3.9269899414 | 3.8253899414 | False | 3 | 0.13 | 0.39 | False | False | False
DDR_CAA2 | DDR_DQSA0_P | A_ADDRESS_COMMAND | A_BYTE0 | L3 | all_inner_layer_traces | track:DDR_CAA2:L3:689:0 | track:DDR_DQSA0_P:L3:652:1 | 3.9269899414 | 3.8253899414 | False | 3 | 0.13 | 0.39 | False | False | False
DDR_CAA2 | DDR_DQSB0_N | A_ADDRESS_COMMAND | B_BYTE0 | L3 | actual_interconnect_only | track:DDR_CAA2:L3:689:10 | track:DDR_DQSB0_N:L3:650:46 | 5.5202185192 | 5.4186185192 | False | 3 | 0.13 | 0.39 | False | False | False
DDR_CAA2 | DDR_DQSB0_N | A_ADDRESS_COMMAND | B_BYTE0 | L3 | all_inner_layer_traces | track:DDR_CAA2:L3:689:10 | track:DDR_DQSB0_N:L3:650:46 | 5.5202185192 | 5.4186185192 | False | 3 | 0.13 | 0.39 | False | False | False
DDR_CAA2 | DDR_DQSB0_P | A_ADDRESS_COMMAND | B_BYTE0 | L3 | actual_interconnect_only | track:DDR_CAA2:L3:689:10 | track:DDR_DQSB0_P:L3:651:77 | 4.9462501579 | 4.8446501579 | False | 3 | 0.13 | 0.39 | False | False | False
DDR_CAA2 | DDR_DQSB0_P | A_ADDRESS_COMMAND | B_BYTE0 | L3 | all_inner_layer_traces | track:DDR_CAA2:L3:689:10 | track:DDR_DQSB0_P:L3:651:77 | 4.9462501579 | 4.8446501579 | False | 3 | 0.13 | 0.39 | False | False | False
DDR_CAA2 | DDR_DQSB1_N | A_ADDRESS_COMMAND | B_BYTE1 | L3 | actual_interconnect_only | track:DDR_CAA2:L3:689:10 | track:DDR_DQSB1_N:L3:697:37 | 3.6598593296 | 3.5582593296 | False | 3 | 0.13 | 0.39 | False | False | False
DDR_CAA2 | DDR_DQSB1_N | A_ADDRESS_COMMAND | B_BYTE1 | L3 | all_inner_layer_traces | track:DDR_CAA2:L3:689:10 | track:DDR_DQSB1_N:L3:697:37 | 3.6598593296 | 3.5582593296 | False | 3 | 0.13 | 0.39 | False | False | False
DDR_CAA2 | DDR_DQSB1_P | A_ADDRESS_COMMAND | B_BYTE1 | L3 | actual_interconnect_only | track:DDR_CAA2:L3:689:10 | track:DDR_DQSB1_P:L3:690:13 | 5.28125 | 5.17965 | False | 3 | 0.13 | 0.39 | False | False | False
DDR_CAA2 | DDR_DQSB1_P | A_ADDRESS_COMMAND | B_BYTE1 | L3 | all_inner_layer_traces | track:DDR_CAA2:L3:689:10 | track:DDR_DQSB1_P:L3:690:13 | 5.28125 | 5.17965 | False | 3 | 0.13 | 0.39 | False | False | False
DDR_CAA3 | DDR_CAA4 | A_ADDRESS_COMMAND | A_ADDRESS_COMMAND | L3 | actual_interconnect_only | track:DDR_CAA3:L3:709:5 | track:DDR_CAA4:L3:702:11 | 0.6250312492 | 0.5234312492 | False | 3 | 0.13 | 0.39 | False | False | False
DDR_CAA3 | DDR_CAA4 | A_ADDRESS_COMMAND | A_ADDRESS_COMMAND | L3 | all_inner_layer_traces | track:DDR_CAA3:L3:709:5 | track:DDR_CAA4:L3:702:11 | 0.6250312492 | 0.5234312492 | False | 3 | 0.13 | 0.39 | False | False | False
DDR_CAA3 | DDR_CAA5 | A_ADDRESS_COMMAND | A_ADDRESS_COMMAND | L3 | actual_interconnect_only | track:DDR_CAA3:L3:709:0 | track:DDR_CAA5:L3:699:4 | 0.325 | 0.2234 | False | 3 | 0.13 | 0.39 | True | True | False
DDR_CAA3 | DDR_CAA5 | A_ADDRESS_COMMAND | A_ADDRESS_COMMAND | L3 | all_inner_layer_traces | track:DDR_CAA3:L3:709:0 | track:DDR_CAA5:L3:699:4 | 0.325 | 0.2234 | False | 3 | 0.13 | 0.39 | True | True | False
DDR_CAA3 | DDR_CAB2 | A_ADDRESS_COMMAND | B_ADDRESS_COMMAND | L3 | actual_interconnect_only | track:DDR_CAA3:L3:709:4 | track:DDR_CAB2:L3:696:19 | 3.1338873624 | 3.0322873624 | False | 3 | 0.13 | 0.39 | False | False | False
DDR_CAA3 | DDR_CAB2 | A_ADDRESS_COMMAND | B_ADDRESS_COMMAND | L3 | all_inner_layer_traces | track:DDR_CAA3:L3:709:4 | track:DDR_CAB2:L3:696:19 | 3.1338873624 | 3.0322873624 | False | 3 | 0.13 | 0.39 | False | False | False
DDR_CAA3 | DDR_CLKA_N | A_ADDRESS_COMMAND | A_ADDRESS_COMMAND | L3 | actual_interconnect_only | track:DDR_CAA3:L3:709:7 | track:DDR_CLKA_N:L3:680:6 | 0.22543361 | 0.12383361 | False | 3 | 0.13 | 0.39 | True | True | True
DDR_CAA3 | DDR_CLKA_N | A_ADDRESS_COMMAND | A_ADDRESS_COMMAND | L3 | all_inner_layer_traces | track:DDR_CAA3:L3:709:7 | track:DDR_CLKA_N:L3:680:6 | 0.22543361 | 0.12383361 | False | 3 | 0.13 | 0.39 | True | True | True
DDR_CAA3 | DDR_CLKA_P | A_ADDRESS_COMMAND | A_ADDRESS_COMMAND | L3 | actual_interconnect_only | track:DDR_CAA3:L3:709:3 | track:DDR_CLKA_P:L3:676:9 | 0.65 | 0.5484 | False | 3 | 0.13 | 0.39 | False | False | False
DDR_CAA3 | DDR_CLKA_P | A_ADDRESS_COMMAND | A_ADDRESS_COMMAND | L3 | all_inner_layer_traces | track:DDR_CAA3:L3:709:3 | track:DDR_CLKA_P:L3:676:9 | 0.65 | 0.5484 | False | 3 | 0.13 | 0.39 | False | False | False
DDR_CAA3 | DDR_CLKB_N | A_ADDRESS_COMMAND | B_ADDRESS_COMMAND | L3 | actual_interconnect_only | track:DDR_CAA3:L3:709:4 | track:DDR_CLKB_N:L3:701:13 | 2.5379617806 | 2.4363617806 | False | 3 | 0.13 | 0.39 | False | False | False
DDR_CAA3 | DDR_CLKB_N | A_ADDRESS_COMMAND | B_ADDRESS_COMMAND | L3 | all_inner_layer_traces | track:DDR_CAA3:L3:709:4 | track:DDR_CLKB_N:L3:701:13 | 2.5379617806 | 2.4363617806 | False | 3 | 0.13 | 0.39 | False | False | False
DDR_CAA3 | DDR_CLKB_P | A_ADDRESS_COMMAND | B_ADDRESS_COMMAND | L3 | actual_interconnect_only | track:DDR_CAA3:L3:709:3 | track:DDR_CLKB_P:L3:700:11 | 1.95 | 1.8484 | False | 3 | 0.13 | 0.39 | False | False | False
DDR_CAA3 | DDR_CLKB_P | A_ADDRESS_COMMAND | B_ADDRESS_COMMAND | L3 | all_inner_layer_traces | track:DDR_CAA3:L3:709:3 | track:DDR_CLKB_P:L3:700:11 | 1.95 | 1.8484 | False | 3 | 0.13 | 0.39 | False | False | False
DDR_CAA3 | DDR_CSA0 | A_ADDRESS_COMMAND | A_ADDRESS_COMMAND | L3 | actual_interconnect_only | track:DDR_CAA3:L3:709:9 | track:DDR_CSA0:L3:679:4 | 0.975 | 0.8734 | False | 3 | 0.13 | 0.39 | False | False | False
DDR_CAA3 | DDR_CSA0 | A_ADDRESS_COMMAND | A_ADDRESS_COMMAND | L3 | all_inner_layer_traces | track:DDR_CAA3:L3:709:9 | track:DDR_CSA0:L3:679:4 | 0.975 | 0.8734 | False | 3 | 0.13 | 0.39 | False | False | False
DDR_CAA3 | DDR_DMIA0 | A_ADDRESS_COMMAND | A_BYTE0 | L3 | actual_interconnect_only | track:DDR_CAA3:L3:709:0 | track:DDR_DMIA0:L3:661:0 | 3.7901187316 | 3.6885187316 | False | 3 | 0.13 | 0.39 | False | False | False
DDR_CAA3 | DDR_DMIA0 | A_ADDRESS_COMMAND | A_BYTE0 | L3 | all_inner_layer_traces | track:DDR_CAA3:L3:709:0 | track:DDR_DMIA0:L3:661:0 | 3.7901187316 | 3.6885187316 | False | 3 | 0.13 | 0.39 | False | False | False
DDR_CAA3 | DDR_DQA0 | A_ADDRESS_COMMAND | A_BYTE0 | L3 | actual_interconnect_only | track:DDR_CAA3:L3:709:9 | track:DDR_DQA0:L3:648:11 | 4.5662227963 | 4.4646227963 | False | 3 | 0.13 | 0.39 | False | False | False
DDR_CAA3 | DDR_DQA0 | A_ADDRESS_COMMAND | A_BYTE0 | L3 | all_inner_layer_traces | track:DDR_CAA3:L3:709:9 | track:DDR_DQA0:L3:648:11 | 4.5662227963 | 4.4646227963 | False | 3 | 0.13 | 0.39 | False | False | False
DDR_CAA3 | DDR_DQA1 | A_ADDRESS_COMMAND | A_BYTE0 | L3 | actual_interconnect_only | track:DDR_CAA3:L3:709:9 | track:DDR_DQA1:L3:658:14 | 1.625 | 1.5234 | False | 3 | 0.13 | 0.39 | False | False | False
DDR_CAA3 | DDR_DQA1 | A_ADDRESS_COMMAND | A_BYTE0 | L3 | all_inner_layer_traces | track:DDR_CAA3:L3:709:9 | track:DDR_DQA1:L3:658:14 | 1.625 | 1.5234 | False | 3 | 0.13 | 0.39 | False | False | False
DDR_CAA3 | DDR_DQA2 | A_ADDRESS_COMMAND | A_BYTE0 | L3 | actual_interconnect_only | track:DDR_CAA3:L3:709:0 | track:DDR_DQA2:L3:668:1 | 3.2173358544 | 3.1157358544 | False | 3 | 0.13 | 0.39 | False | False | False
DDR_CAA3 | DDR_DQA2 | A_ADDRESS_COMMAND | A_BYTE0 | L3 | all_inner_layer_traces | track:DDR_CAA3:L3:709:0 | track:DDR_DQA2:L3:668:1 | 3.2173358544 | 3.1157358544 | False | 3 | 0.13 | 0.39 | False | False | False
DDR_CAA3 | DDR_DQA4 | A_ADDRESS_COMMAND | A_BYTE0 | L3 | actual_interconnect_only | track:DDR_CAA3:L3:709:0 | track:DDR_DQA4:L3:659:0 | 3.6769552622 | 3.5753552622 | False | 3 | 0.13 | 0.39 | False | False | False
DDR_CAA3 | DDR_DQA4 | A_ADDRESS_COMMAND | A_BYTE0 | L3 | all_inner_layer_traces | track:DDR_CAA3:L3:709:0 | track:DDR_DQA4:L3:659:0 | 3.6769552622 | 3.5753552622 | False | 3 | 0.13 | 0.39 | False | False | False
DDR_CAA3 | DDR_DQA5 | A_ADDRESS_COMMAND | A_BYTE0 | L3 | actual_interconnect_only | track:DDR_CAA3:L3:709:9 | track:DDR_DQA5:L3:667:14 | 2.275 | 2.1734 | False | 3 | 0.13 | 0.39 | False | False | False
DDR_CAA3 | DDR_DQA5 | A_ADDRESS_COMMAND | A_BYTE0 | L3 | all_inner_layer_traces | track:DDR_CAA3:L3:709:9 | track:DDR_DQA5:L3:667:14 | 2.275 | 2.1734 | False | 3 | 0.13 | 0.39 | False | False | False
DDR_CAA3 | DDR_DQA6 | A_ADDRESS_COMMAND | A_BYTE0 | L3 | actual_interconnect_only | track:DDR_CAA3:L3:709:9 | track:DDR_DQA6:L3:674:10 | 2.925 | 2.8234 | False | 3 | 0.13 | 0.39 | False | False | False
DDR_CAA3 | DDR_DQA6 | A_ADDRESS_COMMAND | A_BYTE0 | L3 | all_inner_layer_traces | track:DDR_CAA3:L3:709:9 | track:DDR_DQA6:L3:674:10 | 2.925 | 2.8234 | False | 3 | 0.13 | 0.39 | False | False | False
DDR_CAA3 | DDR_DQA8 | A_ADDRESS_COMMAND | A_BYTE1 | L3 | actual_interconnect_only | track:DDR_CAA3:L3:709:9 | track:DDR_DQA8:L3:708:10 | 3.6465362418 | 3.5449362418 | False | 3 | 0.13 | 0.39 | False | False | False
DDR_CAA3 | DDR_DQA8 | A_ADDRESS_COMMAND | A_BYTE1 | L3 | all_inner_layer_traces | track:DDR_CAA3:L3:709:9 | track:DDR_DQA8:L3:708:10 | 3.6465362418 | 3.5449362418 | False | 3 | 0.13 | 0.39 | False | False | False
DDR_CAA3 | DDR_DQB10 | A_ADDRESS_COMMAND | B_BYTE1 | L3 | actual_interconnect_only | track:DDR_CAA3:L3:709:4 | track:DDR_DQB10:L3:703:5 | 4.875 | 4.7734 | False | 3 | 0.13 | 0.39 | False | False | False
DDR_CAA3 | DDR_DQB10 | A_ADDRESS_COMMAND | B_BYTE1 | L3 | all_inner_layer_traces | track:DDR_CAA3:L3:709:4 | track:DDR_DQB10:L3:703:5 | 4.875 | 4.7734 | False | 3 | 0.13 | 0.39 | False | False | False
DDR_CAA3 | DDR_DQB12 | A_ADDRESS_COMMAND | B_BYTE1 | L3 | actual_interconnect_only | track:DDR_CAA3:L3:709:4 | track:DDR_DQB12:L3:691:7 | 4.3722133983 | 4.2706133983 | False | 3 | 0.13 | 0.39 | False | False | False
DDR_CAA3 | DDR_DQB12 | A_ADDRESS_COMMAND | B_BYTE1 | L3 | all_inner_layer_traces | track:DDR_CAA3:L3:709:4 | track:DDR_DQB12:L3:691:7 | 4.3722133983 | 4.2706133983 | False | 3 | 0.13 | 0.39 | False | False | False
DDR_CAA3 | DDR_DQB13 | A_ADDRESS_COMMAND | B_BYTE1 | L3 | actual_interconnect_only | track:DDR_CAA3:L3:709:4 | track:DDR_DQB13:L3:673:31 | 5.003124024 | 4.901524024 | False | 3 | 0.13 | 0.39 | False | False | False
DDR_CAA3 | DDR_DQB13 | A_ADDRESS_COMMAND | B_BYTE1 | L3 | all_inner_layer_traces | track:DDR_CAA3:L3:709:4 | track:DDR_DQB13:L3:673:31 | 5.003124024 | 4.901524024 | False | 3 | 0.13 | 0.39 | False | False | False
DDR_CAA3 | DDR_DQB14 | A_ADDRESS_COMMAND | B_BYTE1 | L3 | actual_interconnect_only | track:DDR_CAA3:L3:709:3 | track:DDR_DQB14:L3:681:0 | 6.2091162817 | 6.1075162817 | False | 3 | 0.13 | 0.39 | False | False | False
DDR_CAA3 | DDR_DQB14 | A_ADDRESS_COMMAND | B_BYTE1 | L3 | all_inner_layer_traces | track:DDR_CAA3:L3:709:3 | track:DDR_DQB14:L3:681:0 | 6.2091162817 | 6.1075162817 | False | 3 | 0.13 | 0.39 | False | False | False
DDR_CAA3 | DDR_DQB15 | A_ADDRESS_COMMAND | B_BYTE1 | L3 | actual_interconnect_only | track:DDR_CAA3:L3:709:4 | track:DDR_DQB15:L3:692:5 | 6.9170983801 | 6.8154983801 | False | 3 | 0.13 | 0.39 | False | False | False
DDR_CAA3 | DDR_DQB15 | A_ADDRESS_COMMAND | B_BYTE1 | L3 | all_inner_layer_traces | track:DDR_CAA3:L3:709:4 | track:DDR_DQB15:L3:692:5 | 6.9170983801 | 6.8154983801 | False | 3 | 0.13 | 0.39 | False | False | False
DDR_CAA3 | DDR_DQB2 | A_ADDRESS_COMMAND | B_BYTE0 | L3 | actual_interconnect_only | track:DDR_CAA3:L3:709:4 | track:DDR_DQB2:L3:655:87 | 5.1911056746 | 5.0895056746 | False | 3 | 0.13 | 0.39 | False | False | False
DDR_CAA3 | DDR_DQB2 | A_ADDRESS_COMMAND | B_BYTE0 | L3 | all_inner_layer_traces | track:DDR_CAA3:L3:709:4 | track:DDR_DQB2:L3:655:87 | 5.1911056746 | 5.0895056746 | False | 3 | 0.13 | 0.39 | False | False | False
DDR_CAA3 | DDR_DQB4 | A_ADDRESS_COMMAND | B_BYTE0 | L3 | actual_interconnect_only | track:DDR_CAA3:L3:709:4 | track:DDR_DQB4:L3:663:103 | 4.7999430335 | 4.6983430335 | False | 3 | 0.13 | 0.39 | False | False | False
DDR_CAA3 | DDR_DQB4 | A_ADDRESS_COMMAND | B_BYTE0 | L3 | all_inner_layer_traces | track:DDR_CAA3:L3:709:4 | track:DDR_DQB4:L3:663:103 | 4.7999430335 | 4.6983430335 | False | 3 | 0.13 | 0.39 | False | False | False
DDR_CAA3 | DDR_DQB8 | A_ADDRESS_COMMAND | B_BYTE1 | L3 | actual_interconnect_only | track:DDR_CAA3:L3:709:3 | track:DDR_DQB8:L3:706:2 | 6.5324191537 | 6.4308191537 | False | 3 | 0.13 | 0.39 | False | False | False
DDR_CAA3 | DDR_DQB8 | A_ADDRESS_COMMAND | B_BYTE1 | L3 | all_inner_layer_traces | track:DDR_CAA3:L3:709:3 | track:DDR_DQB8:L3:706:2 | 6.5324191537 | 6.4308191537 | False | 3 | 0.13 | 0.39 | False | False | False
DDR_CAA3 | DDR_DQB9 | A_ADDRESS_COMMAND | B_BYTE1 | L3 | actual_interconnect_only | track:DDR_CAA3:L3:709:3 | track:DDR_DQB9:L3:704:4 | 5.85 | 5.7484 | False | 3 | 0.13 | 0.39 | False | False | False
DDR_CAA3 | DDR_DQB9 | A_ADDRESS_COMMAND | B_BYTE1 | L3 | all_inner_layer_traces | track:DDR_CAA3:L3:709:3 | track:DDR_DQB9:L3:704:4 | 5.85 | 5.7484 | False | 3 | 0.13 | 0.39 | False | False | False
DDR_CAA3 | DDR_DQSA0_N | A_ADDRESS_COMMAND | A_BYTE0 | L3 | actual_interconnect_only | track:DDR_CAA3:L3:709:9 | track:DDR_DQSA0_N:L3:657:8 | 3.9621352356 | 3.8605352356 | False | 3 | 0.13 | 0.39 | False | False | False
DDR_CAA3 | DDR_DQSA0_N | A_ADDRESS_COMMAND | A_BYTE0 | L3 | all_inner_layer_traces | track:DDR_CAA3:L3:709:9 | track:DDR_DQSA0_N:L3:657:8 | 3.9621352356 | 3.8605352356 | False | 3 | 0.13 | 0.39 | False | False | False
DDR_CAA3 | DDR_DQSA0_P | A_ADDRESS_COMMAND | A_BYTE0 | L3 | actual_interconnect_only | track:DDR_CAA3:L3:709:0 | track:DDR_DQSA0_P:L3:652:1 | 4.2374815634 | 4.1358815634 | False | 3 | 0.13 | 0.39 | False | False | False
DDR_CAA3 | DDR_DQSA0_P | A_ADDRESS_COMMAND | A_BYTE0 | L3 | all_inner_layer_traces | track:DDR_CAA3:L3:709:0 | track:DDR_DQSA0_P:L3:652:1 | 4.2374815634 | 4.1358815634 | False | 3 | 0.13 | 0.39 | False | False | False
DDR_CAA3 | DDR_DQSB0_N | A_ADDRESS_COMMAND | B_BYTE0 | L3 | actual_interconnect_only | track:DDR_CAA3:L3:709:4 | track:DDR_DQSB0_N:L3:650:46 | 6.2314035839 | 6.1298035839 | False | 3 | 0.13 | 0.39 | False | False | False
DDR_CAA3 | DDR_DQSB0_N | A_ADDRESS_COMMAND | B_BYTE0 | L3 | all_inner_layer_traces | track:DDR_CAA3:L3:709:4 | track:DDR_DQSB0_N:L3:650:46 | 6.2314035839 | 6.1298035839 | False | 3 | 0.13 | 0.39 | False | False | False
DDR_CAA3 | DDR_DQSB0_P | A_ADDRESS_COMMAND | B_BYTE0 | L3 | actual_interconnect_only | track:DDR_CAA3:L3:709:4 | track:DDR_DQSB0_P:L3:651:79 | 5.6303377452 | 5.5287377452 | False | 3 | 0.13 | 0.39 | False | False | False
DDR_CAA3 | DDR_DQSB0_P | A_ADDRESS_COMMAND | B_BYTE0 | L3 | all_inner_layer_traces | track:DDR_CAA3:L3:709:4 | track:DDR_DQSB0_P:L3:651:79 | 5.6303377452 | 5.5287377452 | False | 3 | 0.13 | 0.39 | False | False | False
DDR_CAA3 | DDR_DQSB1_N | A_ADDRESS_COMMAND | B_BYTE1 | L3 | actual_interconnect_only | track:DDR_CAA3:L3:709:4 | track:DDR_DQSB1_N:L3:697:37 | 4.001098482 | 3.899498482 | False | 3 | 0.13 | 0.39 | False | False | False
DDR_CAA3 | DDR_DQSB1_N | A_ADDRESS_COMMAND | B_BYTE1 | L3 | all_inner_layer_traces | track:DDR_CAA3:L3:709:4 | track:DDR_DQSB1_N:L3:697:37 | 4.001098482 | 3.899498482 | False | 3 | 0.13 | 0.39 | False | False | False
DDR_CAA3 | DDR_DQSB1_P | A_ADDRESS_COMMAND | B_BYTE1 | L3 | actual_interconnect_only | track:DDR_CAA3:L3:709:4 | track:DDR_DQSB1_P:L3:690:14 | 5.5345505689 | 5.4329505689 | False | 3 | 0.13 | 0.39 | False | False | False
DDR_CAA3 | DDR_DQSB1_P | A_ADDRESS_COMMAND | B_BYTE1 | L3 | all_inner_layer_traces | track:DDR_CAA3:L3:709:4 | track:DDR_DQSB1_P:L3:690:14 | 5.5345505689 | 5.4329505689 | False | 3 | 0.13 | 0.39 | False | False | False
DDR_CAA4 | DDR_CAA5 | A_ADDRESS_COMMAND | A_ADDRESS_COMMAND | L3 | actual_interconnect_only | track:DDR_CAA4:L3:702:4 | track:DDR_CAA5:L3:699:0 | 0.325 | 0.2234 | False | 3 | 0.13 | 0.39 | True | True | False
DDR_CAA4 | DDR_CAA5 | A_ADDRESS_COMMAND | A_ADDRESS_COMMAND | L3 | all_inner_layer_traces | track:DDR_CAA4:L3:702:4 | track:DDR_CAA5:L3:699:0 | 0.325 | 0.2234 | False | 3 | 0.13 | 0.39 | True | True | False
DDR_CAA4 | DDR_CAB2 | A_ADDRESS_COMMAND | B_ADDRESS_COMMAND | L3 | actual_interconnect_only | track:DDR_CAA4:L3:702:0 | track:DDR_CAB2:L3:696:0 | 3.25 | 3.1484 | False | 3 | 0.13 | 0.39 | False | False | False
DDR_CAA4 | DDR_CAB2 | A_ADDRESS_COMMAND | B_ADDRESS_COMMAND | L3 | all_inner_layer_traces | track:DDR_CAA4:L3:702:0 | track:DDR_CAB2:L3:696:0 | 3.25 | 3.1484 | False | 3 | 0.13 | 0.39 | False | False | False
DDR_CAA4 | DDR_CLKA_N | A_ADDRESS_COMMAND | A_ADDRESS_COMMAND | L3 | actual_interconnect_only | track:DDR_CAA4:L3:702:7 | track:DDR_CLKA_N:L3:680:0 | 0.325 | 0.2234 | False | 3 | 0.13 | 0.39 | True | True | False
DDR_CAA4 | DDR_CLKA_N | A_ADDRESS_COMMAND | A_ADDRESS_COMMAND | L3 | all_inner_layer_traces | track:DDR_CAA4:L3:702:7 | track:DDR_CLKA_N:L3:680:0 | 0.325 | 0.2234 | False | 3 | 0.13 | 0.39 | True | True | False
DDR_CAA4 | DDR_CLKA_P | A_ADDRESS_COMMAND | A_ADDRESS_COMMAND | L3 | actual_interconnect_only | track:DDR_CAA4:L3:702:0 | track:DDR_CLKA_P:L3:676:6 | 0.325 | 0.2234 | False | 3 | 0.13 | 0.39 | True | True | False
DDR_CAA4 | DDR_CLKA_P | A_ADDRESS_COMMAND | A_ADDRESS_COMMAND | L3 | all_inner_layer_traces | track:DDR_CAA4:L3:702:0 | track:DDR_CLKA_P:L3:676:6 | 0.325 | 0.2234 | False | 3 | 0.13 | 0.39 | True | True | False
DDR_CAA4 | DDR_CLKB_N | A_ADDRESS_COMMAND | B_ADDRESS_COMMAND | L3 | actual_interconnect_only | track:DDR_CAA4:L3:702:0 | track:DDR_CLKB_N:L3:701:0 | 4.020027985 | 3.918427985 | False | 3 | 0.13 | 0.39 | False | False | False
DDR_CAA4 | DDR_CLKB_N | A_ADDRESS_COMMAND | B_ADDRESS_COMMAND | L3 | all_inner_layer_traces | track:DDR_CAA4:L3:702:0 | track:DDR_CLKB_N:L3:701:0 | 4.020027985 | 3.918427985 | False | 3 | 0.13 | 0.39 | False | False | False
DDR_CAA4 | DDR_CLKB_P | A_ADDRESS_COMMAND | B_ADDRESS_COMMAND | L3 | actual_interconnect_only | track:DDR_CAA4:L3:702:0 | track:DDR_CLKB_P:L3:700:11 | 1.625 | 1.5234 | False | 3 | 0.13 | 0.39 | False | False | False
DDR_CAA4 | DDR_CLKB_P | A_ADDRESS_COMMAND | B_ADDRESS_COMMAND | L3 | all_inner_layer_traces | track:DDR_CAA4:L3:702:0 | track:DDR_CLKB_P:L3:700:11 | 1.625 | 1.5234 | False | 3 | 0.13 | 0.39 | False | False | False
DDR_CAA4 | DDR_CSA0 | A_ADDRESS_COMMAND | A_ADDRESS_COMMAND | L3 | actual_interconnect_only | track:DDR_CAA4:L3:702:10 | track:DDR_CSA0:L3:679:0 | 0.325 | 0.2234 | False | 3 | 0.13 | 0.39 | True | True | False
DDR_CAA4 | DDR_CSA0 | A_ADDRESS_COMMAND | A_ADDRESS_COMMAND | L3 | all_inner_layer_traces | track:DDR_CAA4:L3:702:10 | track:DDR_CSA0:L3:679:0 | 0.325 | 0.2234 | False | 3 | 0.13 | 0.39 | True | True | False
DDR_CAA4 | DDR_DMIA0 | A_ADDRESS_COMMAND | A_BYTE0 | L3 | actual_interconnect_only | track:DDR_CAA4:L3:702:7 | track:DDR_DMIA0:L3:661:0 | 2.35625 | 2.25465 | False | 3 | 0.13 | 0.39 | False | False | False
DDR_CAA4 | DDR_DMIA0 | A_ADDRESS_COMMAND | A_BYTE0 | L3 | all_inner_layer_traces | track:DDR_CAA4:L3:702:7 | track:DDR_DMIA0:L3:661:0 | 2.35625 | 2.25465 | False | 3 | 0.13 | 0.39 | False | False | False
DDR_CAA4 | DDR_DQA0 | A_ADDRESS_COMMAND | A_BYTE0 | L3 | actual_interconnect_only | track:DDR_CAA4:L3:702:9 | track:DDR_DQA0:L3:648:5 | 3.7375 | 3.6359 | False | 3 | 0.13 | 0.39 | False | False | False
DDR_CAA4 | DDR_DQA0 | A_ADDRESS_COMMAND | A_BYTE0 | L3 | all_inner_layer_traces | track:DDR_CAA4:L3:702:9 | track:DDR_DQA0:L3:648:5 | 3.7375 | 3.6359 | False | 3 | 0.13 | 0.39 | False | False | False
DDR_CAA4 | DDR_DQA1 | A_ADDRESS_COMMAND | A_BYTE0 | L3 | actual_interconnect_only | track:DDR_CAA4:L3:702:9 | track:DDR_DQA1:L3:658:8 | 0.65 | 0.5484 | False | 3 | 0.13 | 0.39 | False | False | False
DDR_CAA4 | DDR_DQA1 | A_ADDRESS_COMMAND | A_BYTE0 | L3 | all_inner_layer_traces | track:DDR_CAA4:L3:702:9 | track:DDR_DQA1:L3:658:8 | 0.65 | 0.5484 | False | 3 | 0.13 | 0.39 | False | False | False
DDR_CAA4 | DDR_DQA2 | A_ADDRESS_COMMAND | A_BYTE0 | L3 | actual_interconnect_only | track:DDR_CAA4:L3:702:1 | track:DDR_DQA2:L3:668:1 | 1.8968003486 | 1.7952003486 | False | 3 | 0.13 | 0.39 | False | False | False
DDR_CAA4 | DDR_DQA2 | A_ADDRESS_COMMAND | A_BYTE0 | L3 | all_inner_layer_traces | track:DDR_CAA4:L3:702:1 | track:DDR_DQA2:L3:668:1 | 1.8968003486 | 1.7952003486 | False | 3 | 0.13 | 0.39 | False | False | False
DDR_CAA4 | DDR_DQA4 | A_ADDRESS_COMMAND | A_BYTE0 | L3 | actual_interconnect_only | track:DDR_CAA4:L3:702:1 | track:DDR_DQA4:L3:659:0 | 2.35625 | 2.25465 | False | 3 | 0.13 | 0.39 | False | False | False
DDR_CAA4 | DDR_DQA4 | A_ADDRESS_COMMAND | A_BYTE0 | L3 | all_inner_layer_traces | track:DDR_CAA4:L3:702:1 | track:DDR_DQA4:L3:659:0 | 2.35625 | 2.25465 | False | 3 | 0.13 | 0.39 | False | False | False
DDR_CAA4 | DDR_DQA5 | A_ADDRESS_COMMAND | A_BYTE0 | L3 | actual_interconnect_only | track:DDR_CAA4:L3:702:9 | track:DDR_DQA5:L3:667:4 | 1.3 | 1.1984 | False | 3 | 0.13 | 0.39 | False | False | False
DDR_CAA4 | DDR_DQA5 | A_ADDRESS_COMMAND | A_BYTE0 | L3 | all_inner_layer_traces | track:DDR_CAA4:L3:702:9 | track:DDR_DQA5:L3:667:4 | 1.3 | 1.1984 | False | 3 | 0.13 | 0.39 | False | False | False
DDR_CAA4 | DDR_DQA6 | A_ADDRESS_COMMAND | A_BYTE0 | L3 | actual_interconnect_only | track:DDR_CAA4:L3:702:9 | track:DDR_DQA6:L3:674:4 | 1.95 | 1.8484 | False | 3 | 0.13 | 0.39 | False | False | False
DDR_CAA4 | DDR_DQA6 | A_ADDRESS_COMMAND | A_BYTE0 | L3 | all_inner_layer_traces | track:DDR_CAA4:L3:702:9 | track:DDR_DQA6:L3:674:4 | 1.95 | 1.8484 | False | 3 | 0.13 | 0.39 | False | False | False
DDR_CAA4 | DDR_DQA8 | A_ADDRESS_COMMAND | A_BYTE1 | L3 | actual_interconnect_only | track:DDR_CAA4:L3:702:9 | track:DDR_DQA8:L3:708:0 | 2.2980970389 | 2.1964970389 | False | 3 | 0.13 | 0.39 | False | False | False
DDR_CAA4 | DDR_DQA8 | A_ADDRESS_COMMAND | A_BYTE1 | L3 | all_inner_layer_traces | track:DDR_CAA4:L3:702:9 | track:DDR_DQA8:L3:708:0 | 2.2980970389 | 2.1964970389 | False | 3 | 0.13 | 0.39 | False | False | False
DDR_CAA4 | DDR_DQB10 | A_ADDRESS_COMMAND | B_BYTE1 | L3 | actual_interconnect_only | track:DDR_CAA4:L3:702:0 | track:DDR_DQB10:L3:703:4 | 4.875 | 4.7734 | False | 3 | 0.13 | 0.39 | False | False | False
DDR_CAA4 | DDR_DQB10 | A_ADDRESS_COMMAND | B_BYTE1 | L3 | all_inner_layer_traces | track:DDR_CAA4:L3:702:0 | track:DDR_DQB10:L3:703:4 | 4.875 | 4.7734 | False | 3 | 0.13 | 0.39 | False | False | False
DDR_CAA4 | DDR_DQB12 | A_ADDRESS_COMMAND | B_BYTE1 | L3 | actual_interconnect_only | track:DDR_CAA4:L3:702:0 | track:DDR_DQB12:L3:691:3 | 4.2257811778 | 4.1241811778 | False | 3 | 0.13 | 0.39 | False | False | False
DDR_CAA4 | DDR_DQB12 | A_ADDRESS_COMMAND | B_BYTE1 | L3 | all_inner_layer_traces | track:DDR_CAA4:L3:702:0 | track:DDR_DQB12:L3:691:3 | 4.2257811778 | 4.1241811778 | False | 3 | 0.13 | 0.39 | False | False | False
DDR_CAA4 | DDR_DQB13 | A_ADDRESS_COMMAND | B_BYTE1 | L3 | actual_interconnect_only | track:DDR_CAA4:L3:702:0 | track:DDR_DQB13:L3:673:0 | 5.2906166937 | 5.1890166937 | False | 3 | 0.13 | 0.39 | False | False | False
DDR_CAA4 | DDR_DQB13 | A_ADDRESS_COMMAND | B_BYTE1 | L3 | all_inner_layer_traces | track:DDR_CAA4:L3:702:0 | track:DDR_DQB13:L3:673:0 | 5.2906166937 | 5.1890166937 | False | 3 | 0.13 | 0.39 | False | False | False
DDR_CAA4 | DDR_DQB14 | A_ADDRESS_COMMAND | B_BYTE1 | L3 | actual_interconnect_only | track:DDR_CAA4:L3:702:0 | track:DDR_DQB14:L3:681:0 | 5.8590208226 | 5.7574208226 | False | 3 | 0.13 | 0.39 | False | False | False
DDR_CAA4 | DDR_DQB14 | A_ADDRESS_COMMAND | B_BYTE1 | L3 | all_inner_layer_traces | track:DDR_CAA4:L3:702:0 | track:DDR_DQB14:L3:681:0 | 5.8590208226 | 5.7574208226 | False | 3 | 0.13 | 0.39 | False | False | False
DDR_CAA4 | DDR_DQB15 | A_ADDRESS_COMMAND | B_BYTE1 | L3 | actual_interconnect_only | track:DDR_CAA4:L3:702:0 | track:DDR_DQB15:L3:692:0 | 6.5081199282 | 6.4065199282 | False | 3 | 0.13 | 0.39 | False | False | False
DDR_CAA4 | DDR_DQB15 | A_ADDRESS_COMMAND | B_BYTE1 | L3 | all_inner_layer_traces | track:DDR_CAA4:L3:702:0 | track:DDR_DQB15:L3:692:0 | 6.5081199282 | 6.4065199282 | False | 3 | 0.13 | 0.39 | False | False | False
DDR_CAA4 | DDR_DQB2 | A_ADDRESS_COMMAND | B_BYTE0 | L3 | actual_interconnect_only | track:DDR_CAA4:L3:702:0 | track:DDR_DQB2:L3:655:0 | 6.4017575712 | 6.3001575712 | False | 3 | 0.13 | 0.39 | False | False | False
DDR_CAA4 | DDR_DQB2 | A_ADDRESS_COMMAND | B_BYTE0 | L3 | all_inner_layer_traces | track:DDR_CAA4:L3:702:0 | track:DDR_DQB2:L3:655:0 | 6.4017575712 | 6.3001575712 | False | 3 | 0.13 | 0.39 | False | False | False
DDR_CAA4 | DDR_DQB4 | A_ADDRESS_COMMAND | B_BYTE0 | L3 | actual_interconnect_only | track:DDR_CAA4:L3:702:0 | track:DDR_DQB4:L3:663:0 | 5.8137767415 | 5.7121767415 | False | 3 | 0.13 | 0.39 | False | False | False
DDR_CAA4 | DDR_DQB4 | A_ADDRESS_COMMAND | B_BYTE0 | L3 | all_inner_layer_traces | track:DDR_CAA4:L3:702:0 | track:DDR_DQB4:L3:663:0 | 5.8137767415 | 5.7121767415 | False | 3 | 0.13 | 0.39 | False | False | False
DDR_CAA4 | DDR_DQB8 | A_ADDRESS_COMMAND | B_BYTE1 | L3 | actual_interconnect_only | track:DDR_CAA4:L3:702:0 | track:DDR_DQB8:L3:706:0 | 5.85 | 5.7484 | False | 3 | 0.13 | 0.39 | False | False | False
DDR_CAA4 | DDR_DQB8 | A_ADDRESS_COMMAND | B_BYTE1 | L3 | all_inner_layer_traces | track:DDR_CAA4:L3:702:0 | track:DDR_DQB8:L3:706:0 | 5.85 | 5.7484 | False | 3 | 0.13 | 0.39 | False | False | False
DDR_CAA4 | DDR_DQB9 | A_ADDRESS_COMMAND | B_BYTE1 | L3 | actual_interconnect_only | track:DDR_CAA4:L3:702:0 | track:DDR_DQB9:L3:704:4 | 5.525 | 5.4234 | False | 3 | 0.13 | 0.39 | False | False | False
DDR_CAA4 | DDR_DQB9 | A_ADDRESS_COMMAND | B_BYTE1 | L3 | all_inner_layer_traces | track:DDR_CAA4:L3:702:0 | track:DDR_DQB9:L3:704:4 | 5.525 | 5.4234 | False | 3 | 0.13 | 0.39 | False | False | False
DDR_CAA4 | DDR_DQSA0_N | A_ADDRESS_COMMAND | A_BYTE0 | L3 | actual_interconnect_only | track:DDR_CAA4:L3:702:9 | track:DDR_DQSA0_N:L3:657:0 | 3.2347297511 | 3.1331297511 | False | 3 | 0.13 | 0.39 | False | False | False
DDR_CAA4 | DDR_DQSA0_N | A_ADDRESS_COMMAND | A_BYTE0 | L3 | all_inner_layer_traces | track:DDR_CAA4:L3:702:9 | track:DDR_DQSA0_N:L3:657:0 | 3.2347297511 | 3.1331297511 | False | 3 | 0.13 | 0.39 | False | False | False
DDR_CAA4 | DDR_DQSA0_P | A_ADDRESS_COMMAND | A_BYTE0 | L3 | actual_interconnect_only | track:DDR_CAA4:L3:702:7 | track:DDR_DQSA0_P:L3:652:1 | 2.8157550608 | 2.7141550608 | False | 3 | 0.13 | 0.39 | False | False | False
DDR_CAA4 | DDR_DQSA0_P | A_ADDRESS_COMMAND | A_BYTE0 | L3 | all_inner_layer_traces | track:DDR_CAA4:L3:702:7 | track:DDR_DQSA0_P:L3:652:1 | 2.8157550608 | 2.7141550608 | False | 3 | 0.13 | 0.39 | False | False | False
DDR_CAA4 | DDR_DQSB0_N | A_ADDRESS_COMMAND | B_BYTE0 | L3 | actual_interconnect_only | track:DDR_CAA4:L3:702:0 | track:DDR_DQSB0_N:L3:650:0 | 7.3507679233 | 7.2491679233 | False | 3 | 0.13 | 0.39 | False | False | False
DDR_CAA4 | DDR_DQSB0_N | A_ADDRESS_COMMAND | B_BYTE0 | L3 | all_inner_layer_traces | track:DDR_CAA4:L3:702:0 | track:DDR_DQSB0_N:L3:650:0 | 7.3507679233 | 7.2491679233 | False | 3 | 0.13 | 0.39 | False | False | False
DDR_CAA4 | DDR_DQSB0_P | A_ADDRESS_COMMAND | B_BYTE0 | L3 | actual_interconnect_only | track:DDR_CAA4:L3:702:0 | track:DDR_DQSB0_P:L3:651:0 | 6.7861992308 | 6.6845992308 | False | 3 | 0.13 | 0.39 | False | False | False
DDR_CAA4 | DDR_DQSB0_P | A_ADDRESS_COMMAND | B_BYTE0 | L3 | all_inner_layer_traces | track:DDR_CAA4:L3:702:0 | track:DDR_DQSB0_P:L3:651:0 | 6.7861992308 | 6.6845992308 | False | 3 | 0.13 | 0.39 | False | False | False
DDR_CAA4 | DDR_DQSB1_N | A_ADDRESS_COMMAND | B_BYTE1 | L3 | actual_interconnect_only | track:DDR_CAA4:L3:702:11 | track:DDR_DQSB1_N:L3:697:37 | 5.6920208681 | 5.5904208681 | False | 3 | 0.13 | 0.39 | False | False | False
DDR_CAA4 | DDR_DQSB1_N | A_ADDRESS_COMMAND | B_BYTE1 | L3 | all_inner_layer_traces | track:DDR_CAA4:L3:702:11 | track:DDR_DQSB1_N:L3:697:37 | 5.6920208681 | 5.5904208681 | False | 3 | 0.13 | 0.39 | False | False | False
DDR_CAA4 | DDR_DQSB1_P | A_ADDRESS_COMMAND | B_BYTE1 | L3 | actual_interconnect_only | track:DDR_CAA4:L3:702:0 | track:DDR_DQSB1_P:L3:690:0 | 6.5 | 6.3984 | False | 3 | 0.13 | 0.39 | False | False | False
DDR_CAA4 | DDR_DQSB1_P | A_ADDRESS_COMMAND | B_BYTE1 | L3 | all_inner_layer_traces | track:DDR_CAA4:L3:702:0 | track:DDR_DQSB1_P:L3:690:0 | 6.5 | 6.3984 | False | 3 | 0.13 | 0.39 | False | False | False
DDR_CAA5 | DDR_CAB2 | A_ADDRESS_COMMAND | B_ADDRESS_COMMAND | L3 | actual_interconnect_only | track:DDR_CAA5:L3:699:4 | track:DDR_CAB2:L3:696:11 | 3.9 | 3.7984 | False | 3 | 0.13 | 0.39 | False | False | False
DDR_CAA5 | DDR_CAB2 | A_ADDRESS_COMMAND | B_ADDRESS_COMMAND | L3 | all_inner_layer_traces | track:DDR_CAA5:L3:699:4 | track:DDR_CAB2:L3:696:11 | 3.9 | 3.7984 | False | 3 | 0.13 | 0.39 | False | False | False
DDR_CAA5 | DDR_CLKA_N | A_ADDRESS_COMMAND | A_ADDRESS_COMMAND | L3 | actual_interconnect_only | track:DDR_CAA5:L3:699:5 | track:DDR_CLKA_N:L3:680:2 | 0.325 | 0.2234 | False | 3 | 0.13 | 0.39 | True | True | False
DDR_CAA5 | DDR_CLKA_N | A_ADDRESS_COMMAND | A_ADDRESS_COMMAND | L3 | all_inner_layer_traces | track:DDR_CAA5:L3:699:5 | track:DDR_CLKA_N:L3:680:2 | 0.325 | 0.2234 | False | 3 | 0.13 | 0.39 | True | True | False
DDR_CAA5 | DDR_CLKA_P | A_ADDRESS_COMMAND | A_ADDRESS_COMMAND | L3 | actual_interconnect_only | track:DDR_CAA5:L3:699:0 | track:DDR_CLKA_P:L3:676:0 | 0.65 | 0.5484 | False | 3 | 0.13 | 0.39 | False | False | False
DDR_CAA5 | DDR_CLKA_P | A_ADDRESS_COMMAND | A_ADDRESS_COMMAND | L3 | all_inner_layer_traces | track:DDR_CAA5:L3:699:0 | track:DDR_CLKA_P:L3:676:0 | 0.65 | 0.5484 | False | 3 | 0.13 | 0.39 | False | False | False
DDR_CAA5 | DDR_CLKB_N | A_ADDRESS_COMMAND | B_ADDRESS_COMMAND | L3 | actual_interconnect_only | track:DDR_CAA5:L3:699:4 | track:DDR_CLKB_N:L3:701:13 | 3.3340103479 | 3.2324103479 | False | 3 | 0.13 | 0.39 | False | False | False
DDR_CAA5 | DDR_CLKB_N | A_ADDRESS_COMMAND | B_ADDRESS_COMMAND | L3 | all_inner_layer_traces | track:DDR_CAA5:L3:699:4 | track:DDR_CLKB_N:L3:701:13 | 3.3340103479 | 3.2324103479 | False | 3 | 0.13 | 0.39 | False | False | False
DDR_CAA5 | DDR_CLKB_P | A_ADDRESS_COMMAND | B_ADDRESS_COMMAND | L3 | actual_interconnect_only | track:DDR_CAA5:L3:699:3 | track:DDR_CLKB_P:L3:700:11 | 2.6 | 2.4984 | False | 3 | 0.13 | 0.39 | False | False | False
DDR_CAA5 | DDR_CLKB_P | A_ADDRESS_COMMAND | B_ADDRESS_COMMAND | L3 | all_inner_layer_traces | track:DDR_CAA5:L3:699:3 | track:DDR_CLKB_P:L3:700:11 | 2.6 | 2.4984 | False | 3 | 0.13 | 0.39 | False | False | False
DDR_CAA5 | DDR_CSA0 | A_ADDRESS_COMMAND | A_ADDRESS_COMMAND | L3 | actual_interconnect_only | track:DDR_CAA5:L3:699:0 | track:DDR_CSA0:L3:679:0 | 1.3400093283 | 1.2384093283 | False | 3 | 0.13 | 0.39 | False | False | False
DDR_CAA5 | DDR_CSA0 | A_ADDRESS_COMMAND | A_ADDRESS_COMMAND | L3 | all_inner_layer_traces | track:DDR_CAA5:L3:699:0 | track:DDR_CSA0:L3:679:0 | 1.3400093283 | 1.2384093283 | False | 3 | 0.13 | 0.39 | False | False | False
DDR_CAA5 | DDR_DMIA0 | A_ADDRESS_COMMAND | A_BYTE0 | L3 | actual_interconnect_only | track:DDR_CAA5:L3:699:0 | track:DDR_DMIA0:L3:661:0 | 2.9068883707 | 2.8052883707 | False | 3 | 0.13 | 0.39 | False | False | False
DDR_CAA5 | DDR_DMIA0 | A_ADDRESS_COMMAND | A_BYTE0 | L3 | all_inner_layer_traces | track:DDR_CAA5:L3:699:0 | track:DDR_DMIA0:L3:661:0 | 2.9068883707 | 2.8052883707 | False | 3 | 0.13 | 0.39 | False | False | False
DDR_CAA5 | DDR_DQA0 | A_ADDRESS_COMMAND | A_BYTE0 | L3 | actual_interconnect_only | track:DDR_CAA5:L3:699:0 | track:DDR_DQA0:L3:648:0 | 4.3603325561 | 4.2587325561 | False | 3 | 0.13 | 0.39 | False | False | False
DDR_CAA5 | DDR_DQA0 | A_ADDRESS_COMMAND | A_BYTE0 | L3 | all_inner_layer_traces | track:DDR_CAA5:L3:699:0 | track:DDR_DQA0:L3:648:0 | 4.3603325561 | 4.2587325561 | False | 3 | 0.13 | 0.39 | False | False | False
DDR_CAA5 | DDR_DQA1 | A_ADDRESS_COMMAND | A_BYTE0 | L3 | actual_interconnect_only | track:DDR_CAA5:L3:699:0 | track:DDR_DQA1:L3:658:8 | 1.625 | 1.5234 | False | 3 | 0.13 | 0.39 | False | False | False
DDR_CAA5 | DDR_DQA1 | A_ADDRESS_COMMAND | A_BYTE0 | L3 | all_inner_layer_traces | track:DDR_CAA5:L3:699:0 | track:DDR_DQA1:L3:658:8 | 1.625 | 1.5234 | False | 3 | 0.13 | 0.39 | False | False | False
DDR_CAA5 | DDR_DQA2 | A_ADDRESS_COMMAND | A_BYTE0 | L3 | actual_interconnect_only | track:DDR_CAA5:L3:699:0 | track:DDR_DQA2:L3:668:1 | 2.2980970389 | 2.1964970389 | False | 3 | 0.13 | 0.39 | False | False | False
DDR_CAA5 | DDR_DQA2 | A_ADDRESS_COMMAND | A_BYTE0 | L3 | all_inner_layer_traces | track:DDR_CAA5:L3:699:0 | track:DDR_DQA2:L3:668:1 | 2.2980970389 | 2.1964970389 | False | 3 | 0.13 | 0.39 | False | False | False
DDR_CAA5 | DDR_DQA4 | A_ADDRESS_COMMAND | A_BYTE0 | L3 | actual_interconnect_only | track:DDR_CAA5:L3:699:0 | track:DDR_DQA4:L3:659:0 | 2.7577164466 | 2.6561164466 | False | 3 | 0.13 | 0.39 | False | False | False
DDR_CAA5 | DDR_DQA4 | A_ADDRESS_COMMAND | A_BYTE0 | L3 | all_inner_layer_traces | track:DDR_CAA5:L3:699:0 | track:DDR_DQA4:L3:659:0 | 2.7577164466 | 2.6561164466 | False | 3 | 0.13 | 0.39 | False | False | False
DDR_CAA5 | DDR_DQA5 | A_ADDRESS_COMMAND | A_BYTE0 | L3 | actual_interconnect_only | track:DDR_CAA5:L3:699:0 | track:DDR_DQA5:L3:667:4 | 2.275 | 2.1734 | False | 3 | 0.13 | 0.39 | False | False | False
DDR_CAA5 | DDR_DQA5 | A_ADDRESS_COMMAND | A_BYTE0 | L3 | all_inner_layer_traces | track:DDR_CAA5:L3:699:0 | track:DDR_DQA5:L3:667:4 | 2.275 | 2.1734 | False | 3 | 0.13 | 0.39 | False | False | False
DDR_CAA5 | DDR_DQA6 | A_ADDRESS_COMMAND | A_BYTE0 | L3 | actual_interconnect_only | track:DDR_CAA5:L3:699:0 | track:DDR_DQA6:L3:674:4 | 2.925 | 2.8234 | False | 3 | 0.13 | 0.39 | False | False | False
DDR_CAA5 | DDR_DQA6 | A_ADDRESS_COMMAND | A_BYTE0 | L3 | all_inner_layer_traces | track:DDR_CAA5:L3:699:0 | track:DDR_DQA6:L3:674:4 | 2.925 | 2.8234 | False | 3 | 0.13 | 0.39 | False | False | False
DDR_CAA5 | DDR_DQA8 | A_ADDRESS_COMMAND | A_BYTE1 | L3 | actual_interconnect_only | track:DDR_CAA5:L3:699:0 | track:DDR_DQA8:L3:708:0 | 3.25 | 3.1484 | False | 3 | 0.13 | 0.39 | False | False | False
DDR_CAA5 | DDR_DQA8 | A_ADDRESS_COMMAND | A_BYTE1 | L3 | all_inner_layer_traces | track:DDR_CAA5:L3:699:0 | track:DDR_DQA8:L3:708:0 | 3.25 | 3.1484 | False | 3 | 0.13 | 0.39 | False | False | False
DDR_CAA5 | DDR_DQB10 | A_ADDRESS_COMMAND | B_BYTE1 | L3 | actual_interconnect_only | track:DDR_CAA5:L3:699:4 | track:DDR_DQB10:L3:703:5 | 5.525 | 5.4234 | False | 3 | 0.13 | 0.39 | False | False | False
DDR_CAA5 | DDR_DQB10 | A_ADDRESS_COMMAND | B_BYTE1 | L3 | all_inner_layer_traces | track:DDR_CAA5:L3:699:4 | track:DDR_DQB10:L3:703:5 | 5.525 | 5.4234 | False | 3 | 0.13 | 0.39 | False | False | False
DDR_CAA5 | DDR_DQB12 | A_ADDRESS_COMMAND | B_BYTE1 | L3 | actual_interconnect_only | track:DDR_CAA5:L3:699:4 | track:DDR_DQB12:L3:691:7 | 5.1308503194 | 5.0292503194 | False | 3 | 0.13 | 0.39 | False | False | False
DDR_CAA5 | DDR_DQB12 | A_ADDRESS_COMMAND | B_BYTE1 | L3 | all_inner_layer_traces | track:DDR_CAA5:L3:699:4 | track:DDR_DQB12:L3:691:7 | 5.1308503194 | 5.0292503194 | False | 3 | 0.13 | 0.39 | False | False | False
DDR_CAA5 | DDR_DQB13 | A_ADDRESS_COMMAND | B_BYTE1 | L3 | actual_interconnect_only | track:DDR_CAA5:L3:699:4 | track:DDR_DQB13:L3:673:31 | 5.7520105181 | 5.6504105181 | False | 3 | 0.13 | 0.39 | False | False | False
DDR_CAA5 | DDR_DQB13 | A_ADDRESS_COMMAND | B_BYTE1 | L3 | all_inner_layer_traces | track:DDR_CAA5:L3:699:4 | track:DDR_DQB13:L3:673:31 | 5.7520105181 | 5.6504105181 | False | 3 | 0.13 | 0.39 | False | False | False
DDR_CAA5 | DDR_DQB14 | A_ADDRESS_COMMAND | B_BYTE1 | L3 | actual_interconnect_only | track:DDR_CAA5:L3:699:3 | track:DDR_DQB14:L3:681:0 | 6.825 | 6.7234 | False | 3 | 0.13 | 0.39 | False | False | False
DDR_CAA5 | DDR_DQB14 | A_ADDRESS_COMMAND | B_BYTE1 | L3 | all_inner_layer_traces | track:DDR_CAA5:L3:699:3 | track:DDR_DQB14:L3:681:0 | 6.825 | 6.7234 | False | 3 | 0.13 | 0.39 | False | False | False
DDR_CAA5 | DDR_DQB15 | A_ADDRESS_COMMAND | B_BYTE1 | L3 | actual_interconnect_only | track:DDR_CAA5:L3:699:3 | track:DDR_DQB15:L3:692:0 | 7.4789731289 | 7.3773731289 | False | 3 | 0.13 | 0.39 | False | False | False
DDR_CAA5 | DDR_DQB15 | A_ADDRESS_COMMAND | B_BYTE1 | L3 | all_inner_layer_traces | track:DDR_CAA5:L3:699:3 | track:DDR_DQB15:L3:692:0 | 7.4789731289 | 7.3773731289 | False | 3 | 0.13 | 0.39 | False | False | False
DDR_CAA5 | DDR_DQB2 | A_ADDRESS_COMMAND | B_BYTE0 | L3 | actual_interconnect_only | track:DDR_CAA5:L3:699:4 | track:DDR_DQB2:L3:655:87 | 5.9756602669 | 5.8740602669 | False | 3 | 0.13 | 0.39 | False | False | False
DDR_CAA5 | DDR_DQB2 | A_ADDRESS_COMMAND | B_BYTE0 | L3 | all_inner_layer_traces | track:DDR_CAA5:L3:699:4 | track:DDR_DQB2:L3:655:87 | 5.9756602669 | 5.8740602669 | False | 3 | 0.13 | 0.39 | False | False | False
DDR_CAA5 | DDR_DQB4 | A_ADDRESS_COMMAND | B_BYTE0 | L3 | actual_interconnect_only | track:DDR_CAA5:L3:699:4 | track:DDR_DQB4:L3:663:103 | 5.5637568805 | 5.4621568805 | False | 3 | 0.13 | 0.39 | False | False | False
DDR_CAA5 | DDR_DQB4 | A_ADDRESS_COMMAND | B_BYTE0 | L3 | all_inner_layer_traces | track:DDR_CAA5:L3:699:4 | track:DDR_DQB4:L3:663:103 | 5.5637568805 | 5.4621568805 | False | 3 | 0.13 | 0.39 | False | False | False
DDR_CAA5 | DDR_DQB8 | A_ADDRESS_COMMAND | B_BYTE1 | L3 | actual_interconnect_only | track:DDR_CAA5:L3:699:3 | track:DDR_DQB8:L3:706:0 | 6.8640623222 | 6.7624623222 | False | 3 | 0.13 | 0.39 | False | False | False
DDR_CAA5 | DDR_DQB8 | A_ADDRESS_COMMAND | B_BYTE1 | L3 | all_inner_layer_traces | track:DDR_CAA5:L3:699:3 | track:DDR_DQB8:L3:706:0 | 6.8640623222 | 6.7624623222 | False | 3 | 0.13 | 0.39 | False | False | False
DDR_CAA5 | DDR_DQB9 | A_ADDRESS_COMMAND | B_BYTE1 | L3 | actual_interconnect_only | track:DDR_CAA5:L3:699:3 | track:DDR_DQB9:L3:704:4 | 6.5 | 6.3984 | False | 3 | 0.13 | 0.39 | False | False | False
DDR_CAA5 | DDR_DQB9 | A_ADDRESS_COMMAND | B_BYTE1 | L3 | all_inner_layer_traces | track:DDR_CAA5:L3:699:3 | track:DDR_DQB9:L3:704:4 | 6.5 | 6.3984 | False | 3 | 0.13 | 0.39 | False | False | False
DDR_CAA5 | DDR_DQSA0_N | A_ADDRESS_COMMAND | A_BYTE0 | L3 | actual_interconnect_only | track:DDR_CAA5:L3:699:0 | track:DDR_DQSA0_N:L3:657:0 | 4.020027985 | 3.918427985 | False | 3 | 0.13 | 0.39 | False | False | False
DDR_CAA5 | DDR_DQSA0_N | A_ADDRESS_COMMAND | A_BYTE0 | L3 | all_inner_layer_traces | track:DDR_CAA5:L3:699:0 | track:DDR_DQSA0_N:L3:657:0 | 4.020027985 | 3.918427985 | False | 3 | 0.13 | 0.39 | False | False | False
DDR_CAA5 | DDR_DQSA0_P | A_ADDRESS_COMMAND | A_BYTE0 | L3 | actual_interconnect_only | track:DDR_CAA5:L3:699:0 | track:DDR_DQSA0_P:L3:652:1 | 3.3460797958 | 3.2444797958 | False | 3 | 0.13 | 0.39 | False | False | False
DDR_CAA5 | DDR_DQSA0_P | A_ADDRESS_COMMAND | A_BYTE0 | L3 | all_inner_layer_traces | track:DDR_CAA5:L3:699:0 | track:DDR_DQSA0_P:L3:652:1 | 3.3460797958 | 3.2444797958 | False | 3 | 0.13 | 0.39 | False | False | False
DDR_CAA5 | DDR_DQSB0_N | A_ADDRESS_COMMAND | B_BYTE0 | L3 | actual_interconnect_only | track:DDR_CAA5:L3:699:4 | track:DDR_DQSB0_N:L3:650:46 | 7.0148558877 | 6.9132558877 | False | 3 | 0.13 | 0.39 | False | False | False
DDR_CAA5 | DDR_DQSB0_N | A_ADDRESS_COMMAND | B_BYTE0 | L3 | all_inner_layer_traces | track:DDR_CAA5:L3:699:4 | track:DDR_DQSB0_N:L3:650:46 | 7.0148558877 | 6.9132558877 | False | 3 | 0.13 | 0.39 | False | False | False
DDR_CAA5 | DDR_DQSB0_P | A_ADDRESS_COMMAND | B_BYTE0 | L3 | actual_interconnect_only | track:DDR_CAA5:L3:699:4 | track:DDR_DQSB0_P:L3:651:77 | 6.425838953 | 6.324238953 | False | 3 | 0.13 | 0.39 | False | False | False
DDR_CAA5 | DDR_DQSB0_P | A_ADDRESS_COMMAND | B_BYTE0 | L3 | all_inner_layer_traces | track:DDR_CAA5:L3:699:4 | track:DDR_DQSB0_P:L3:651:77 | 6.425838953 | 6.324238953 | False | 3 | 0.13 | 0.39 | False | False | False
DDR_CAA5 | DDR_DQSB1_N | A_ADDRESS_COMMAND | B_BYTE1 | L3 | actual_interconnect_only | track:DDR_CAA5:L3:699:4 | track:DDR_DQSB1_N:L3:697:37 | 4.7514183738 | 4.6498183738 | False | 3 | 0.13 | 0.39 | False | False | False
DDR_CAA5 | DDR_DQSB1_N | A_ADDRESS_COMMAND | B_BYTE1 | L3 | all_inner_layer_traces | track:DDR_CAA5:L3:699:4 | track:DDR_DQSB1_N:L3:697:37 | 4.7514183738 | 4.6498183738 | False | 3 | 0.13 | 0.39 | False | False | False
DDR_CAA5 | DDR_DQSB1_P | A_ADDRESS_COMMAND | B_BYTE1 | L3 | actual_interconnect_only | track:DDR_CAA5:L3:699:4 | track:DDR_DQSB1_P:L3:690:14 | 6.2266062185 | 6.1250062185 | False | 3 | 0.13 | 0.39 | False | False | False
DDR_CAA5 | DDR_DQSB1_P | A_ADDRESS_COMMAND | B_BYTE1 | L3 | all_inner_layer_traces | track:DDR_CAA5:L3:699:4 | track:DDR_DQSB1_P:L3:690:14 | 6.2266062185 | 6.1250062185 | False | 3 | 0.13 | 0.39 | False | False | False
DDR_CAB0 | DDR_CAB1 | B_ADDRESS_COMMAND | B_ADDRESS_COMMAND | L8 | actual_interconnect_only | track:DDR_CAB0:L8:671:21 | track:DDR_CAB1:L8:666:34 | 0.65 | 0.5484 | False | 3 | 0.1195 | 0.3585 | False | False | False
DDR_CAB0 | DDR_CAB1 | B_ADDRESS_COMMAND | B_ADDRESS_COMMAND | L8 | all_inner_layer_traces | track:DDR_CAB0:L8:671:21 | track:DDR_CAB1:L8:666:34 | 0.65 | 0.5484 | False | 3 | 0.1195 | 0.3585 | False | False | False
DDR_CAB0 | DDR_CAB3 | B_ADDRESS_COMMAND | B_ADDRESS_COMMAND | L8 | actual_interconnect_only | track:DDR_CAB0:L8:671:4 | track:DDR_CAB3:L8:695:27 | 1.625 | 1.5234 | False | 3 | 0.1195 | 0.3585 | False | False | False
DDR_CAB0 | DDR_CAB3 | B_ADDRESS_COMMAND | B_ADDRESS_COMMAND | L8 | all_inner_layer_traces | track:DDR_CAB0:L8:671:4 | track:DDR_CAB3:L8:695:27 | 1.625 | 1.5234 | False | 3 | 0.1195 | 0.3585 | False | False | False
DDR_CAB0 | DDR_CAB4 | B_ADDRESS_COMMAND | B_ADDRESS_COMMAND | L8 | actual_interconnect_only | track:DDR_CAB0:L8:671:3 | track:DDR_CAB4:L8:682:8 | 0.2088846871 | 0.1072846871 | False | 3 | 0.1195 | 0.3585 | True | True | True
DDR_CAB0 | DDR_CAB4 | B_ADDRESS_COMMAND | B_ADDRESS_COMMAND | L8 | all_inner_layer_traces | track:DDR_CAB0:L8:671:3 | track:DDR_CAB4:L8:682:8 | 0.2088846871 | 0.1072846871 | False | 3 | 0.1195 | 0.3585 | True | True | True
DDR_CAB0 | DDR_CAB5 | B_ADDRESS_COMMAND | B_ADDRESS_COMMAND | L8 | actual_interconnect_only | track:DDR_CAB0:L8:671:3 | track:DDR_CAB5:L8:707:4 | 0.7267220927 | 0.6251220927 | False | 3 | 0.1195 | 0.3585 | False | False | False
DDR_CAB0 | DDR_CAB5 | B_ADDRESS_COMMAND | B_ADDRESS_COMMAND | L8 | all_inner_layer_traces | track:DDR_CAB0:L8:671:3 | track:DDR_CAB5:L8:707:4 | 0.7267220927 | 0.6251220927 | False | 3 | 0.1195 | 0.3585 | False | False | False
DDR_CAB0 | DDR_CKEA0 | B_ADDRESS_COMMAND | A_ADDRESS_COMMAND | L8 | actual_interconnect_only | track:DDR_CAB0:L8:671:21 | track:DDR_CKEA0:L8:670:85 | 4.0804411526 | 3.9788411526 | False | 3 | 0.1195 | 0.3585 | False | False | False
DDR_CAB0 | DDR_CKEA0 | B_ADDRESS_COMMAND | A_ADDRESS_COMMAND | L8 | all_inner_layer_traces | track:DDR_CAB0:L8:671:21 | track:DDR_CKEA0:L8:670:85 | 4.0804411526 | 3.9788411526 | False | 3 | 0.1195 | 0.3585 | False | False | False
DDR_CAB0 | DDR_CKEB0 | B_ADDRESS_COMMAND | B_ADDRESS_COMMAND | L8 | actual_interconnect_only | track:DDR_CAB0:L8:671:13 | track:DDR_CKEB0:L8:672:24 | 1.7196020615 | 1.6180020615 | False | 3 | 0.1195 | 0.3585 | False | False | False
DDR_CAB0 | DDR_CKEB0 | B_ADDRESS_COMMAND | B_ADDRESS_COMMAND | L8 | all_inner_layer_traces | track:DDR_CAB0:L8:671:13 | track:DDR_CKEB0:L8:672:24 | 1.7196020615 | 1.6180020615 | False | 3 | 0.1195 | 0.3585 | False | False | False
DDR_CAB0 | DDR_CSB0 | B_ADDRESS_COMMAND | B_ADDRESS_COMMAND | L8 | actual_interconnect_only | track:DDR_CAB0:L8:671:13 | track:DDR_CSB0:L8:677:23 | 1.1256248265 | 1.0240248265 | False | 3 | 0.1195 | 0.3585 | False | False | False
DDR_CAB0 | DDR_CSB0 | B_ADDRESS_COMMAND | B_ADDRESS_COMMAND | L8 | all_inner_layer_traces | track:DDR_CAB0:L8:671:13 | track:DDR_CSB0:L8:677:23 | 1.1256248265 | 1.0240248265 | False | 3 | 0.1195 | 0.3585 | False | False | False
DDR_CAB0 | DDR_DMIA1 | B_ADDRESS_COMMAND | A_BYTE1 | L8 | actual_interconnect_only | track:DDR_CAB0:L8:671:0 | track:DDR_DMIA1:L8:675:0 | 6.1664414373 | 6.0648414373 | False | 3 | 0.1195 | 0.3585 | False | False | False
DDR_CAB0 | DDR_DMIA1 | B_ADDRESS_COMMAND | A_BYTE1 | L8 | all_inner_layer_traces | track:DDR_CAB0:L8:671:0 | track:DDR_DMIA1:L8:675:0 | 6.1664414373 | 6.0648414373 | False | 3 | 0.1195 | 0.3585 | False | False | False
DDR_CAB0 | DDR_DMIB0 | B_ADDRESS_COMMAND | B_BYTE0 | L8 | actual_interconnect_only | track:DDR_CAB0:L8:671:0 | track:DDR_DMIB0:L8:654:8 | 0.325 | 0.2234 | False | 3 | 0.1195 | 0.3585 | True | True | False
DDR_CAB0 | DDR_DMIB0 | B_ADDRESS_COMMAND | B_BYTE0 | L8 | all_inner_layer_traces | track:DDR_CAB0:L8:671:0 | track:DDR_DMIB0:L8:654:8 | 0.325 | 0.2234 | False | 3 | 0.1195 | 0.3585 | True | True | False
DDR_CAB0 | DDR_DMIB1 | B_ADDRESS_COMMAND | B_BYTE1 | L8 | actual_interconnect_only | track:DDR_CAB0:L8:671:0 | track:DDR_DMIB1:L8:684:0 | 0.65 | 0.5484 | False | 3 | 0.1195 | 0.3585 | False | False | False
DDR_CAB0 | DDR_DMIB1 | B_ADDRESS_COMMAND | B_BYTE1 | L8 | all_inner_layer_traces | track:DDR_CAB0:L8:671:0 | track:DDR_DMIB1:L8:684:0 | 0.65 | 0.5484 | False | 3 | 0.1195 | 0.3585 | False | False | False
DDR_CAB0 | DDR_DQA10 | B_ADDRESS_COMMAND | A_BYTE1 | L8 | actual_interconnect_only | track:DDR_CAB0:L8:671:3 | track:DDR_DQA10:L8:678:8 | 5.2906166937 | 5.1890166937 | False | 3 | 0.1195 | 0.3585 | False | False | False
DDR_CAB0 | DDR_DQA10 | B_ADDRESS_COMMAND | A_BYTE1 | L8 | all_inner_layer_traces | track:DDR_CAB0:L8:671:3 | track:DDR_DQA10:L8:678:8 | 5.2906166937 | 5.1890166937 | False | 3 | 0.1195 | 0.3585 | False | False | False
DDR_CAB0 | DDR_DQA11 | B_ADDRESS_COMMAND | A_BYTE1 | L8 | actual_interconnect_only | track:DDR_CAB0:L8:671:3 | track:DDR_DQA11:L8:705:10 | 6.0108528149 | 5.9092528149 | False | 3 | 0.1195 | 0.3585 | False | False | False
DDR_CAB0 | DDR_DQA11 | B_ADDRESS_COMMAND | A_BYTE1 | L8 | all_inner_layer_traces | track:DDR_CAB0:L8:671:3 | track:DDR_DQA11:L8:705:10 | 6.0108528149 | 5.9092528149 | False | 3 | 0.1195 | 0.3585 | False | False | False
DDR_CAB0 | DDR_DQA12 | B_ADDRESS_COMMAND | A_BYTE1 | L8 | actual_interconnect_only | track:DDR_CAB0:L8:671:3 | track:DDR_DQA12:L8:688:10 | 4.55 | 4.4484 | False | 3 | 0.1195 | 0.3585 | False | False | False
DDR_CAB0 | DDR_DQA12 | B_ADDRESS_COMMAND | A_BYTE1 | L8 | all_inner_layer_traces | track:DDR_CAB0:L8:671:3 | track:DDR_DQA12:L8:688:10 | 4.55 | 4.4484 | False | 3 | 0.1195 | 0.3585 | False | False | False
DDR_CAB0 | DDR_DQA13 | B_ADDRESS_COMMAND | A_BYTE1 | L8 | actual_interconnect_only | track:DDR_CAB0:L8:671:3 | track:DDR_DQA13:L8:693:11 | 5.2 | 5.0984 | False | 3 | 0.1195 | 0.3585 | False | False | False
DDR_CAB0 | DDR_DQA13 | B_ADDRESS_COMMAND | A_BYTE1 | L8 | all_inner_layer_traces | track:DDR_CAB0:L8:671:3 | track:DDR_DQA13:L8:693:11 | 5.2 | 5.0984 | False | 3 | 0.1195 | 0.3585 | False | False | False
DDR_CAB0 | DDR_DQA14 | B_ADDRESS_COMMAND | A_BYTE1 | L8 | actual_interconnect_only | track:DDR_CAB0:L8:671:3 | track:DDR_DQA14:L8:683:4 | 7.15 | 7.0484 | False | 3 | 0.1195 | 0.3585 | False | False | False
DDR_CAB0 | DDR_DQA14 | B_ADDRESS_COMMAND | A_BYTE1 | L8 | all_inner_layer_traces | track:DDR_CAB0:L8:671:3 | track:DDR_DQA14:L8:683:4 | 7.15 | 7.0484 | False | 3 | 0.1195 | 0.3585 | False | False | False
DDR_CAB0 | DDR_DQA15 | B_ADDRESS_COMMAND | A_BYTE1 | L8 | actual_interconnect_only | track:DDR_CAB0:L8:671:3 | track:DDR_DQA15:L8:698:2 | 7.4382588899 | 7.3366588899 | False | 3 | 0.1195 | 0.3585 | False | False | False
DDR_CAB0 | DDR_DQA15 | B_ADDRESS_COMMAND | A_BYTE1 | L8 | all_inner_layer_traces | track:DDR_CAB0:L8:671:3 | track:DDR_DQA15:L8:698:2 | 7.4382588899 | 7.3366588899 | False | 3 | 0.1195 | 0.3585 | False | False | False
DDR_CAB0 | DDR_DQA3 | B_ADDRESS_COMMAND | A_BYTE0 | L8 | actual_interconnect_only | track:DDR_CAB0:L8:671:21 | track:DDR_DQA3:L8:649:49 | 5.85 | 5.7484 | False | 3 | 0.1195 | 0.3585 | False | False | False
DDR_CAB0 | DDR_DQA3 | B_ADDRESS_COMMAND | A_BYTE0 | L8 | all_inner_layer_traces | track:DDR_CAB0:L8:671:21 | track:DDR_DQA3:L8:649:49 | 5.85 | 5.7484 | False | 3 | 0.1195 | 0.3585 | False | False | False
DDR_CAB0 | DDR_DQA7 | B_ADDRESS_COMMAND | A_BYTE0 | L8 | actual_interconnect_only | track:DDR_CAB0:L8:671:21 | track:DDR_DQA7:L8:669:31 | 8.6001453476 | 8.4985453476 | False | 3 | 0.1195 | 0.3585 | False | False | False
DDR_CAB0 | DDR_DQA7 | B_ADDRESS_COMMAND | A_BYTE0 | L8 | all_inner_layer_traces | track:DDR_CAB0:L8:671:21 | track:DDR_DQA7:L8:669:31 | 8.6001453476 | 8.4985453476 | False | 3 | 0.1195 | 0.3585 | False | False | False
DDR_CAB0 | DDR_DQA9 | B_ADDRESS_COMMAND | A_BYTE1 | L8 | actual_interconnect_only | track:DDR_CAB0:L8:671:0 | track:DDR_DQA9:L8:686:0 | 7.3700513058 | 7.2684513058 | False | 3 | 0.1195 | 0.3585 | False | False | False
DDR_CAB0 | DDR_DQA9 | B_ADDRESS_COMMAND | A_BYTE1 | L8 | all_inner_layer_traces | track:DDR_CAB0:L8:671:0 | track:DDR_DQA9:L8:686:0 | 7.3700513058 | 7.2684513058 | False | 3 | 0.1195 | 0.3585 | False | False | False
DDR_CAB0 | DDR_DQB0 | B_ADDRESS_COMMAND | B_BYTE0 | L8 | actual_interconnect_only | track:DDR_CAB0:L8:671:4 | track:DDR_DQB0:L8:653:11 | 2.6517977393 | 2.5501977393 | False | 3 | 0.1195 | 0.3585 | False | False | False
DDR_CAB0 | DDR_DQB0 | B_ADDRESS_COMMAND | B_BYTE0 | L8 | all_inner_layer_traces | track:DDR_CAB0:L8:671:4 | track:DDR_DQB0:L8:653:11 | 2.6517977393 | 2.5501977393 | False | 3 | 0.1195 | 0.3585 | False | False | False
DDR_CAB0 | DDR_DQB1 | B_ADDRESS_COMMAND | B_BYTE0 | L8 | actual_interconnect_only | track:DDR_CAB0:L8:671:4 | track:DDR_DQB1:L8:662:17 | 2.120620487 | 2.019020487 | False | 3 | 0.1195 | 0.3585 | False | False | False
DDR_CAB0 | DDR_DQB1 | B_ADDRESS_COMMAND | B_BYTE0 | L8 | all_inner_layer_traces | track:DDR_CAB0:L8:671:4 | track:DDR_DQB1:L8:662:17 | 2.120620487 | 2.019020487 | False | 3 | 0.1195 | 0.3585 | False | False | False
DDR_CAB0 | DDR_DQB11 | B_ADDRESS_COMMAND | B_BYTE1 | L8 | actual_interconnect_only | track:DDR_CAB0:L8:671:9 | track:DDR_DQB11:L8:694:69 | 0.2298097039 | 0.1282097039 | False | 3 | 0.1195 | 0.3585 | True | True | True
DDR_CAB0 | DDR_DQB11 | B_ADDRESS_COMMAND | B_BYTE1 | L8 | all_inner_layer_traces | track:DDR_CAB0:L8:671:9 | track:DDR_DQB11:L8:694:69 | 0.2298097039 | 0.1282097039 | False | 3 | 0.1195 | 0.3585 | True | True | True
DDR_CAB0 | DDR_DQB3 | B_ADDRESS_COMMAND | B_BYTE0 | L8 | actual_interconnect_only | track:DDR_CAB0:L8:671:20 | track:DDR_DQB3:L8:646:28 | 0.56875 | 0.46715 | False | 3 | 0.1195 | 0.3585 | False | False | False
DDR_CAB0 | DDR_DQB3 | B_ADDRESS_COMMAND | B_BYTE0 | L8 | all_inner_layer_traces | track:DDR_CAB0:L8:671:20 | track:DDR_DQB3:L8:646:28 | 0.56875 | 0.46715 | False | 3 | 0.1195 | 0.3585 | False | False | False
DDR_CAB0 | DDR_DQB5 | B_ADDRESS_COMMAND | B_BYTE0 | L8 | actual_interconnect_only | track:DDR_CAB0:L8:671:6 | track:DDR_DQB5:L8:665:51 | 0.2298097039 | 0.1282097039 | False | 3 | 0.1195 | 0.3585 | True | True | True
DDR_CAB0 | DDR_DQB5 | B_ADDRESS_COMMAND | B_BYTE0 | L8 | all_inner_layer_traces | track:DDR_CAB0:L8:671:6 | track:DDR_DQB5:L8:665:51 | 0.2298097039 | 0.1282097039 | False | 3 | 0.1195 | 0.3585 | True | True | True
DDR_CAB0 | DDR_DQB6 | B_ADDRESS_COMMAND | B_BYTE0 | L8 | actual_interconnect_only | track:DDR_CAB0:L8:671:0 | track:DDR_DQB6:L8:664:4 | 1.625 | 1.5234 | False | 3 | 0.1195 | 0.3585 | False | False | False
DDR_CAB0 | DDR_DQB6 | B_ADDRESS_COMMAND | B_BYTE0 | L8 | all_inner_layer_traces | track:DDR_CAB0:L8:671:0 | track:DDR_DQB6:L8:664:4 | 1.625 | 1.5234 | False | 3 | 0.1195 | 0.3585 | False | False | False
DDR_CAB0 | DDR_DQB7 | B_ADDRESS_COMMAND | B_BYTE0 | L8 | actual_interconnect_only | track:DDR_CAB0:L8:671:0 | track:DDR_DQB7:L8:660:4 | 2.275 | 2.1734 | False | 3 | 0.1195 | 0.3585 | False | False | False
DDR_CAB0 | DDR_DQB7 | B_ADDRESS_COMMAND | B_BYTE0 | L8 | all_inner_layer_traces | track:DDR_CAB0:L8:671:0 | track:DDR_DQB7:L8:660:4 | 2.275 | 2.1734 | False | 3 | 0.1195 | 0.3585 | False | False | False
DDR_CAB0 | DDR_DQSA1_N | B_ADDRESS_COMMAND | A_BYTE1 | L8 | actual_interconnect_only | track:DDR_CAB0:L8:671:4 | track:DDR_DQSA1_N:L8:687:29 | 8.125 | 8.0234 | False | 3 | 0.1195 | 0.3585 | False | False | False
DDR_CAB0 | DDR_DQSA1_N | B_ADDRESS_COMMAND | A_BYTE1 | L8 | all_inner_layer_traces | track:DDR_CAB0:L8:671:4 | track:DDR_DQSA1_N:L8:687:29 | 8.125 | 8.0234 | False | 3 | 0.1195 | 0.3585 | False | False | False
DDR_CAB0 | DDR_DQSA1_P | B_ADDRESS_COMMAND | A_BYTE1 | L8 | actual_interconnect_only | track:DDR_CAB0:L8:671:3 | track:DDR_DQSA1_P:L8:710:1 | 8.2639678159 | 8.1623678159 | False | 3 | 0.1195 | 0.3585 | False | False | False
DDR_CAB0 | DDR_DQSA1_P | B_ADDRESS_COMMAND | A_BYTE1 | L8 | all_inner_layer_traces | track:DDR_CAB0:L8:671:3 | track:DDR_DQSA1_P:L8:710:1 | 8.2639678159 | 8.1623678159 | False | 3 | 0.1195 | 0.3585 | False | False | False
DDR_CAB1 | DDR_CAB3 | B_ADDRESS_COMMAND | B_ADDRESS_COMMAND | L8 | actual_interconnect_only | track:DDR_CAB1:L8:666:7 | track:DDR_CAB3:L8:695:0 | 0.89375 | 0.79215 | False | 3 | 0.1195 | 0.3585 | False | False | False
DDR_CAB1 | DDR_CAB3 | B_ADDRESS_COMMAND | B_ADDRESS_COMMAND | L8 | all_inner_layer_traces | track:DDR_CAB1:L8:666:7 | track:DDR_CAB3:L8:695:0 | 0.89375 | 0.79215 | False | 3 | 0.1195 | 0.3585 | False | False | False
DDR_CAB1 | DDR_CAB4 | B_ADDRESS_COMMAND | B_ADDRESS_COMMAND | L8 | actual_interconnect_only | track:DDR_CAB1:L8:666:4 | track:DDR_CAB4:L8:682:0 | 0.325 | 0.2234 | False | 3 | 0.1195 | 0.3585 | True | True | False
DDR_CAB1 | DDR_CAB4 | B_ADDRESS_COMMAND | B_ADDRESS_COMMAND | L8 | all_inner_layer_traces | track:DDR_CAB1:L8:666:4 | track:DDR_CAB4:L8:682:0 | 0.325 | 0.2234 | False | 3 | 0.1195 | 0.3585 | True | True | False
DDR_CAB1 | DDR_CAB5 | B_ADDRESS_COMMAND | B_ADDRESS_COMMAND | L8 | actual_interconnect_only | track:DDR_CAB1:L8:666:0 | track:DDR_CAB5:L8:707:3 | 0.2298097039 | 0.1282097039 | False | 3 | 0.1195 | 0.3585 | True | True | True
DDR_CAB1 | DDR_CAB5 | B_ADDRESS_COMMAND | B_ADDRESS_COMMAND | L8 | all_inner_layer_traces | track:DDR_CAB1:L8:666:0 | track:DDR_CAB5:L8:707:3 | 0.2298097039 | 0.1282097039 | False | 3 | 0.1195 | 0.3585 | True | True | True
DDR_CAB1 | DDR_CKEA0 | B_ADDRESS_COMMAND | A_ADDRESS_COMMAND | L8 | actual_interconnect_only | track:DDR_CAB1:L8:666:14 | track:DDR_CKEA0:L8:670:2 | 0.65 | 0.5484 | False | 3 | 0.1195 | 0.3585 | False | False | False
DDR_CAB1 | DDR_CKEA0 | B_ADDRESS_COMMAND | A_ADDRESS_COMMAND | L8 | all_inner_layer_traces | track:DDR_CAB1:L8:666:14 | track:DDR_CKEA0:L8:670:2 | 0.65 | 0.5484 | False | 3 | 0.1195 | 0.3585 | False | False | False
DDR_CAB1 | DDR_CKEB0 | B_ADDRESS_COMMAND | B_ADDRESS_COMMAND | L8 | actual_interconnect_only | track:DDR_CAB1:L8:666:18 | track:DDR_CKEB0:L8:672:15 | 0.24375 | 0.14215 | False | 3 | 0.1195 | 0.3585 | True | True | True
DDR_CAB1 | DDR_CKEB0 | B_ADDRESS_COMMAND | B_ADDRESS_COMMAND | L8 | all_inner_layer_traces | track:DDR_CAB1:L8:666:18 | track:DDR_CKEB0:L8:672:15 | 0.24375 | 0.14215 | False | 3 | 0.1195 | 0.3585 | True | True | True
DDR_CAB1 | DDR_CSB0 | B_ADDRESS_COMMAND | B_ADDRESS_COMMAND | L8 | actual_interconnect_only | track:DDR_CAB1:L8:666:18 | track:DDR_CSB0:L8:677:14 | 0.4875 | 0.3859 | False | 3 | 0.1195 | 0.3585 | False | False | False
DDR_CAB1 | DDR_CSB0 | B_ADDRESS_COMMAND | B_ADDRESS_COMMAND | L8 | all_inner_layer_traces | track:DDR_CAB1:L8:666:18 | track:DDR_CSB0:L8:677:14 | 0.4875 | 0.3859 | False | 3 | 0.1195 | 0.3585 | False | False | False
DDR_CAB1 | DDR_DMIA1 | B_ADDRESS_COMMAND | A_BYTE1 | L8 | actual_interconnect_only | track:DDR_CAB1:L8:666:15 | track:DDR_DMIA1:L8:675:0 | 1.625 | 1.5234 | False | 3 | 0.1195 | 0.3585 | False | False | False
DDR_CAB1 | DDR_DMIA1 | B_ADDRESS_COMMAND | A_BYTE1 | L8 | all_inner_layer_traces | track:DDR_CAB1:L8:666:15 | track:DDR_DMIA1:L8:675:0 | 1.625 | 1.5234 | False | 3 | 0.1195 | 0.3585 | False | False | False
DDR_CAB1 | DDR_DMIB0 | B_ADDRESS_COMMAND | B_BYTE0 | L8 | actual_interconnect_only | track:DDR_CAB1:L8:666:4 | track:DDR_DMIB0:L8:654:8 | 1.3 | 1.1984 | False | 3 | 0.1195 | 0.3585 | False | False | False
DDR_CAB1 | DDR_DMIB0 | B_ADDRESS_COMMAND | B_BYTE0 | L8 | all_inner_layer_traces | track:DDR_CAB1:L8:666:4 | track:DDR_DMIB0:L8:654:8 | 1.3 | 1.1984 | False | 3 | 0.1195 | 0.3585 | False | False | False
DDR_CAB1 | DDR_DMIB1 | B_ADDRESS_COMMAND | B_BYTE1 | L8 | actual_interconnect_only | track:DDR_CAB1:L8:666:4 | track:DDR_DMIB1:L8:684:0 | 1.625 | 1.5234 | False | 3 | 0.1195 | 0.3585 | False | False | False
DDR_CAB1 | DDR_DMIB1 | B_ADDRESS_COMMAND | B_BYTE1 | L8 | all_inner_layer_traces | track:DDR_CAB1:L8:666:4 | track:DDR_DMIB1:L8:684:0 | 1.625 | 1.5234 | False | 3 | 0.1195 | 0.3585 | False | False | False
DDR_CAB1 | DDR_DQA10 | B_ADDRESS_COMMAND | A_BYTE1 | L8 | actual_interconnect_only | track:DDR_CAB1:L8:666:15 | track:DDR_DQA10:L8:678:3 | 1.3 | 1.1984 | False | 3 | 0.1195 | 0.3585 | False | False | False
DDR_CAB1 | DDR_DQA10 | B_ADDRESS_COMMAND | A_BYTE1 | L8 | all_inner_layer_traces | track:DDR_CAB1:L8:666:15 | track:DDR_DQA10:L8:678:3 | 1.3 | 1.1984 | False | 3 | 0.1195 | 0.3585 | False | False | False
DDR_CAB1 | DDR_DQA11 | B_ADDRESS_COMMAND | A_BYTE1 | L8 | actual_interconnect_only | track:DDR_CAB1:L8:666:15 | track:DDR_DQA11:L8:705:9 | 1.95 | 1.8484 | False | 3 | 0.1195 | 0.3585 | False | False | False
DDR_CAB1 | DDR_DQA11 | B_ADDRESS_COMMAND | A_BYTE1 | L8 | all_inner_layer_traces | track:DDR_CAB1:L8:666:15 | track:DDR_DQA11:L8:705:9 | 1.95 | 1.8484 | False | 3 | 0.1195 | 0.3585 | False | False | False
DDR_CAB1 | DDR_DQA12 | B_ADDRESS_COMMAND | A_BYTE1 | L8 | actual_interconnect_only | track:DDR_CAB1:L8:666:15 | track:DDR_DQA12:L8:688:9 | 0.65 | 0.5484 | False | 3 | 0.1195 | 0.3585 | False | False | False
DDR_CAB1 | DDR_DQA12 | B_ADDRESS_COMMAND | A_BYTE1 | L8 | all_inner_layer_traces | track:DDR_CAB1:L8:666:15 | track:DDR_DQA12:L8:688:9 | 0.65 | 0.5484 | False | 3 | 0.1195 | 0.3585 | False | False | False
DDR_CAB1 | DDR_DQA13 | B_ADDRESS_COMMAND | A_BYTE1 | L8 | actual_interconnect_only | track:DDR_CAB1:L8:666:15 | track:DDR_DQA13:L8:693:11 | 1.3 | 1.1984 | False | 3 | 0.1195 | 0.3585 | False | False | False
DDR_CAB1 | DDR_DQA13 | B_ADDRESS_COMMAND | A_BYTE1 | L8 | all_inner_layer_traces | track:DDR_CAB1:L8:666:15 | track:DDR_DQA13:L8:693:11 | 1.3 | 1.1984 | False | 3 | 0.1195 | 0.3585 | False | False | False
DDR_CAB1 | DDR_DQA14 | B_ADDRESS_COMMAND | A_BYTE1 | L8 | actual_interconnect_only | track:DDR_CAB1:L8:666:15 | track:DDR_DQA14:L8:683:3 | 3.25 | 3.1484 | False | 3 | 0.1195 | 0.3585 | False | False | False
DDR_CAB1 | DDR_DQA14 | B_ADDRESS_COMMAND | A_BYTE1 | L8 | all_inner_layer_traces | track:DDR_CAB1:L8:666:15 | track:DDR_DQA14:L8:683:3 | 3.25 | 3.1484 | False | 3 | 0.1195 | 0.3585 | False | False | False
DDR_CAB1 | DDR_DQA15 | B_ADDRESS_COMMAND | A_BYTE1 | L8 | actual_interconnect_only | track:DDR_CAB1:L8:666:15 | track:DDR_DQA15:L8:698:1 | 3.49375 | 3.39215 | False | 3 | 0.1195 | 0.3585 | False | False | False
DDR_CAB1 | DDR_DQA15 | B_ADDRESS_COMMAND | A_BYTE1 | L8 | all_inner_layer_traces | track:DDR_CAB1:L8:666:15 | track:DDR_DQA15:L8:698:1 | 3.49375 | 3.39215 | False | 3 | 0.1195 | 0.3585 | False | False | False
DDR_CAB1 | DDR_DQA3 | B_ADDRESS_COMMAND | A_BYTE0 | L8 | actual_interconnect_only | track:DDR_CAB1:L8:666:14 | track:DDR_DQA3:L8:649:2 | 2.6 | 2.4984 | False | 3 | 0.1195 | 0.3585 | False | False | False
DDR_CAB1 | DDR_DQA3 | B_ADDRESS_COMMAND | A_BYTE0 | L8 | all_inner_layer_traces | track:DDR_CAB1:L8:666:14 | track:DDR_DQA3:L8:649:2 | 2.6 | 2.4984 | False | 3 | 0.1195 | 0.3585 | False | False | False
DDR_CAB1 | DDR_DQA7 | B_ADDRESS_COMMAND | A_BYTE0 | L8 | actual_interconnect_only | track:DDR_CAB1:L8:666:15 | track:DDR_DQA7:L8:669:0 | 5.525 | 5.4234 | False | 3 | 0.1195 | 0.3585 | False | False | False
DDR_CAB1 | DDR_DQA7 | B_ADDRESS_COMMAND | A_BYTE0 | L8 | all_inner_layer_traces | track:DDR_CAB1:L8:666:15 | track:DDR_DQA7:L8:669:0 | 5.525 | 5.4234 | False | 3 | 0.1195 | 0.3585 | False | False | False
DDR_CAB1 | DDR_DQA9 | B_ADDRESS_COMMAND | A_BYTE1 | L8 | actual_interconnect_only | track:DDR_CAB1:L8:666:15 | track:DDR_DQA9:L8:686:0 | 2.925 | 2.8234 | False | 3 | 0.1195 | 0.3585 | False | False | False
DDR_CAB1 | DDR_DQA9 | B_ADDRESS_COMMAND | A_BYTE1 | L8 | all_inner_layer_traces | track:DDR_CAB1:L8:666:15 | track:DDR_DQA9:L8:686:0 | 2.925 | 2.8234 | False | 3 | 0.1195 | 0.3585 | False | False | False
DDR_CAB1 | DDR_DQB0 | B_ADDRESS_COMMAND | B_BYTE0 | L8 | actual_interconnect_only | track:DDR_CAB1:L8:666:9 | track:DDR_DQB0:L8:653:0 | 3.6490206306 | 3.5474206306 | False | 3 | 0.1195 | 0.3585 | False | False | False
DDR_CAB1 | DDR_DQB0 | B_ADDRESS_COMMAND | B_BYTE0 | L8 | all_inner_layer_traces | track:DDR_CAB1:L8:666:9 | track:DDR_DQB0:L8:653:0 | 3.6490206306 | 3.5474206306 | False | 3 | 0.1195 | 0.3585 | False | False | False
DDR_CAB1 | DDR_DQB1 | B_ADDRESS_COMMAND | B_BYTE0 | L8 | actual_interconnect_only | track:DDR_CAB1:L8:666:5 | track:DDR_DQB1:L8:662:0 | 3.5759231763 | 3.4743231763 | False | 3 | 0.1195 | 0.3585 | False | False | False
DDR_CAB1 | DDR_DQB1 | B_ADDRESS_COMMAND | B_BYTE0 | L8 | all_inner_layer_traces | track:DDR_CAB1:L8:666:5 | track:DDR_DQB1:L8:662:0 | 3.5759231763 | 3.4743231763 | False | 3 | 0.1195 | 0.3585 | False | False | False
DDR_CAB1 | DDR_DQB11 | B_ADDRESS_COMMAND | B_BYTE1 | L8 | actual_interconnect_only | track:DDR_CAB1:L8:666:34 | track:DDR_DQB11:L8:694:54 | 0.325 | 0.2234 | False | 3 | 0.1195 | 0.3585 | True | True | False
DDR_CAB1 | DDR_DQB11 | B_ADDRESS_COMMAND | B_BYTE1 | L8 | all_inner_layer_traces | track:DDR_CAB1:L8:666:34 | track:DDR_DQB11:L8:694:54 | 0.325 | 0.2234 | False | 3 | 0.1195 | 0.3585 | True | True | False
DDR_CAB1 | DDR_DQB3 | B_ADDRESS_COMMAND | B_BYTE0 | L8 | actual_interconnect_only | track:DDR_CAB1:L8:666:34 | track:DDR_DQB3:L8:646:28 | 1.95 | 1.8484 | False | 3 | 0.1195 | 0.3585 | False | False | False
DDR_CAB1 | DDR_DQB3 | B_ADDRESS_COMMAND | B_BYTE0 | L8 | all_inner_layer_traces | track:DDR_CAB1:L8:666:34 | track:DDR_DQB3:L8:646:28 | 1.95 | 1.8484 | False | 3 | 0.1195 | 0.3585 | False | False | False
DDR_CAB1 | DDR_DQB5 | B_ADDRESS_COMMAND | B_BYTE0 | L8 | actual_interconnect_only | track:DDR_CAB1:L8:666:34 | track:DDR_DQB5:L8:665:39 | 1.625 | 1.5234 | False | 3 | 0.1195 | 0.3585 | False | False | False
DDR_CAB1 | DDR_DQB5 | B_ADDRESS_COMMAND | B_BYTE0 | L8 | all_inner_layer_traces | track:DDR_CAB1:L8:666:34 | track:DDR_DQB5:L8:665:39 | 1.625 | 1.5234 | False | 3 | 0.1195 | 0.3585 | False | False | False
DDR_CAB1 | DDR_DQB6 | B_ADDRESS_COMMAND | B_BYTE0 | L8 | actual_interconnect_only | track:DDR_CAB1:L8:666:8 | track:DDR_DQB6:L8:664:0 | 2.275 | 2.1734 | False | 3 | 0.1195 | 0.3585 | False | False | False
DDR_CAB1 | DDR_DQB6 | B_ADDRESS_COMMAND | B_BYTE0 | L8 | all_inner_layer_traces | track:DDR_CAB1:L8:666:8 | track:DDR_DQB6:L8:664:0 | 2.275 | 2.1734 | False | 3 | 0.1195 | 0.3585 | False | False | False
DDR_CAB1 | DDR_DQB7 | B_ADDRESS_COMMAND | B_BYTE0 | L8 | actual_interconnect_only | track:DDR_CAB1:L8:666:5 | track:DDR_DQB7:L8:660:0 | 2.9261282546 | 2.8245282546 | False | 3 | 0.1195 | 0.3585 | False | False | False
DDR_CAB1 | DDR_DQB7 | B_ADDRESS_COMMAND | B_BYTE0 | L8 | all_inner_layer_traces | track:DDR_CAB1:L8:666:5 | track:DDR_DQB7:L8:660:0 | 2.9261282546 | 2.8245282546 | False | 3 | 0.1195 | 0.3585 | False | False | False
DDR_CAB1 | DDR_DQSA1_N | B_ADDRESS_COMMAND | A_BYTE1 | L8 | actual_interconnect_only | track:DDR_CAB1:L8:666:15 | track:DDR_DQSA1_N:L8:687:0 | 4.225 | 4.1234 | False | 3 | 0.1195 | 0.3585 | False | False | False
DDR_CAB1 | DDR_DQSA1_N | B_ADDRESS_COMMAND | A_BYTE1 | L8 | all_inner_layer_traces | track:DDR_CAB1:L8:666:15 | track:DDR_DQSA1_N:L8:687:0 | 4.225 | 4.1234 | False | 3 | 0.1195 | 0.3585 | False | False | False
DDR_CAB1 | DDR_DQSA1_P | B_ADDRESS_COMMAND | A_BYTE1 | L8 | actual_interconnect_only | track:DDR_CAB1:L8:666:15 | track:DDR_DQSA1_P:L8:710:0 | 4.225 | 4.1234 | False | 3 | 0.1195 | 0.3585 | False | False | False
DDR_CAB1 | DDR_DQSA1_P | B_ADDRESS_COMMAND | A_BYTE1 | L8 | all_inner_layer_traces | track:DDR_CAB1:L8:666:15 | track:DDR_DQSA1_P:L8:710:0 | 4.225 | 4.1234 | False | 3 | 0.1195 | 0.3585 | False | False | False
DDR_CAB2 | DDR_CLKA_N | B_ADDRESS_COMMAND | A_ADDRESS_COMMAND | L3 | actual_interconnect_only | track:DDR_CAB2:L3:696:19 | track:DDR_CLKA_N:L3:680:17 | 3.9 | 3.7984 | False | 3 | 0.13 | 0.39 | False | False | False
DDR_CAB2 | DDR_CLKA_N | B_ADDRESS_COMMAND | A_ADDRESS_COMMAND | L3 | all_inner_layer_traces | track:DDR_CAB2:L3:696:19 | track:DDR_CLKA_N:L3:680:17 | 3.9 | 3.7984 | False | 3 | 0.13 | 0.39 | False | False | False
DDR_CAB2 | DDR_CLKA_P | B_ADDRESS_COMMAND | A_ADDRESS_COMMAND | L3 | actual_interconnect_only | track:DDR_CAB2:L3:696:19 | track:DDR_CLKA_P:L3:676:9 | 2.275 | 2.1734 | False | 3 | 0.13 | 0.39 | False | False | False
DDR_CAB2 | DDR_CLKA_P | B_ADDRESS_COMMAND | A_ADDRESS_COMMAND | L3 | all_inner_layer_traces | track:DDR_CAB2:L3:696:19 | track:DDR_CLKA_P:L3:676:9 | 2.275 | 2.1734 | False | 3 | 0.13 | 0.39 | False | False | False
DDR_CAB2 | DDR_CLKB_N | B_ADDRESS_COMMAND | B_ADDRESS_COMMAND | L3 | actual_interconnect_only | track:DDR_CAB2:L3:696:18 | track:DDR_CLKB_N:L3:701:7 | 0.0 | -0.1016 | False | 3 | 0.13 | 0.39 | True | True | True
DDR_CAB2 | DDR_CLKB_N | B_ADDRESS_COMMAND | B_ADDRESS_COMMAND | L3 | all_inner_layer_traces | track:DDR_CAB2:L3:696:18 | track:DDR_CLKB_N:L3:701:7 | 0.0 | -0.1016 | False | 3 | 0.13 | 0.39 | True | True | True
DDR_CAB2 | DDR_CLKB_P | B_ADDRESS_COMMAND | B_ADDRESS_COMMAND | L3 | actual_interconnect_only | track:DDR_CAB2:L3:696:0 | track:DDR_CLKB_P:L3:700:1 | 0.325 | 0.2234 | False | 3 | 0.13 | 0.39 | True | True | False
DDR_CAB2 | DDR_CLKB_P | B_ADDRESS_COMMAND | B_ADDRESS_COMMAND | L3 | all_inner_layer_traces | track:DDR_CAB2:L3:696:0 | track:DDR_CLKB_P:L3:700:1 | 0.325 | 0.2234 | False | 3 | 0.13 | 0.39 | True | True | False
DDR_CAB2 | DDR_CSA0 | B_ADDRESS_COMMAND | A_ADDRESS_COMMAND | L3 | actual_interconnect_only | track:DDR_CAB2:L3:696:19 | track:DDR_CSA0:L3:679:4 | 5.525 | 5.4234 | False | 3 | 0.13 | 0.39 | False | False | False
DDR_CAB2 | DDR_CSA0 | B_ADDRESS_COMMAND | A_ADDRESS_COMMAND | L3 | all_inner_layer_traces | track:DDR_CAB2:L3:696:19 | track:DDR_CSA0:L3:679:4 | 5.525 | 5.4234 | False | 3 | 0.13 | 0.39 | False | False | False
DDR_CAB2 | DDR_DMIA0 | B_ADDRESS_COMMAND | A_BYTE0 | L3 | actual_interconnect_only | track:DDR_CAB2:L3:696:0 | track:DDR_DMIA0:L3:661:0 | 7.1794846612 | 7.0778846612 | False | 3 | 0.13 | 0.39 | False | False | False
DDR_CAB2 | DDR_DMIA0 | B_ADDRESS_COMMAND | A_BYTE0 | L3 | all_inner_layer_traces | track:DDR_CAB2:L3:696:0 | track:DDR_DMIA0:L3:661:0 | 7.1794846612 | 7.0778846612 | False | 3 | 0.13 | 0.39 | False | False | False
DDR_CAB2 | DDR_DQA0 | B_ADDRESS_COMMAND | A_BYTE0 | L3 | actual_interconnect_only | track:DDR_CAB2:L3:696:0 | track:DDR_DQA0:L3:648:0 | 8.5494151847 | 8.4478151847 | False | 3 | 0.13 | 0.39 | False | False | False
DDR_CAB2 | DDR_DQA0 | B_ADDRESS_COMMAND | A_BYTE0 | L3 | all_inner_layer_traces | track:DDR_CAB2:L3:696:0 | track:DDR_DQA0:L3:648:0 | 8.5494151847 | 8.4478151847 | False | 3 | 0.13 | 0.39 | False | False | False
DDR_CAB2 | DDR_DQA1 | B_ADDRESS_COMMAND | A_BYTE0 | L3 | actual_interconnect_only | track:DDR_CAB2:L3:696:11 | track:DDR_DQA1:L3:658:8 | 6.07150105 | 5.96990105 | False | 3 | 0.13 | 0.39 | False | False | False
DDR_CAB2 | DDR_DQA1 | B_ADDRESS_COMMAND | A_BYTE0 | L3 | all_inner_layer_traces | track:DDR_CAB2:L3:696:11 | track:DDR_DQA1:L3:658:8 | 6.07150105 | 5.96990105 | False | 3 | 0.13 | 0.39 | False | False | False
DDR_CAB2 | DDR_DQA2 | B_ADDRESS_COMMAND | A_BYTE0 | L3 | actual_interconnect_only | track:DDR_CAB2:L3:696:0 | track:DDR_DQA2:L3:668:1 | 6.25149982 | 6.14989982 | False | 3 | 0.13 | 0.39 | False | False | False
DDR_CAB2 | DDR_DQA2 | B_ADDRESS_COMMAND | A_BYTE0 | L3 | all_inner_layer_traces | track:DDR_CAB2:L3:696:0 | track:DDR_DQA2:L3:668:1 | 6.25149982 | 6.14989982 | False | 3 | 0.13 | 0.39 | False | False | False
DDR_CAB2 | DDR_DQA4 | B_ADDRESS_COMMAND | A_BYTE0 | L3 | actual_interconnect_only | track:DDR_CAB2:L3:696:0 | track:DDR_DQA4:L3:659:0 | 6.6287253677 | 6.5271253677 | False | 3 | 0.13 | 0.39 | False | False | False
DDR_CAB2 | DDR_DQA4 | B_ADDRESS_COMMAND | A_BYTE0 | L3 | all_inner_layer_traces | track:DDR_CAB2:L3:696:0 | track:DDR_DQA4:L3:659:0 | 6.6287253677 | 6.5271253677 | False | 3 | 0.13 | 0.39 | False | False | False
DDR_CAB2 | DDR_DQA5 | B_ADDRESS_COMMAND | A_BYTE0 | L3 | actual_interconnect_only | track:DDR_CAB2:L3:696:11 | track:DDR_DQA5:L3:667:6 | 6.5992808557 | 6.4976808557 | False | 3 | 0.13 | 0.39 | False | False | False
DDR_CAB2 | DDR_DQA5 | B_ADDRESS_COMMAND | A_BYTE0 | L3 | all_inner_layer_traces | track:DDR_CAB2:L3:696:11 | track:DDR_DQA5:L3:667:6 | 6.5992808557 | 6.4976808557 | False | 3 | 0.13 | 0.39 | False | False | False
DDR_CAB2 | DDR_DQA6 | B_ADDRESS_COMMAND | A_BYTE0 | L3 | actual_interconnect_only | track:DDR_CAB2:L3:696:11 | track:DDR_DQA6:L3:674:4 | 7.1666000481 | 7.0650000481 | False | 3 | 0.13 | 0.39 | False | False | False
DDR_CAB2 | DDR_DQA6 | B_ADDRESS_COMMAND | A_BYTE0 | L3 | all_inner_layer_traces | track:DDR_CAB2:L3:696:11 | track:DDR_DQA6:L3:674:4 | 7.1666000481 | 7.0650000481 | False | 3 | 0.13 | 0.39 | False | False | False
DDR_CAB2 | DDR_DQA8 | B_ADDRESS_COMMAND | A_BYTE1 | L3 | actual_interconnect_only | track:DDR_CAB2:L3:696:0 | track:DDR_DQA8:L3:708:0 | 7.8067678972 | 7.7051678972 | False | 3 | 0.13 | 0.39 | False | False | False
DDR_CAB2 | DDR_DQA8 | B_ADDRESS_COMMAND | A_BYTE1 | L3 | all_inner_layer_traces | track:DDR_CAB2:L3:696:0 | track:DDR_DQA8:L3:708:0 | 7.8067678972 | 7.7051678972 | False | 3 | 0.13 | 0.39 | False | False | False
DDR_CAB2 | DDR_DQB10 | B_ADDRESS_COMMAND | B_BYTE1 | L3 | actual_interconnect_only | track:DDR_CAB2:L3:696:3 | track:DDR_DQB10:L3:703:4 | 1.3 | 1.1984 | False | 3 | 0.13 | 0.39 | False | False | False
DDR_CAB2 | DDR_DQB10 | B_ADDRESS_COMMAND | B_BYTE1 | L3 | all_inner_layer_traces | track:DDR_CAB2:L3:696:3 | track:DDR_DQB10:L3:703:4 | 1.3 | 1.1984 | False | 3 | 0.13 | 0.39 | False | False | False
DDR_CAB2 | DDR_DQB12 | B_ADDRESS_COMMAND | B_BYTE1 | L3 | actual_interconnect_only | track:DDR_CAB2:L3:696:3 | track:DDR_DQB12:L3:691:3 | 0.65 | 0.5484 | False | 3 | 0.13 | 0.39 | False | False | False
DDR_CAB2 | DDR_DQB12 | B_ADDRESS_COMMAND | B_BYTE1 | L3 | all_inner_layer_traces | track:DDR_CAB2:L3:696:3 | track:DDR_DQB12:L3:691:3 | 0.65 | 0.5484 | False | 3 | 0.13 | 0.39 | False | False | False
DDR_CAB2 | DDR_DQB13 | B_ADDRESS_COMMAND | B_BYTE1 | L3 | actual_interconnect_only | track:DDR_CAB2:L3:696:18 | track:DDR_DQB13:L3:673:31 | 1.625 | 1.5234 | False | 3 | 0.13 | 0.39 | False | False | False
DDR_CAB2 | DDR_DQB13 | B_ADDRESS_COMMAND | B_BYTE1 | L3 | all_inner_layer_traces | track:DDR_CAB2:L3:696:18 | track:DDR_DQB13:L3:673:31 | 1.625 | 1.5234 | False | 3 | 0.13 | 0.39 | False | False | False
DDR_CAB2 | DDR_DQB14 | B_ADDRESS_COMMAND | B_BYTE1 | L3 | actual_interconnect_only | track:DDR_CAB2:L3:696:4 | track:DDR_DQB14:L3:681:0 | 2.275 | 2.1734 | False | 3 | 0.13 | 0.39 | False | False | False
DDR_CAB2 | DDR_DQB14 | B_ADDRESS_COMMAND | B_BYTE1 | L3 | all_inner_layer_traces | track:DDR_CAB2:L3:696:4 | track:DDR_DQB14:L3:681:0 | 2.275 | 2.1734 | False | 3 | 0.13 | 0.39 | False | False | False
DDR_CAB2 | DDR_DQB15 | B_ADDRESS_COMMAND | B_BYTE1 | L3 | actual_interconnect_only | track:DDR_CAB2:L3:696:4 | track:DDR_DQB15:L3:692:0 | 2.925 | 2.8234 | False | 3 | 0.13 | 0.39 | False | False | False
DDR_CAB2 | DDR_DQB15 | B_ADDRESS_COMMAND | B_BYTE1 | L3 | all_inner_layer_traces | track:DDR_CAB2:L3:696:4 | track:DDR_DQB15:L3:692:0 | 2.925 | 2.8234 | False | 3 | 0.13 | 0.39 | False | False | False
DDR_CAB2 | DDR_DQB2 | B_ADDRESS_COMMAND | B_BYTE0 | L3 | actual_interconnect_only | track:DDR_CAB2:L3:696:18 | track:DDR_DQB2:L3:655:93 | 2.6736927296 | 2.5720927296 | False | 3 | 0.13 | 0.39 | False | False | False
DDR_CAB2 | DDR_DQB2 | B_ADDRESS_COMMAND | B_BYTE0 | L3 | all_inner_layer_traces | track:DDR_CAB2:L3:696:18 | track:DDR_DQB2:L3:655:93 | 2.6736927296 | 2.5720927296 | False | 3 | 0.13 | 0.39 | False | False | False
DDR_CAB2 | DDR_DQB4 | B_ADDRESS_COMMAND | B_BYTE0 | L3 | actual_interconnect_only | track:DDR_CAB2:L3:696:18 | track:DDR_DQB4:L3:663:115 | 2.4341403128 | 2.3325403128 | False | 3 | 0.13 | 0.39 | False | False | False
DDR_CAB2 | DDR_DQB4 | B_ADDRESS_COMMAND | B_BYTE0 | L3 | all_inner_layer_traces | track:DDR_CAB2:L3:696:18 | track:DDR_DQB4:L3:663:115 | 2.4341403128 | 2.3325403128 | False | 3 | 0.13 | 0.39 | False | False | False
DDR_CAB2 | DDR_DQB8 | B_ADDRESS_COMMAND | B_BYTE1 | L3 | actual_interconnect_only | track:DDR_CAB2:L3:696:3 | track:DDR_DQB8:L3:706:0 | 2.2764504305 | 2.1748504305 | False | 3 | 0.13 | 0.39 | False | False | False
DDR_CAB2 | DDR_DQB8 | B_ADDRESS_COMMAND | B_BYTE1 | L3 | all_inner_layer_traces | track:DDR_CAB2:L3:696:3 | track:DDR_DQB8:L3:706:0 | 2.2764504305 | 2.1748504305 | False | 3 | 0.13 | 0.39 | False | False | False
DDR_CAB2 | DDR_DQB9 | B_ADDRESS_COMMAND | B_BYTE1 | L3 | actual_interconnect_only | track:DDR_CAB2:L3:696:3 | track:DDR_DQB9:L3:704:4 | 1.95 | 1.8484 | False | 3 | 0.13 | 0.39 | False | False | False
DDR_CAB2 | DDR_DQB9 | B_ADDRESS_COMMAND | B_BYTE1 | L3 | all_inner_layer_traces | track:DDR_CAB2:L3:696:3 | track:DDR_DQB9:L3:704:4 | 1.95 | 1.8484 | False | 3 | 0.13 | 0.39 | False | False | False
DDR_CAB2 | DDR_DQSA0_N | B_ADDRESS_COMMAND | A_BYTE0 | L3 | actual_interconnect_only | track:DDR_CAB2:L3:696:19 | track:DDR_DQSA0_N:L3:657:29 | 8.0802227692 | 7.9786227692 | False | 3 | 0.13 | 0.39 | False | False | False
DDR_CAB2 | DDR_DQSA0_N | B_ADDRESS_COMMAND | A_BYTE0 | L3 | all_inner_layer_traces | track:DDR_CAB2:L3:696:19 | track:DDR_DQSA0_N:L3:657:29 | 8.0802227692 | 7.9786227692 | False | 3 | 0.13 | 0.39 | False | False | False
DDR_CAB2 | DDR_DQSA0_P | B_ADDRESS_COMMAND | A_BYTE0 | L3 | actual_interconnect_only | track:DDR_CAB2:L3:696:0 | track:DDR_DQSA0_P:L3:652:1 | 7.5383187781 | 7.4367187781 | False | 3 | 0.13 | 0.39 | False | False | False
DDR_CAB2 | DDR_DQSA0_P | B_ADDRESS_COMMAND | A_BYTE0 | L3 | all_inner_layer_traces | track:DDR_CAB2:L3:696:0 | track:DDR_DQSA0_P:L3:652:1 | 7.5383187781 | 7.4367187781 | False | 3 | 0.13 | 0.39 | False | False | False
DDR_CAB2 | DDR_DQSB0_N | B_ADDRESS_COMMAND | B_BYTE0 | L3 | actual_interconnect_only | track:DDR_CAB2:L3:696:18 | track:DDR_DQSB0_N:L3:650:46 | 3.740916081 | 3.639316081 | False | 3 | 0.13 | 0.39 | False | False | False
DDR_CAB2 | DDR_DQSB0_N | B_ADDRESS_COMMAND | B_BYTE0 | L3 | all_inner_layer_traces | track:DDR_CAB2:L3:696:18 | track:DDR_DQSB0_N:L3:650:46 | 3.740916081 | 3.639316081 | False | 3 | 0.13 | 0.39 | False | False | False
DDR_CAB2 | DDR_DQSB0_P | B_ADDRESS_COMMAND | B_BYTE0 | L3 | actual_interconnect_only | track:DDR_CAB2:L3:696:18 | track:DDR_DQSB0_P:L3:651:79 | 2.9483708425 | 2.8467708425 | False | 3 | 0.13 | 0.39 | False | False | False
DDR_CAB2 | DDR_DQSB0_P | B_ADDRESS_COMMAND | B_BYTE0 | L3 | all_inner_layer_traces | track:DDR_CAB2:L3:696:18 | track:DDR_DQSB0_P:L3:651:79 | 2.9483708425 | 2.8467708425 | False | 3 | 0.13 | 0.39 | False | False | False
DDR_CAB2 | DDR_DQSB1_N | B_ADDRESS_COMMAND | B_BYTE1 | L3 | actual_interconnect_only | track:DDR_CAB2:L3:696:18 | track:DDR_DQSB1_N:L3:697:37 | 0.65 | 0.5484 | False | 3 | 0.13 | 0.39 | False | False | False
DDR_CAB2 | DDR_DQSB1_N | B_ADDRESS_COMMAND | B_BYTE1 | L3 | all_inner_layer_traces | track:DDR_CAB2:L3:696:18 | track:DDR_DQSB1_N:L3:697:37 | 0.65 | 0.5484 | False | 3 | 0.13 | 0.39 | False | False | False
DDR_CAB2 | DDR_DQSB1_P | B_ADDRESS_COMMAND | B_BYTE1 | L3 | actual_interconnect_only | track:DDR_CAB2:L3:696:18 | track:DDR_DQSB1_P:L3:690:13 | 2.275 | 2.1734 | False | 3 | 0.13 | 0.39 | False | False | False
DDR_CAB2 | DDR_DQSB1_P | B_ADDRESS_COMMAND | B_BYTE1 | L3 | all_inner_layer_traces | track:DDR_CAB2:L3:696:18 | track:DDR_DQSB1_P:L3:690:13 | 2.275 | 2.1734 | False | 3 | 0.13 | 0.39 | False | False | False
DDR_CAB3 | DDR_CAB4 | B_ADDRESS_COMMAND | B_ADDRESS_COMMAND | L8 | actual_interconnect_only | track:DDR_CAB3:L8:695:23 | track:DDR_CAB4:L8:682:19 | 0.6250312492 | 0.5234312492 | False | 3 | 0.1195 | 0.3585 | False | False | False
DDR_CAB3 | DDR_CAB4 | B_ADDRESS_COMMAND | B_ADDRESS_COMMAND | L8 | all_inner_layer_traces | track:DDR_CAB3:L8:695:23 | track:DDR_CAB4:L8:682:19 | 0.6250312492 | 0.5234312492 | False | 3 | 0.1195 | 0.3585 | False | False | False
DDR_CAB3 | DDR_CAB5 | B_ADDRESS_COMMAND | B_ADDRESS_COMMAND | L8 | actual_interconnect_only | track:DDR_CAB3:L8:695:16 | track:DDR_CAB5:L8:707:21 | 0.216956937 | 0.115356937 | False | 3 | 0.1195 | 0.3585 | True | True | True
DDR_CAB3 | DDR_CAB5 | B_ADDRESS_COMMAND | B_ADDRESS_COMMAND | L8 | all_inner_layer_traces | track:DDR_CAB3:L8:695:16 | track:DDR_CAB5:L8:707:21 | 0.216956937 | 0.115356937 | False | 3 | 0.1195 | 0.3585 | True | True | True
DDR_CAB3 | DDR_CKEA0 | B_ADDRESS_COMMAND | A_ADDRESS_COMMAND | L8 | actual_interconnect_only | track:DDR_CAB3:L8:695:3 | track:DDR_CKEA0:L8:670:1 | 2.0826009129 | 1.9810009129 | False | 3 | 0.1195 | 0.3585 | False | False | False
DDR_CAB3 | DDR_CKEA0 | B_ADDRESS_COMMAND | A_ADDRESS_COMMAND | L8 | all_inner_layer_traces | track:DDR_CAB3:L8:695:3 | track:DDR_CKEA0:L8:670:1 | 2.0826009129 | 1.9810009129 | False | 3 | 0.1195 | 0.3585 | False | False | False
DDR_CAB3 | DDR_CKEB0 | B_ADDRESS_COMMAND | B_ADDRESS_COMMAND | L8 | actual_interconnect_only | track:DDR_CAB3:L8:695:0 | track:DDR_CKEB0:L8:672:1 | 0.2298097039 | 0.1282097039 | False | 3 | 0.1195 | 0.3585 | True | True | True
DDR_CAB3 | DDR_CKEB0 | B_ADDRESS_COMMAND | B_ADDRESS_COMMAND | L8 | all_inner_layer_traces | track:DDR_CAB3:L8:695:0 | track:DDR_CKEB0:L8:672:1 | 0.2298097039 | 0.1282097039 | False | 3 | 0.1195 | 0.3585 | True | True | True
DDR_CAB3 | DDR_CSB0 | B_ADDRESS_COMMAND | B_ADDRESS_COMMAND | L8 | actual_interconnect_only | track:DDR_CAB3:L8:695:21 | track:DDR_CSB0:L8:677:8 | 0.216956937 | 0.115356937 | False | 3 | 0.1195 | 0.3585 | True | True | True
DDR_CAB3 | DDR_CSB0 | B_ADDRESS_COMMAND | B_ADDRESS_COMMAND | L8 | all_inner_layer_traces | track:DDR_CAB3:L8:695:21 | track:DDR_CSB0:L8:677:8 | 0.216956937 | 0.115356937 | False | 3 | 0.1195 | 0.3585 | True | True | True
DDR_CAB3 | DDR_DMIA1 | B_ADDRESS_COMMAND | A_BYTE1 | L8 | actual_interconnect_only | track:DDR_CAB3:L8:695:3 | track:DDR_DMIA1:L8:675:0 | 2.9530770499 | 2.8514770499 | False | 3 | 0.1195 | 0.3585 | False | False | False
DDR_CAB3 | DDR_DMIA1 | B_ADDRESS_COMMAND | A_BYTE1 | L8 | all_inner_layer_traces | track:DDR_CAB3:L8:695:3 | track:DDR_DMIA1:L8:675:0 | 2.9530770499 | 2.8514770499 | False | 3 | 0.1195 | 0.3585 | False | False | False
DDR_CAB3 | DDR_DMIB0 | B_ADDRESS_COMMAND | B_BYTE0 | L8 | actual_interconnect_only | track:DDR_CAB3:L8:695:27 | track:DDR_DMIB0:L8:654:8 | 2.275 | 2.1734 | False | 3 | 0.1195 | 0.3585 | False | False | False
DDR_CAB3 | DDR_DMIB0 | B_ADDRESS_COMMAND | B_BYTE0 | L8 | all_inner_layer_traces | track:DDR_CAB3:L8:695:27 | track:DDR_DMIB0:L8:654:8 | 2.275 | 2.1734 | False | 3 | 0.1195 | 0.3585 | False | False | False
DDR_CAB3 | DDR_DMIB1 | B_ADDRESS_COMMAND | B_BYTE1 | L8 | actual_interconnect_only | track:DDR_CAB3:L8:695:0 | track:DDR_DMIB1:L8:684:0 | 2.6202337682 | 2.5186337682 | False | 3 | 0.1195 | 0.3585 | False | False | False
DDR_CAB3 | DDR_DMIB1 | B_ADDRESS_COMMAND | B_BYTE1 | L8 | all_inner_layer_traces | track:DDR_CAB3:L8:695:0 | track:DDR_DMIB1:L8:684:0 | 2.6202337682 | 2.5186337682 | False | 3 | 0.1195 | 0.3585 | False | False | False
DDR_CAB3 | DDR_DQA10 | B_ADDRESS_COMMAND | A_BYTE1 | L8 | actual_interconnect_only | track:DDR_CAB3:L8:695:4 | track:DDR_DQA10:L8:678:7 | 2.6012692215 | 2.4996692215 | False | 3 | 0.1195 | 0.3585 | False | False | False
DDR_CAB3 | DDR_DQA10 | B_ADDRESS_COMMAND | A_BYTE1 | L8 | all_inner_layer_traces | track:DDR_CAB3:L8:695:4 | track:DDR_DQA10:L8:678:7 | 2.6012692215 | 2.4996692215 | False | 3 | 0.1195 | 0.3585 | False | False | False
DDR_CAB3 | DDR_DQA11 | B_ADDRESS_COMMAND | A_BYTE1 | L8 | actual_interconnect_only | track:DDR_CAB3:L8:695:4 | track:DDR_DQA11:L8:705:9 | 3.2510154664 | 3.1494154664 | False | 3 | 0.1195 | 0.3585 | False | False | False
DDR_CAB3 | DDR_DQA11 | B_ADDRESS_COMMAND | A_BYTE1 | L8 | all_inner_layer_traces | track:DDR_CAB3:L8:695:4 | track:DDR_DQA11:L8:705:9 | 3.2510154664 | 3.1494154664 | False | 3 | 0.1195 | 0.3585 | False | False | False
DDR_CAB3 | DDR_DQA12 | B_ADDRESS_COMMAND | A_BYTE1 | L8 | actual_interconnect_only | track:DDR_CAB3:L8:695:21 | track:DDR_DQA12:L8:688:10 | 1.95 | 1.8484 | False | 3 | 0.1195 | 0.3585 | False | False | False
DDR_CAB3 | DDR_DQA12 | B_ADDRESS_COMMAND | A_BYTE1 | L8 | all_inner_layer_traces | track:DDR_CAB3:L8:695:21 | track:DDR_DQA12:L8:688:10 | 1.95 | 1.8484 | False | 3 | 0.1195 | 0.3585 | False | False | False
DDR_CAB3 | DDR_DQA13 | B_ADDRESS_COMMAND | A_BYTE1 | L8 | actual_interconnect_only | track:DDR_CAB3:L8:695:21 | track:DDR_DQA13:L8:693:12 | 2.6 | 2.4984 | False | 3 | 0.1195 | 0.3585 | False | False | False
DDR_CAB3 | DDR_DQA13 | B_ADDRESS_COMMAND | A_BYTE1 | L8 | all_inner_layer_traces | track:DDR_CAB3:L8:695:21 | track:DDR_DQA13:L8:693:12 | 2.6 | 2.4984 | False | 3 | 0.1195 | 0.3585 | False | False | False
DDR_CAB3 | DDR_DQA14 | B_ADDRESS_COMMAND | A_BYTE1 | L8 | actual_interconnect_only | track:DDR_CAB3:L8:695:4 | track:DDR_DQA14:L8:683:3 | 4.5507253886 | 4.4491253886 | False | 3 | 0.1195 | 0.3585 | False | False | False
DDR_CAB3 | DDR_DQA14 | B_ADDRESS_COMMAND | A_BYTE1 | L8 | all_inner_layer_traces | track:DDR_CAB3:L8:695:4 | track:DDR_DQA14:L8:683:3 | 4.5507253886 | 4.4491253886 | False | 3 | 0.1195 | 0.3585 | False | False | False
DDR_CAB3 | DDR_DQA15 | B_ADDRESS_COMMAND | A_BYTE1 | L8 | actual_interconnect_only | track:DDR_CAB3:L8:695:4 | track:DDR_DQA15:L8:698:0 | 4.9715440258 | 4.8699440258 | False | 3 | 0.1195 | 0.3585 | False | False | False
DDR_CAB3 | DDR_DQA15 | B_ADDRESS_COMMAND | A_BYTE1 | L8 | all_inner_layer_traces | track:DDR_CAB3:L8:695:4 | track:DDR_DQA15:L8:698:0 | 4.9715440258 | 4.8699440258 | False | 3 | 0.1195 | 0.3585 | False | False | False
DDR_CAB3 | DDR_DQA3 | B_ADDRESS_COMMAND | A_BYTE0 | L8 | actual_interconnect_only | track:DDR_CAB3:L8:695:3 | track:DDR_DQA3:L8:649:1 | 4.0625 | 3.9609 | False | 3 | 0.1195 | 0.3585 | False | False | False
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
