oliverkirk-sudo/k230-c/project/recovery/r10-dnp-paste-policy/recovered-fixture/R7_AUTHORITATIVE_ALIASES_REVIEW_ONLY.kicad_pcb

## KiCad design project/recovery/r10-dnp-paste-policy/recovered-fixture/R7_AUTHORITATIVE_ALIASES_REVIEW_ONLY.kicad_pcb (2026-10-03)

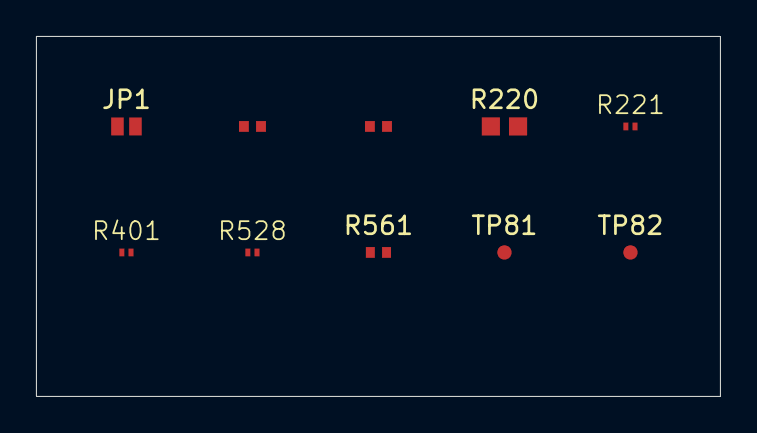
[picture p6: board R7_AUTHORITATIVE_ALIASES_REVIEW_ONLY.kicad_pcb from above]

Board: 6 copper layers, 38.0 x 20.0 mm, 10 parts (0 on the bottom side), 3 nets, no tracks yet.

Parts:
JP1: OPEN=EMMC / CLOSED=TF; COLD ONLY; Core_Cold_Selector_Open_SolderBridge_CANDIDATE
R205, R206: 56.2k 1% / 0.8V / addr0x49; Vishay_TNPW0402_IPC7351_SourceLand_PROCESS_CANDIDATE
R220: 0R WSL060300000ZEA9 Rmax=0.25mOhm; Vishay_WSL0603_9_SourceLand_PROCESS_CANDIDATE
R221: 0R Rmax<=50mOhm; Vishay_CRCW0201_SourceLand_PROCESS_CANDIDATE
R401: 0R PMU AUTO-START STRAP; Vishay_CRCW0201_SourceLand_PROCESS_CANDIDATE
R528: 0R QUALIFICATION STRAP DNP; Vishay_CRCW0201_SourceLand_PROCESS_CANDIDATE
R561: 0R WFZ040200000ZE66 3mOhm CANDIDATE; Vishay_WFZ0402_SourceLand_PROCESS_CANDIDATE
TP81: PMU OUT0 OBSERVE ONLY; Core_PMUSTATUS_Top_TestPad_0p8_CANDIDATE
TP82: PMU OUT1 OBSERVE ONLY; Core_PMUSTATUS_Top_TestPad_0p8_CANDIDATE

Connections:
GND: R205.2, R206.2
VDD1P8: R528.1, R561.1
VDD_3V3: JP1.2, R221.1
