oliverkirk-sudo/k230-c/project/tools/generate_crystal_footprint.py

#!/usr/bin/env python3
from pathlib import Path
import json,hashlib
B=Path(__file__).resolve().parents[1];o=B/'cad/verified-footprints/crystals';name='YXC_X322524MOB4SI_3225_4P_DrawingCandidate'
s=[f'(footprint "{name}" (version 20241229) (generator "cmk230_crystal_review") (layer "F.Cu") (attr smd)', '(descr "YXC manufacturer RevB0 p3 suggested lands; mask/paste/courtyard are project process assumptions. NOT RELEASED.")', '(property "Reference" "REF**" (at 0 -2.3) (layer "F.SilkS") (effects (font (size .8 .8) (thickness .12))))','(property "Value" "X322524MOB4SI" (at 0 2.4) (layer "F.Fab") (effects (font (size .6 .6) (thickness .1))))','(fp_rect (start -1.6 -1.25) (end 1.6 1.25) (stroke (width .1) (type default)) (fill none) (layer "F.Fab"))','(fp_rect (start -2.1 -1.75) (end 2.1 1.75) (stroke (width .05) (type default)) (fill none) (layer "F.CrtYd"))','(fp_circle (center -2.05 1.25) (end -1.95 1.25) (stroke (width .1) (type default)) (fill none) (layer "F.SilkS"))']
for p,x,y in [('1',-1.1,.85),('2',1.1,.85),('3',1.1,-.85),('4',-1.1,-.85)]:s.append(f'(pad "{p}" smd rect (at {x} {y}) (size 1.4 1.2) (layers "F.Cu" "F.Paste" "F.Mask") (solder_mask_margin .05))')
s.append(')');(o/'CMK230_Crystals.pretty'/f'{name}.kicad_mod').write_text('\n'.join(s))
(o/'geometry-source.json').write_text(json.dumps({'part':'X322524MOB4SI','source':'https://atta.szlcsc.com/upload/public/pdf/source/20230512/FCFA71FC9F356FF871B9CC5C5DAC5D5F.pdf','manufacturer_revision':'B.0 2022-03-01','page':3,'body_nominal_mm':[3.2,2.5,.7],'body_tolerance_mm':[.1,.1,.1],'pad_mm':[1.4,1.2],'centers_x_mm':[-1.1,1.1],'centers_y_mm':[-.85,.85],'top_view_pin_map':{'1':'bottom-left crystal','2':'bottom-right ground','3':'top-right crystal','4':'top-left ground'},'process_assumptions':{'mask_expansion_mm':.05,'paste':'1:1 unqualified','courtyard_mm':[4.2,3.5]},'status':'DRAWING_CANDIDATE_NOT_RELEASED'},indent=2))
